MasaoC/GPS-TFT-Map_PONS/mysd.cpp

// ============================================================
// File    : mysd.cpp
// Project : PONS v7 (Pilot Oriented Navigation System for HPA)
// Role    : SDカード操作の実装（全処理はCore1で実行）。
//           SdFatライブラリによるファイル読み書き、
//           設定ファイル保存/読込、CSVフライトログ追記、
//           飛行CSVのリプレイ再生（列名索引パーサ・先読みリングバッファ）、
//           Core1タスクキューのエンキュー/デキュー管理。
//           地図画像(BMPタイル)のロードはベクタ地図への移行に伴い廃止した。
// Author  : MasaoC (@masao_mobile)
// Updated : 2026/10/06
// ============================================================
// SD card read and write programs.
// All process regarding SD card access are done in Core1.(#2 core)

#include <SPI.h>

#include "mysd.h"
#include "navdata.h"
#include "gnss.h"      // gnss_get_own_fix()（received/ に自機位置と距離を書くため）
#include "settings.h"
#include "imu.h"
//#define DISABLE_FS_H_WARNING
#include "SdFat.h"
#include "src/sound.h"
#include "attitude.h"
#include "link.h"

#define MAX_SETTING_LENGTH 32
#define MAX_LINE_LENGTH (MAX_SETTING_LENGTH * 2 + 2) // ID:value ペア + 区切り文字・改行のバッファサイズ


SdFs SD;                     // SdFat ライブラリのファイルシステムオブジェクト
volatile bool sdInitialized = false;  // SD カードの初期化が完了しているか（Core0/Core1 両方から参照）
volatile bool sdError = false;        // SD アクセス中にエラーが発生したか（Core0/Core1 両方から参照）
volatile bool sd_setup_complete = false;  // Core1 の setup_sd() が完了したことを示すフラグ（Core0 が待機に使用）
#define LOGFILE_NAME "log.txt"

// ---- 処理時間計測変数（BNO085配置コア決定用、デバッグビルドのみ） ----
#ifndef RELEASE
TimingStat ts_savecsv_flush = TSTAT_INIT("C1_savecsv_flush");
extern volatile bool c0_is_redrawing;  // Core0 描画中フラグ（重複検出用）
volatile uint32_t _c1_overlap_count = 0;  // Core0描画中にCore1重処理が重なった回数（Core1 が加算、Core0 が表示）
#endif

unsigned long lasttrytime_sd = 0; // SD エラー時の最後の再試行時刻（10秒ごとにリトライする）
bool headerWritten = false;       // CSV ファイルにヘッダ行を書いたか（1フライト1回だけ書く）

// CSV ファイル名の生成に使う起動時の日時（初回書き込み時に確定する）
int fileyear = 0;//意図的に0で初期化して、最初のGNSS時刻取得時に確定させる。変えるな。
int filemonth;
int fileday;
int filehour;
int fileminute;
int filesecond;


// ============================================================
// Core0↔Core1 間タスクキュー（ミューテックス保護）
//
// Core0（表示・GNSS・ボタン）から Core1（SD・音声）へ
// 非同期で処理を依頼するためのリングバッファ。
//   - enqueueTask(): Core0 がタスクを積む
//   - dequeueTask(): Core1 がタスクを取り出して実行
//   - taskQueueMutex でアトミック操作を保証
// ============================================================
TaskQueue taskQueue;               // タスクのリングバッファ本体
mutex_t taskQueueMutex;            // タスクキューへのアクセスを保護するミューテックス
Task currentTask;                  // Core1 が現在実行中のタスク（isTaskRunning() で参照）


void log_sd(const char* text);
void log_sdf(const char* format, ...);
void dateTime(uint16_t* date, uint16_t* time);



// ============================================================
// SD カード設定ファイル（settings.txt）の管理
//
// ファイル形式: テキスト、1 行に 1 項目、"id:value\n" の形式
//   例:
//     volume:50
//     destination:PLATHOME
//     navigation_mode:INTO
//     scaleindex:2
//
// SDSetting 構造体が id（識別子文字列）と setter/getter を持ち、
// loadSettings() / saveSettings() がこのテーブルを走査して一括処理する。
// 新しい設定項目を追加するときはこの配列に 1 行追加するだけでよい。
// ============================================================
// ---- PONS Link（機体⇄ボート無線）----
// 電波の ch / profile は「数値を保存するだけ」で、意味は無線層（e220.cpp）が決める。
// LoRa では ch = E220 のチャネル(CH0-12)、profile = SF のプリセット(0=SF7 … 4=SF11)。
void getLinkMode(char* b, size_t n)      { snprintf(b, n, "%u", link_mode_setting); }
void setLinkMode(const char* v) {
  int m = atoi(v);
  // 壊れた設定ファイルで機体が勝手に受信モードになる事故を防ぐため、
  // 範囲外は必ず OFF に倒す（docs/pons_link.md §1）。
  link_mode_setting = (m >= 0 && m <= LINK_MODE_RX) ? (uint8_t)m : LINK_MODE_OFF;
}
void getLinkRadioCh(char* b, size_t n)   { snprintf(b, n, "%u", link_radio_ch); }
void setLinkRadioCh(const char* v) {
  int c = atoi(v);
  if (c >= 0 && c <= LINK_RADIO_CH_MAX) link_radio_ch = (uint8_t)c;
}
void getLinkRadioProf(char* b, size_t n) { snprintf(b, n, "%u", link_radio_profile); }
void setLinkRadioProf(const char* v) {
  int p = atoi(v);
  if (p >= 0 && p < LINK_PROFILE_COUNT) link_radio_profile = (uint8_t)p;
}

// ★ グループ ID。**既定は 0 で、git に載る雛形も 0 のまま。**
//   実際の値は各機の SD カードにだけ置く（link_proto.h の設計方針）。
void getLinkGroup(char* b, size_t n)     { snprintf(b, n, "%u", link_group); }
void setLinkGroup(const char* v) {
  int g = atoi(v);
  link_group = (g >= 0 && g <= LINK_GROUP_MAX) ? (uint8_t)g : LINK_GROUP_DEFAULT;
}

SDSetting settings[] = {
  {"volume",          setVolume,         getVolume},
  {"vario_volume",    setVarioVolume,    getVarioVolume},
  {"vario_inhibit",   setVarioInhibit,   getVarioInhibit},
  {"destination",     setDestination,    getDestination},
  {"navigation_mode", setNavigationMode, getNavigationMode},
  {"scaleindex",      setScaleIndex,     getScaleIndex},
  {"upward_mode",     setUpwardMode,     getUpwardMode},
  {"kf_q_vel",        setKfQVel,         getKfQVel},
  {"kf_q_bias",       setKfQBias,        getKfQBias},
  {"kf_R",            setKfR,            getKfR},
  {"level_roll",      setLevelRoll,      getLevelRoll},
  {"level_pitch",     setLevelPitch,     getLevelPitch},
  {"pitch_target",    setPitchTarget,    getPitchTarget},
  {"rpy_functions",   setRpyFunctions,   getRpyFunctions},
  {"auto_roll_trim",  setAutoRollTrim,   getAutoRollTrim},
  {"wind_estimate",   setWindEstimate,   getWindEstimate},
  {"roll_target",     setRollTarget,     getRollTarget},
  {"needs_apply",     setNeedsApply,     getNeedsApply},
  {"calib_date",      setCalibDate,      getCalibDate},
  {"airspeed_v0",     setAirspeedV0,     getAirspeedV0},
  {"airspeed_k",      setAirspeedK,      getAirspeedK},
  {"airspeed_min",    setAirspeedMin,    getAirspeedMin},
  {"airspeed_max",    setAirspeedMax,    getAirspeedMax},
  {"roll_trim",       setRollTrim,       getRollTrim},
  {"auto10k_status",  setAuto10kStatus,  getAuto10kStatus},
  {"link_mode",       setLinkMode,       getLinkMode},
  {"link_radio_ch",   setLinkRadioCh,    getLinkRadioCh},
  {"link_radio_prof", setLinkRadioProf,  getLinkRadioProf},
  {"link_group",      setLinkGroup,      getLinkGroup}
};
const int numSettings = sizeof(settings) / sizeof(settings[0]);
extern volatile int sound_volume;
extern volatile int vario_volume;
extern volatile bool vario_inhibit;
extern int destination_mode;
extern volatile int scaleindex;  // 実体は GPS_TFT_map.ino（volatile）。宣言側も合わせる
extern double scalelist[6];
extern double scale;
extern int upward_mode;  // display_tft.cpp で定義。0=TRACKUP, 1=NORTHUP


// 全設定を settings.txt に保存する。
// 一度ファイルを削除してから新規書き込みすることで、
// 古い項目が残らないようにしている。
bool saveSettings() {
  SD.remove("settings.txt"); // 古いファイルを消してから書き直す
  FsFile file = SD.open("settings.txt", FILE_WRITE);
  if (!file) {
    DEBUGW_PLN(20250401,"Failed to open settings.txt for writing");
    return false;
  }

  char value[MAX_SETTING_LENGTH];
  for (int i = 0; i < numSettings; i++) {
    settings[i].getter(value, MAX_SETTING_LENGTH);
    file.print(settings[i].id);
    file.print(":");
    file.print(value);
    file.print("\n");//
  }

  file.close();
  DEBUG_PLN(20250401,"Settings saved to settings.txt");
  return true;
}


// settings.txt から設定を読み込み、各 setter を呼んで反映する。
// ファイルを 1 文字ずつ読んで行を組み立て、"id:value" 形式でパースする。
// ファイル末尾に改行がない場合も処理できるよう、ループ後に残余バッファをチェックする。
bool loadSettings() {
  FsFile file = SD.open("settings.txt", FILE_READ);
  if (!file) {
    DEBUGW_PLN(20250401,"Failed to open settings.txt for reading");
    return false;
  }

  char line[MAX_LINE_LENGTH];
  char settingId[MAX_SETTING_LENGTH];
  char value[MAX_SETTING_LENGTH];
  int linePos = 0;

  while (file.available()) {
    char c = file.read();
    // ★ CR も行の終わりとして扱う。**settings.txt は人が PC で編集する**
    //   （link_group など）ので、Windows のエディタが CRLF で保存すると値の末尾に
    //   \r が残る。atoi() を通す設定は無事だが、strcmp で比べるものが全部外れて
    //   ナビモード・目的地・vario_inhibit が黙って既定へ戻っていた。
    //   CRLF なら \r で行を切り、続く \n は空行（コロン無し）として捨てられる。
    if (c == '\n' || c == '\r' || linePos >= MAX_LINE_LENGTH - 1) {
      line[linePos] = '\0'; // Null-terminate the line
      linePos = 0;

      // Parse line into settingId and value
      char* colon = strchr(line, ':');
      if (colon) {
        *colon = '\0'; // Split at colon
        strncpy(settingId, line, MAX_SETTING_LENGTH);
        settingId[MAX_SETTING_LENGTH - 1] = '\0';
        strncpy(value, colon + 1, MAX_SETTING_LENGTH);
        value[MAX_SETTING_LENGTH - 1] = '\0';

        // Find and apply the setting
        for (int i = 0; i < numSettings; i++) {
          if (strcmp(settings[i].id, settingId) == 0) {
            settings[i].setter(value);
            break;
          }
        }
      }
    } else {
      line[linePos++] = c;
    }
  }



  // Handle last line if not newline-terminated
  if (linePos > 0) {
    line[linePos] = '\0';
    char* colon = strchr(line, ':');
    if (colon) {
      *colon = '\0';
      strncpy(settingId, line, MAX_SETTING_LENGTH);
      settingId[MAX_SETTING_LENGTH - 1] = '\0';
      strncpy(value, colon + 1, MAX_SETTING_LENGTH);
      value[MAX_SETTING_LENGTH - 1] = '\0';

      for (int i = 0; i < numSettings; i++) {
        if (strcmp(settings[i].id, settingId) == 0) {
          settings[i].setter(value);
          break;
        }
      }
    }
  }

  file.close();
  // 設定どうしの整合を取る（roll_trim と needs_apply の関係など）。
  // 行の順序に依存しないよう、全部読み終えてから呼ぶ。
  attitude_finish_settings_load();
  DEBUG_PLN(20250508,"Settings loaded from settings.txt");
  return true;
}



// ============================================================
// 設定項目ごとの setter / getter の実装
// setter: 文字列を受け取り、該当するグローバル変数に変換・格納する。
// getter: グローバル変数を文字列に変換して buffer に書き込む。
// ============================================================

// ============================================================
//  settings.txt の値を読む（検証つき）
// ============================================================
// ★ **atoi() / atof() を直接使ってはいけない。** どちらも数字でない文字列に 0 を返す。
//   音量では 0 が「消音」、角度では 0 がまっとうな値なので、行が壊れているだけなのに
//   黙って音が消える／ゼロ点が失われる。PONS は警報装置なので、これは一番避けたい。
//
// ★ **範囲外を丸めたときも必ずログに残す。** 丸めた結果がたまたま正常な値に見えると
//   （volume:-5 → 0 = 消音）、設定ミスに現場で気づけない。
//   「読めなかった」と「丸めた」を区別して log.txt へ書く。
//
// 戻り値: その値を採用してよいか（false = 既定値のまま残す）
static bool read_setting_int(const char* id, const char* value, int lo, int hi, int* out) {
  char* end = nullptr;
  const long v = strtol(value, &end, 10);
  if (end == value) {                               // 数字が 1 文字も無い
    enqueueTask(createLogSdfTask("ERR %s(%s) not a number", id, value));
    return false;
  }
  // 末尾の空白は許す。CR/LF は loadSettings() が行の区切りとして落としているが、
  // ここだけ見ても正しく動くようにしておく（保険）。
  while (*end == ' ' || *end == '\t' || *end == '\r' || *end == '\n') end++;
  if (*end != '\0') {                               // 数字のあとにゴミが付いている
    enqueueTask(createLogSdfTask("ERR %s(%s) not a number", id, value));
    return false;
  }
  if (v < lo || v > hi) {
    *out = (int)(v < lo ? lo : hi);
    enqueueTask(createLogSdfTask("ERR %s(%s) range %d..%d -> %d", id, value, lo, hi, *out));
    return true;                                    // 丸めた値は使う（捨てるより素直）
  }
  *out = (int)v;
  return true;
}

// 同じく float 版。角度の設定はこちらを通す。
// ★ strtod() は "nan" / "inf" を**正しくパースしてしまう**ので明示的に弾く。
//   NaN はどの比較も false になるため、しきい値の警告に一つも引っかからないまま
//   姿勢機能だけが死ぬ。範囲のクランプは attitude.cpp 側にもあるが（将来の
//   呼び出し元への保険）、ログを出せるのはここだけなので範囲もここで見る。
static bool read_setting_float(const char* id, const char* value, float lo, float hi, float* out) {
  char* end = nullptr;
  const double v = strtod(value, &end);
  bool bad = (end == value);
  if (!bad) {
    while (*end == ' ' || *end == '\t' || *end == '\r' || *end == '\n') end++;
    if (*end != '\0') bad = true;                   // 数字のあとにゴミ
    else if (v != v)   bad = true;                  // NaN
    else if (v > 1e30 || v < -1e30) bad = true;     // ±inf / 桁あふれ
  }
  if (bad) {
    enqueueTask(createLogSdfTask("ERR %s(%s) not a number", id, value));
    return false;
  }
  if (v < lo || v > hi) {
    *out = (float)(v < lo ? lo : hi);
    enqueueTask(createLogSdfTask("ERR %s(%s) range %.2f..%.2f -> %.2f",
                                 id, value, (double)lo, (double)hi, (double)*out));
    return true;
  }
  *out = (float)v;
  return true;
}

// 音量: 0〜SOUND_VOLUME_MAX。読めない値は既定値のまま残す（上のコメント参照）。
void setVolume(const char* value) {
  int v;
  if (!read_setting_int("volume", value, 0, SOUND_VOLUME_MAX, &v)) return;
  sound_volume = v;
  DEBUG_P(20250508,"Set volume to: ");
  DEBUG_PLN(20250508,sound_volume);
}

void getVolume(char* buffer, size_t bufferSize) {
  snprintf(buffer, bufferSize, "%d", sound_volume);
}

// バリオメーター音量: 0〜SOUND_VOLUME_MAX。こちらも読めない値は既定値のまま。
void setVarioVolume(const char* value) {
  int v;
  if (!read_setting_int("vario_volume", value, 0, SOUND_VOLUME_MAX, &v)) return;
  vario_volume = v;
}

void getVarioVolume(char* buffer, size_t bufferSize) {
  snprintf(buffer, bufferSize, "%d", vario_volume);
}

// バリオ抑止フラグ: "true" なら vario を完全無効化する（SDカード手動設定のみ）
void setVarioInhibit(const char* value) {
  vario_inhibit = (strcmp(value, "true") == 0);
}
void getVarioInhibit(char* buffer, size_t bufferSize) {
  snprintf(buffer, bufferSize, "%s", vario_inhibit ? "true" : "false");
}

// ナビゲーションモード: "INTO" / "AWAY" / "AUTO10K" を destination_mode 定数に変換
void setNavigationMode(const char *value){
  if(strcmp(value,"INTO") == 0){
    destination_mode = DMODE_FLYINTO;
  }
  else if(strcmp(value,"AWAY") == 0){
    destination_mode = DMODE_FLYAWAY;
  }
  else if(strcmp(value,"AUTO10K") == 0){
    destination_mode = DMODE_AUTO10K;
  }else{
    DEBUGW_PLN(20250509,"ERR MODE");
  }
}
void getNavigationMode(char* buffer, size_t bufferSize) {
  if(bufferSize <= 0)
    return;
  if(destination_mode == DMODE_FLYINTO)
    strncpy(buffer,"INTO", bufferSize);
  else if(destination_mode == DMODE_FLYAWAY)
    strncpy(buffer,"AWAY", bufferSize);
  else if(destination_mode == DMODE_AUTO10K)
    strncpy(buffer,"AUTO10K", bufferSize);
  buffer[bufferSize - 1] = '\0';
}

// 目的地: 名前で extradestinations を線形探索して currentdestination インデックスを設定する。
// 見つからない場合はエラーログを残す。
void setDestination(const char* value) {
  for(int i = 0; i < destinations_count; i++){
    if(strcmp(extradestinations[i].name,value) == 0){
      currentdestination = i;
      return;
    }
  }
  DEBUGW_P(20250508,"ERR DEST:");
  DEBUGW_PLN(20250508,value);
  enqueueTask(createLogSdfTask("ERR setDestination(%s)",value));
}


void getScaleIndex(char* buffer, size_t bufferSize) {
  if(bufferSize <= 0)
    return;
  snprintf(buffer, bufferSize, "%d", scaleindex);
}

void setScaleIndex(const char* value) {
  int indexofsetting = atoi(value);
  if(indexofsetting >= 0 && indexofsetting < (sizeof(scalelist) / sizeof(scalelist[0]))){
    scaleindex = indexofsetting;
    scale = scalelist[scaleindex];
  }else{
    DEBUGW_P(20250508,"ERR scale index:");
    DEBUGW_PLN(20250508,indexofsetting);
    enqueueTask(createLogSdfTask("ERR scale index(%s)",value));
  }
}

// 地図方向モード（NORTHUP=1 / TRACKUP=0）の getter / setter
void getUpwardMode(char* buffer, size_t bufferSize) {
  if (bufferSize <= 0) return;
  snprintf(buffer, bufferSize, "%d", upward_mode);
}

void setUpwardMode(const char* value) {
  int mode = atoi(value);
  if (mode >= 0 && mode < 2) {  // 0=TRACKUP, 1=NORTHUP
    upward_mode = mode;
  }
}

// Kalman フィルター係数: 速度プロセスノイズ（デフォルト KF_Q_VEL）
void setKfQVel(const char* value) {
  float v = atof(value);
  if (v > 0.0f) imu_set_kf_params(v, get_imu_kf_q_bias(), get_imu_kf_R());
}
void getKfQVel(char* buffer, size_t bufferSize) {
  snprintf(buffer, bufferSize, "%.6g", get_imu_kf_q_vel());
}

// Kalman フィルター係数: バイアスプロセスノイズ（デフォルト KF_Q_BIAS）
void setKfQBias(const char* value) {
  float v = atof(value);
  if (v > 0.0f) imu_set_kf_params(get_imu_kf_q_vel(), v, get_imu_kf_R());
}
void getKfQBias(char* buffer, size_t bufferSize) {
  snprintf(buffer, bufferSize, "%.6g", get_imu_kf_q_bias());
}

// Kalman フィルター係数: 気圧高度観測ノイズ [m²]（デフォルト KF_R）
void setKfR(const char* value) {
  float v = atof(value);
  if (v > 0.0f) imu_set_kf_params(get_imu_kf_q_vel(), get_imu_kf_q_bias(), v);
}
void getKfR(char* buffer, size_t bufferSize) {
  snprintf(buffer, bufferSize, "%.6g", get_imu_kf_R());
}

// ---- 機体ゼロ点（マウント基準）のオフセット [度] ----
// マウント形状は固定なので、据え付け後に一度較正すれば以後は使い回せる。
// 設定画面の "Set Level 0deg" で更新し、ここで SD に永続化する。
void setLevelRoll(const char* value) {
  float v;
  if (!read_setting_float("level_roll", value,
                          -LEVEL_OFFSET_LIMIT_DEG, LEVEL_OFFSET_LIMIT_DEG, &v)) return;
  float r, p;
  attitude_get_level_offset(r, p);
  attitude_set_level_offset(v, p);
}
void getLevelRoll(char* buffer, size_t bufferSize) {
  float r, p; attitude_get_level_offset(r, p);
  snprintf(buffer, bufferSize, "%.3f", r);
}
void setLevelPitch(const char* value) {
  float v;
  if (!read_setting_float("level_pitch", value,
                          -LEVEL_OFFSET_LIMIT_DEG, LEVEL_OFFSET_LIMIT_DEG, &v)) return;
  float r, p;
  attitude_get_level_offset(r, p);
  attitude_set_level_offset(r, v);
}

// 較正時に申告するピッチ角（IMU/ESKF 画面の SET PITCH 行の値）。
// 本番プラットホームは -3.5 度など決まった値を使うので、
// 毎回選び直さずに済むよう保存する。
void setPitchTarget(const char* value) {
  float v;
  if (!read_setting_float("pitch_target", value,
                          PITCH_TARGET_MIN_DEG, PITCH_TARGET_MAX_DEG, &v)) return;
  attitude_set_pitch_target(v);
}

// APPLY 時に申告するロール角（通常 0）
void setRollTarget(const char* value) {
  float v;
  if (!read_setting_float("roll_target", value,
                          ROLL_TARGET_MIN_DEG, ROLL_TARGET_MAX_DEG, &v)) return;
  attitude_set_roll_target(v);
}
void getRollTarget(char* buffer, size_t bufferSize) {
  snprintf(buffer, bufferSize, "%.1f", attitude_get_roll_target());
}

// マウントから外されたまま APPLY されていない状態。
// 充電のために電源を切っても保持したいので SD に残す。
void setNeedsApply(const char* value) { attitude_set_needs_apply(atoi(value) != 0); }
// 自動ロールトリムの累積補正量。取り付けのズレは電源を切っても変わらないので保存する。
// ただし needs_apply が立っている（マウントから外した）場合は
// attitude_finish_settings_load() が読み込み後に捨てる。
void setRollTrim(const char* value) {
  float v;
  if (!read_setting_float("roll_trim", value,
                          -ROLL_TRIM_LIMIT_DEG, ROLL_TRIM_LIMIT_DEG, &v)) return;
  attitude_set_roll_trim_deg(v);
}
// AUTO10K の折返しフェーズ。飛行中に再起動しても復路のナビ方位が 180 度逆に
// ならないよう保存する（距離だけでは往路と復路を区別できないため）。
// 保存されるのは実飛行の遷移だけで、リプレイ再生中の遷移は書き込まれない。
void setAuto10kStatus(const char* value) {
  restore_auto10k_status(strcmp(value, "INTO") == 0 ? AUTO10K_INTO : AUTO10K_AWAY);
}
void getAuto10kStatus(char* buffer, size_t bufferSize) {
  strncpy(buffer, get_auto10k_status_flight() == AUTO10K_INTO ? "INTO" : "AWAY", bufferSize);
  buffer[bufferSize - 1] = '\0';
}
void getRollTrim(char* buffer, size_t bufferSize) {
  snprintf(buffer, bufferSize, "%.3f", attitude_get_roll_trim_deg());
}
void getNeedsApply(char* buffer, size_t bufferSize) {
  snprintf(buffer, bufferSize, "%d", attitude_needs_apply() ? 1 : 0);
}

// 最後に APPLY した日（JST の YYYYMMDD、0 = 不明）。
// これを保存する目的は「電源を切っている間にマウントから外された」を拾うこと。
// OFF_MOUNT 判定は ESKF が回っている間しか働かないので、電源 OFF 中の取り外しは
// needs_apply には現れない。日付だけは残しておけば、次の起動で日をまたいだと分かる。
// 値の妥当性検査は attitude_set_calib_date() 側で行う（壊れた設定ファイル対策）。
void setCalibDate(const char* value) {
  attitude_set_calib_date((uint32_t)strtoul(value, nullptr, 10));
}
void getCalibDate(char* buffer, size_t bufferSize) {
  snprintf(buffer, bufferSize, "%lu", (unsigned long)attitude_get_calib_date());
}

// ---- 対気速度の推定モデル V(θ) = V0 * sqrt(K / (K + θ)) ----
// 機体・重量・重心で変わるので、機体ごとに SD で設定できるようにしてある。
// 既定は settings.h の AIRSPEED_*。範囲外は read_setting_float() が端でクランプし、
// 理由を log.txt に残す（黙って既定へ戻すと、書いたつもりで効いていない状態になる）。
// 読み込み後の実効値は setup_sd() が AIRSPEED MODEL 行としてログに残す。
//
// ★ 範囲は「人力飛行機として明らかにあり得ない値を弾く」ためのもので、
//   細かい調整を妨げない広さにしてある。
//   airspeed_k は 0 に近づけると分母が消えて発散するので下限を離してある。
void setAirspeedV0(const char* value) {
  float v;
  if (read_setting_float("airspeed_v0", value, 3.0f, 20.0f, &v))
    attitude_set_airspeed_v0(v);
}
void getAirspeedV0(char* buffer, size_t bufferSize) {
  snprintf(buffer, bufferSize, "%.2f", attitude_get_airspeed_v0());
}
void setAirspeedK(const char* value) {
  float v;
  if (read_setting_float("airspeed_k", value, 3.0f, 60.0f, &v))
    attitude_set_airspeed_k(v);
}
void getAirspeedK(char* buffer, size_t bufferSize) {
  snprintf(buffer, bufferSize, "%.2f", attitude_get_airspeed_k());
}
void setAirspeedMin(const char* value) {
  float v;
  if (read_setting_float("airspeed_min", value, 1.0f, 20.0f, &v))
    attitude_set_airspeed_min(v);
}
void getAirspeedMin(char* buffer, size_t bufferSize) {
  snprintf(buffer, bufferSize, "%.2f", attitude_get_airspeed_min());
}
void setAirspeedMax(const char* value) {
  float v;
  if (read_setting_float("airspeed_max", value, 1.0f, 25.0f, &v))
    attitude_set_airspeed_max(v);
}
void getAirspeedMax(char* buffer, size_t bufferSize) {
  snprintf(buffer, bufferSize, "%.2f", attitude_get_airspeed_max());
}

// Roll/Pitch/Yaw 機能のマスタースイッチ（IMU/ESKF 画面で切替）
void setRpyFunctions(const char* value) { attitude_set_rpy_enabled(atoi(value) != 0); }
void getRpyFunctions(char* buffer, size_t bufferSize) {
  snprintf(buffer, bufferSize, "%d", attitude_get_rpy_enabled() ? 1 : 0);
}

// 風推定の有効/無効
void setWindEstimate(const char* value) { attitude_set_wind_enabled(atoi(value) != 0); }
void getWindEstimate(char* buffer, size_t bufferSize) {
  snprintf(buffer, bufferSize, "%d", attitude_get_wind_enabled() ? 1 : 0);
}

// 直進中のロール自動トリムの有効/無効
void setAutoRollTrim(const char* value) { attitude_set_roll_trim_enabled(atoi(value) != 0); }
void getAutoRollTrim(char* buffer, size_t bufferSize) {
  snprintf(buffer, bufferSize, "%d", attitude_get_roll_trim_enabled() ? 1 : 0);
}
void getPitchTarget(char* buffer, size_t bufferSize) {
  snprintf(buffer, bufferSize, "%.1f", attitude_get_pitch_target());
}
void getLevelPitch(char* buffer, size_t bufferSize) {
  float r, p; attitude_get_level_offset(r, p);
  snprintf(buffer, bufferSize, "%.3f", p);
}

void getDestination(char* buffer, size_t bufferSize) {
  if(bufferSize <= 0)
    return;
  // 目的地が未選択（起動直後は -1）なら配列外アクセスになるため空文字列を返す
  if(currentdestination < 0 || currentdestination >= destinations_count){
    buffer[0] = '\0';
    return;
  }
  strncpy(buffer, extradestinations[currentdestination].name, bufferSize);
  buffer[bufferSize - 1] = '\0';
}


// 現在 Core1 が実行中のタスクが指定タイプかを確認する（Core0 から呼ばれる）。
// currentTask は dequeueTask() が mutex 内で丸ごと上書きするため、読む側も mutex で揃える。
bool isTaskRunning(int taskType) {
  mutex_enter_blocking(&taskQueueMutex);
  bool running = (currentTask.type == taskType);
  mutex_exit(&taskQueueMutex);
  return running;
}

// Core1 がタスクを処理し終えたことを記録する（mutex 内で書くことで isTaskRunning() と整合させる）
void clearCurrentTask() {
  mutex_enter_blocking(&taskQueueMutex);
  currentTask.type = TASK_NONE;
  mutex_exit(&taskQueueMutex);
}

// キュー内に指定タイプのタスクが存在するかを確認する（head〜tail を線形探索）。
// ループ内で return せず found に受けてから抜ける（mutex の解放漏れを防ぐため）。
bool isTaskInQueue(int taskType){
    bool found = false;
    mutex_enter_blocking(&taskQueueMutex);
    int current = taskQueue.head;
    while (current != taskQueue.tail) {
        if (taskQueue.tasks[current].type == taskType) {
            found = true;
            break;
        }
        current = (current + 1) % TASK_QUEUE_SIZE;
    }
    mutex_exit(&taskQueueMutex);
    return found;
}

// ============================================================
// タスク生成ファクトリ関数（create〜Task）
//
// 各タスクは Task 構造体として表現され、
// type フィールドで種別を識別し、union のフィールドで引数を渡す。
// Core0 がこれらを呼んで enqueueTask() に渡し、Core1 がデキューして実行する。
// ============================================================

// 設定ファイル保存タスクを生成する
Task createSaveSettingTask(){
  Task task;
  task.type = TASK_SAVE_SETTINGS;
  return task;
}


// テキストをログファイルに書き込むタスクを生成する
Task createLogSdTask(const char* logText) {
  Task task;
  task.type = TASK_LOG_SD;
  task.logText = logText;
  return task;
}

// printf 形式のフォーマット文字列でログタスクを生成する（可変引数対応）
Task createLogSdfTask(const char* format, ...) {
  Task task;
  task.type = TASK_LOG_SDF;
  va_list args;
  va_start(args, format);
  vsnprintf(task.logSdfArgs.buffer, sizeof(task.logSdfArgs.buffer), format, args);
  va_end(args);
  task.logSdfArgs.format = "%s";
  return task;
}


// 無線で受信した 1 フレームを received/ へ書き出すタスクを生成する。
// 自機のフライト CSV とは**別のファイル・別のハンドル**にしてある。
//
// ★ 「received/ には無線で得た情報だけ」という原則の**唯一の例外**として、
//   受信した瞬間のボート自身の位置（own_lat/own_lon）と機体までの距離（dist_m）を
//   同じ行に入れる。RSSI と距離が 1 行に揃っていないと「距離 vs RSSI」が引けず、
//   別ファイルに分けると seq で突き合わせる手間が増えるため。
//   リプレイは列名で解釈するので、列が増えても既存の再生は壊れない。
Task createSaveRxCsvTask(const LinkTelem* t, int rssi, uint16_t age_ms) {
  Task task;
  task.type = TASK_SAVE_RXCSV;
  task.saveCsvArgs.latitude      = t->lat_1e7 / 1e7;
  task.saveCsvArgs.longitude     = t->lon_1e7 / 1e7;
  task.saveCsvArgs.gs            = t->gs_cms / 100.0f;
  task.saveCsvArgs.ttrack        = (int)(t->track_cdeg / 100);
  task.saveCsvArgs.gnss_altitude = t->gnss_alt_dm / 10.0f;
  task.saveCsvArgs.kf_altitude   = t->kf_alt_dm / 10.0f;
  task.saveCsvArgs.kf_vspeed     = t->kf_vs_cms / 100.0f;
  task.saveCsvArgs.pressure      = t->press_dpa / 10.0f;
  task.saveCsvArgs.voltage       = link_unpack_volt(t->volt_cv);
  task.saveCsvArgs.numsat        = t->numsat;
  task.saveCsvArgs.year   = t->year;   task.saveCsvArgs.month  = t->month;
  task.saveCsvArgs.day    = t->day;    task.saveCsvArgs.hour   = t->hour;
  task.saveCsvArgs.minute = t->minute; task.saveCsvArgs.second = t->second;
  task.saveCsvArgs.centisecond = t->centi;
  // ボート自身の位置と機体までの距離。測位できていなければ空欄で書く。
  {
    double olat, olon, ogs, otrk;
    task.saveCsvArgs.own_valid = gnss_get_own_fix(olat, olon, ogs, otrk);
    if (task.saveCsvArgs.own_valid) {
      task.saveCsvArgs.own_lat = (float)olat;
      task.saveCsvArgs.own_lon = (float)olon;
      // 機体側の位置が無効（未測位）なら距離も意味が無いので出さない。
      if (t->fixflags & 0x01) {
        task.saveCsvArgs.dist_m = (float)(calculateDistanceKm(
            olat, olon, t->lat_1e7 / 1e7, t->lon_1e7 / 1e7) * 1000.0);
      } else {
        task.saveCsvArgs.dist_m = NAN;
      }
    } else {
      task.saveCsvArgs.own_lat = task.saveCsvArgs.own_lon = NAN;
      task.saveCsvArgs.dist_m  = NAN;
    }
  }
  task.saveCsvArgs.rssi   = rssi;
  task.saveCsvArgs.seq    = t->seq;
  task.saveCsvArgs.age_ms = age_ms;

  // ★ 姿勢・風も残す。**機体の SD が死んだとき、ここが唯一の記録になる**
  //   （status の LINK_ST_SD_ERROR はまさにその状態を知らせるためにある）。
  //   ESKF の開発でも使うので、単位と列名は imu_replaydata/ に合わせる。
  //   入っていない項目は書き出し側で空欄にするので、ここでは have をそのまま運ぶ。
  task.saveCsvArgs.have      = t->have;
  task.saveCsvArgs.roll      = t->roll_cdeg      * 0.01f;
  task.saveCsvArgs.pitch     = t->pitch_cdeg     * 0.01f;
  task.saveCsvArgs.yaw       = t->yaw_cdeg       * 0.01f;
  task.saveCsvArgs.pitch_avg = t->pitch_avg_cdeg * 0.01f;
  task.saveCsvArgs.roll_trim = t->roll_trim_cdeg * 0.01f;
  task.saveCsvArgs.yaw_acc95 = (float)t->yaw_acc95_deg;
  task.saveCsvArgs.wind_mps  = t->wind_dmps      * 0.1f;
  task.saveCsvArgs.wind_dir  = t->wind_dir_cdeg  * 0.01f;
  return task;
}

// 1 フレーム分の GNSS データを CSV ログに書き込むタスクを生成する
// ※ own_* / dist_m は received/ 専用。ここでは使わないが、未初期化のまま
//   残さないよう明示的に潰しておく（同じ共用体を使い回すため）。
Task createSaveCsvTask(float latitude, float longitude, float gs, int ttrack, float gnss_altitude, float kf_altitude, float kf_vspeed, float pressure, float voltage, int numsat, int year, int month, int day, int hour, int minute, int second, int centisecond) {
  Task task;
  task.type = TASK_SAVE_CSV;
  task.saveCsvArgs.latitude = latitude;
  task.saveCsvArgs.longitude = longitude;
  task.saveCsvArgs.gs = gs;
  task.saveCsvArgs.ttrack = ttrack;
  task.saveCsvArgs.gnss_altitude = gnss_altitude;
  task.saveCsvArgs.kf_altitude = kf_altitude;
  task.saveCsvArgs.kf_vspeed  = kf_vspeed;
  task.saveCsvArgs.pressure = pressure;
  task.saveCsvArgs.voltage = voltage;
  task.saveCsvArgs.numsat = numsat;
  task.saveCsvArgs.year = year;
  task.saveCsvArgs.month = month;
  task.saveCsvArgs.day = day;
  task.saveCsvArgs.hour = hour;
  task.saveCsvArgs.minute = minute;
  task.saveCsvArgs.second = second;
  task.saveCsvArgs.centisecond = centisecond;
  return task;
}


Task createPlayMultiToneTask(int freq, int duration, int count,int priority,int min_volume,bool solo_play){
  Task task;
  task.type = TASK_PLAY_MULTITONE;
  task.playMultiToneArgs.freq = freq;
  task.playMultiToneArgs.duration = duration;
  task.playMultiToneArgs.counter = count;
  task.playMultiToneArgs.priority = priority;
  task.playMultiToneArgs.min_volume = min_volume;
  task.playMultiToneArgs.solo_play = solo_play;
  return task;
}

Task createPlayWavTask(const char* filename, int priority, int min_volume, int excl_group){
  Task task;
  task.type = TASK_PLAY_WAV;
  task.playWavArgs.wavfilename = filename;
  task.playWavArgs.priority = priority;
  task.playWavArgs.min_volume = min_volume;
  task.playWavArgs.excl_group = excl_group;
  return task;
}


Task createBrowseSDTask(int page){
  Task task;
  task.type = TASK_BROWSE_SD;
  task.pagenum = page;
  return task;
}


// リプレイ選択画面のファイル一覧取得タスク。
// browse_sd() と違い「ページ番号」ではなく「対象CSVの通し番号の開始位置」を渡す
// （リストの先頭に固定項目が並ぶため、ページ境界と一覧のインデックスがずれる）。
Task createBrowseReplayTask(int start_index){
  Task task;
  task.type = TASK_BROWSE_REPLAY;
  task.pagenum = start_index;
  return task;
}


Task createLoadReplayTask(){
  Task task;
  task.type = TASK_LOAD_REPLAY;
  return task;
}

Task createInitReplayTask(){
  Task task;
  task.type = TASK_INIT_REPLAY;
  return task;
}


// キュー内の指定タイプのタスクを全て除去する（重複防止用）。
// in-place 削除: read ポインタで走査し、対象でない要素だけ write 位置に詰める。
// ★ max_priority は **これ以下の優先度のものだけ消す** という上限。
//   種別だけで消すと、音量確認音（優先度 1）がコース逸脱警報や Auto10km の
//   折返しチャイム（優先度 2/3）まで巻き添えで消してしまう。
//   0.965 で警報が画面によらず鳴るようになったので、設定画面で音量をいじっている
//   最中に警報が来る組み合わせが現実に起こる。
//   既定の INT_MAX は従来どおり「種別が同じなら全部消す」。
void removeDuplicateTask(TaskType type, int max_priority) {
    mutex_enter_blocking(&taskQueueMutex);

    if (taskQueue.head == taskQueue.tail) {
        mutex_exit(&taskQueueMutex);
        return;  // キューが空
    }

    int read = taskQueue.head;
    int write = taskQueue.head;

    while (read != taskQueue.tail) {
        // 消す条件を組み立てる。★ 優先度は共用体の中にあるので、**種別が一致した
        //   ときだけ読むこと。**先に読むと別種別のタスクの別のメンバを読むことになる。
        bool remove = (taskQueue.tasks[read].type == type);
        if (remove && type == TASK_PLAY_MULTITONE) {
            remove = (taskQueue.tasks[read].playMultiToneArgs.priority <= max_priority);
        }
        if (!remove) {
            if (write != read) {
                taskQueue.tasks[write] = taskQueue.tasks[read];
            }
            write = (write + 1) % TASK_QUEUE_SIZE;
        }
        read = (read + 1) % TASK_QUEUE_SIZE;
    }

    taskQueue.tail = write;  // 新しい末尾位置（削除後）
    mutex_exit(&taskQueueMutex);
}

// キュー内の同種タスクを削除してから追加する。
// 以前は地図画像ロードの中断処理も担っていたが、
// ベクタ地図への移行で地図画像ロードが無くなったため、重複排除だけが残っている。
bool enqueueTaskWithAbortCheck(Task newTask) {
  // 自分と同じか、自分より低い優先度のものだけ消す（上のコメント参照）。
  const int prio = (newTask.type == TASK_PLAY_MULTITONE)
                 ? newTask.playMultiToneArgs.priority : INT_MAX;
  removeDuplicateTask(newTask.type, prio);
  return enqueueTask(newTask);
}

extern volatile bool userled_forced_on;  // GPS_TFT_map.ino で定義

// タスクをリングバッファに追加する（ミューテックス保護）。
// バッファが満杯の場合は追加せずにスキップする（タスクロスト）。
// タスクロスト時は USERLED_PIN を永続点灯してエラーを通知する。
//
// 戻り値: キューに入れられたら true、満杯で捨てたら false。
// ※ 捨てられたタスクは二度と実行されない。後始末が必要な呼び出し側
//   （生 IMU ログのバッファ解放など）は必ず戻り値を確認すること。
bool enqueueTask(Task task) {
  bool queued = false;
  mutex_enter_blocking(&taskQueueMutex);
  int nextTail = (taskQueue.tail + 1) % TASK_QUEUE_SIZE;
  if (nextTail != taskQueue.head) {  // キューに空きがある場合だけ追加
    taskQueue.tasks[taskQueue.tail] = task;
    taskQueue.tail = nextTail;
    queued = true;
  } else {
    userled_forced_on = true;         // 永続点灯フラグを立てる（loop_userled がフラッシュで消さないよう保護）
    digitalWrite(USERLED_PIN, HIGH);  // キュー満杯によるタスクロスト → LED 永続点灯
    // ※ mutex 保持中のため enqueueTask() の再帰呼び出し不可。Serial 出力のみ。
    Serial.println("ERR: task queue full, task dropped");
  }
  mutex_exit(&taskQueueMutex);
  return queued;
}

// タスクをリングバッファから取り出す（ミューテックス保護）。
// 取り出せた場合は *task に格納して true を返す、空なら false を返す。
bool dequeueTask(Task* task) {
  bool success = false;
  mutex_enter_blocking(&taskQueueMutex);
  if (taskQueue.head != taskQueue.tail) {  // キューが空でない
    *task = taskQueue.tasks[taskQueue.head];
    taskQueue.head = (taskQueue.head + 1) % TASK_QUEUE_SIZE;
    success = true;
  }
  mutex_exit(&taskQueueMutex);
  return success;
}

// mapdata.csv の 1 行を解析して extramaps[] に追加する。
// CSV 形式: "ポリゴン名,頂点数,lon1,lat1,lon2,lat2,..."
void process_mapcsv_line(String line) {
  int index = 0;
  int commaIndex = line.indexOf(',');
  String name = line.substring(index, commaIndex);
  index = commaIndex + 1;

  commaIndex = line.indexOf(',', index);
  int size = line.substring(index, commaIndex).toInt();
  index = commaIndex + 1;

  // 頂点数は CSV の値をそのまま使うため、確保前に必ず妥当性を確認する。
  // 座標 1 組は最短でも "0,0," の 4 文字を要するので、行の長さから上限を求められる。
  // これを怠ると壊れた mapdata.csv（巨大な値・負の値）で new が失敗し、
  // -fno-exceptions ビルドでは throw ではなく abort() して起動不能になる。
  if (size <= 0 || size > (int)(line.length() / 4)) {
    DEBUGW_P(20260806, "ERR mapcsv invalid size:");
    DEBUGW_PLN(20260806, size);
    return;
  }

  // Allocate memory for the coordinates
  double (*cords)[2] = new double[size][2];
  if (cords == nullptr) {  // nothrow 版 new の場合に備える
    return;
  }

  for (int i = 0; i < size; i++) {
    commaIndex = line.indexOf(',', index);
    if (commaIndex == -1 && i < size - 1) {
      delete[] cords;
      return;
    }
    cords[i][0] = line.substring(index, commaIndex).toDouble();
    index = commaIndex + 1;
    commaIndex = line.indexOf(',', index);
    if (commaIndex == -1 && i < size - 1) {
      delete[] cords;
      return;
    }
    cords[i][1] = line.substring(index, commaIndex).toDouble();
    index = commaIndex + 1;
  }

  extramaps[mapdata_count].id = current_id++;
  extramaps[mapdata_count].name = pons_strdup(name.c_str()); // Duplicate string to allocate memory
  extramaps[mapdata_count].size = size;
  extramaps[mapdata_count].cords = cords;
  mapdata_count++;
}


// destinations.csv の 1 行を解析して extradestinations[] に追加する。
// CSV 形式: "目的地名,緯度,経度"（1 行 1 地点）。ヘッダ行は無い。
//
// ★ **壊れた行は必ずここで捨てる。**
//   以前は頂点数を size=1 に固定したまま、ガード条件だけ複数頂点用の
//   (i < size - 1) が残っていた。size=1 では i < 0 なので**ガードが一度も成立せず**、
//   コンマの無い行が「名前＝行全体・座標 (0,0)」の目的地として登録されていた。
//   （Arduino の String::substring() は引数が unsigned なので、-1 を渡すと
//     エラーではなく行全体が返る。だから誰も気づかないまま通っていた。）
//   これを選ぶと誘導がギニア湾を指し、目的地が遠すぎる警告が鳴り続ける。
//   判定基準は override_pilon_coordinate.csv と揃えてある。
//
// 戻り値: 登録したら true、行を捨てたら false（呼び出し側が件数を数えてログに残す）
bool process_destinationcsv_line(String line) {
  // --- 3 列そろっているか ---
  const int c1 = line.indexOf(',');
  if (c1 <= 0) return false;                    // コンマが無い / 名前が空
  const int c2 = line.indexOf(',', c1 + 1);
  if (c2 < 0) return false;                     // 経度が無い

  String name = line.substring(0, c1);
  String slat = line.substring(c1 + 1, c2);
  String slon = line.substring(c2 + 1);
  name.trim(); slat.trim(); slon.trim();
  if (name.length() == 0 || slat.length() == 0 || slon.length() == 0) return false;

  // --- 明らかな打ち間違いを弾く ---
  const double lat = slat.toDouble();
  const double lon = slon.toDouble();
  if (lat < -90.0 || lat > 90.0 || lon < -180.0 || lon > 180.0) return false;
  if (lat == 0.0 && lon == 0.0) return false;   // toDouble() は数値でない文字列でも 0 を返す

  // 目的地は 1 点だけ持つ。cords[0][0]=緯度 / cords[0][1]=経度
  //（地図ポリゴンの create_static_mapdata() とは順序が逆なので注意）
  double (*cords)[2] = new double[1][2];
  if (cords == nullptr) return false;           // nothrow 版 new の場合に備える
  cords[0][0] = lat;
  cords[0][1] = lon;

  extradestinations[destinations_count].id = current_id++;
  extradestinations[destinations_count].name = pons_strdup(name.c_str());
  extradestinations[destinations_count].size = 1;
  extradestinations[destinations_count].cords = cords;
  destinations_count++;
  return true;
}

// SD カードの mapdata.csv から地図ポリゴンを読み込み extramaps[] に格納する。
// メモリリーク防止のため 1 回だけ実行する（mapdatainitialized フラグで管理）。
bool mapdatainitialized = false;
void init_mapdata() {
  if(mapdatainitialized){
    DEBUG_PLN(20241006,"Map already initialized.");
    return; // 2 回目以降はスキップ（重複ロードによるメモリリークを防ぐ）
  }
  FsFile myFile = SD.open("mapdata.csv");
  if (!myFile) {
    return;
  }
  while (myFile.available() && mapdata_count < MAX_MAPDATAS) {
    String line = myFile.readStringUntil('\n');
    line.trim();
    if (line.length() > 0) {
      process_mapcsv_line(line);
    }
  }
  myFile.close();
  mapdatainitialized = true;
}


// SD カードの destinations.csv から目的地を読み込み extradestinations[] に追加する。
// init_destinations() で固定目的地を登録した後に呼ぶことで、SD 側の追加目的地を上書きせず後ろに追加できる。
// ===== パイロン座標の上書き（override_pilon_coordinate.csv）=====
// パイロンの座標は毎年変わり得るが、大会直前にファームウェアを再ビルドするのは難しい。
// SD のトップに override_pilon_coordinate.csv があれば、起動時にその値で上書きする。
//
//   # で始まる行と空行は無視
//   NAME,緯度,経度   の 1 行 1 地点。書かれた地点だけが上書きされる。
//   NAME: PLATHOME / N_PILON / S_PILON / PILON_1KM / TAKESHIMA
//
// 上書きは navdata.cpp の実行時変数に対して行う。目的地リスト・地図上のアイコン・
// 基準線がすべてこの変数を見るので、1 か所直せば全部が一致して変わる。
// ※ Auto 10km の折り返し判定は「選択中の目的地からの距離」で行うので、
//   パイロン座標ではなく PLATHOME の座標が効く。
static bool apply_pilon_override(const char* name, double lat, double lon) {
  // 明らかな打ち間違いを弾く。ここを通ると誘導が丸ごと狂うため。
  if (lat < -90.0 || lat > 90.0 || lon < -180.0 || lon > 180.0) return false;
  if (lat == 0.0 && lon == 0.0) return false;
  if      (!strcmp(name, "PLATHOME"))  { pla_lat = lat;         pla_lon = lon; }
  else if (!strcmp(name, "N_PILON"))   { pilon_north_lat = lat; pilon_north_lon = lon; }
  else if (!strcmp(name, "S_PILON"))   { pilon_south_lat = lat; pilon_south_lon = lon; }
  else if (!strcmp(name, "PILON_1KM")) { pilon_1km_lat = lat;   pilon_1km_lon = lon; }
  else if (!strcmp(name, "TAKESHIMA")) { takeshima_lat_v = lat; takeshima_lon_v = lon; }
  else return false;
  log_sdf("PILON OVERRIDE %s %.6f %.6f", name, lat, lon);
  return true;
}

void load_pilon_override(){
  FsFile f = SD.open("override_pilon_coordinate.csv");
  if (!f) return;
  int applied = 0, rejected = 0;
  char line[80];
  while (f.fgets(line, sizeof(line)) > 0) {
    char* p = line;
    while (*p == ' ' || *p == '\t') p++;
    if (*p == '#' || *p == '\r' || *p == '\n' || *p == '\0') continue;
    char name[16];
    double lat = 0.0, lon = 0.0;
    if (sscanf(p, "%15[^,],%lf,%lf", name, &lat, &lon) != 3) { rejected++; continue; }
    // 名前の末尾の空白を落とす
    for (int i = (int)strlen(name) - 1; i >= 0 && (name[i]==' '||name[i]=='\t'); i--) name[i] = '\0';
    if (apply_pilon_override(name, lat, lon)) applied++;
    else rejected++;
  }
  f.close();
  if (applied > 0) pilon_override_loaded = true;
  log_sdf("PILON OVERRIDE: %d applied, %d ignored", applied, rejected);
}

void load_destinations(){
  FsFile myFile = SD.open("destinations.csv");
  if (!myFile) {
    return;
  }
  int added = 0, rejected = 0;
  while (myFile.available() && destinations_count < MAX_DESTINATIONS) {
    String line = myFile.readStringUntil('\n');
    line.trim();
    if (line.length() == 0) continue;
    if (line[0] == '#') continue;               // コメント行（上書きファイルと流儀を揃える）
    if (process_destinationcsv_line(line)) added++;
    else                                        rejected++;
  }
  myFile.close();
  // 捨てた行は必ず残す。黙って無視すると「書いたはずの目的地が出ない」原因に辿り着けない。
  log_sdf("DESTINATIONS: %d added, %d ignored", added, rejected);
}

// SD カードを初期化し、地図・目的地・設定を読み込む。
// trycount: 1回の呼び出しで SDIO を試みる最大回数。失敗時は 100ms 待って再試行する。
// 成功時: FAT タイムスタンプコールバック登録 → ログ記録 → init_mapdata / load_destinations / loadSettings を実行。
// 失敗時: sdInitialized=false のまま処理を戻す（Core1 タスクはエラーをユーザーに報告する）。
// SDIO / SPI フォールバック状態
// setup_sd() 自体が SDIO 失敗を 5 回繰り返した場合に SPI に切り替える（呼び出し回数カウント方式）。
// SDIO が復活した場合は自動的に SDIO に戻る。
static bool sd_use_spi = false;
static int sdio_fail_count = 0;  // setup_sd() が SDIO 失敗した累計呼び出し回数
static int sd_setup_count = 0;   // setup_sd() の累計呼び出し回数
// 目的地・パイロン座標を SD から構築済みか。SD 復旧時の二重追加と
// currentdestination のリセットを防ぐ（init_mapdata() の mapdatainitialized と同じ役割）。
static bool destinations_loaded = false;
// settings.txt を一度でも読める状態で試したか。下の setup_sd() を参照。
// ★ Core1 が立て、Core0（link_setup）が読む。**volatile 必須。**
//   Core0 は startup_demo_tft() で sd_setup_complete を待つので、通常はここが
//   true になってから link_setup() が走る。ただしあの待ちには 5 秒の上限があり、
//   超えると Core0 は先へ進む。そのときだけ「設定が入る前に無線を設定した」状態に
//   なるので、link_setup() がこの値をログに残して後から分かるようにしてある。
volatile bool settings_loaded = false;

bool get_sd_use_spi()    { return sd_use_spi; }
int  get_sd_setup_count(){ return sd_setup_count; }

void setup_sd(int trycount, bool load_settings){
  ASSERT_SD_CORE1("setup_sd");
  sd_setup_count++;
  sdInitialized = false;

  // --- SDIO 試行（SPI モード中はスキップ）---
  if (!sd_use_spi) {
    for (int i = 0; i < trycount; i++) {  // trycount 回だけ試行
      sdInitialized = SD.begin(SdioConfig(RP_CLK_GPIO, RP_CMD_GPIO, RP_DAT0_GPIO));
      if (sdInitialized) break;
      delay(100);
    }
  }

  if (sdInitialized) {
    sdio_fail_count = 0;  // SDIO 成功 → カウンターリセット
    sd_use_spi = false;
  } else {
    sdio_fail_count++;    // SDIO 失敗 → 呼び出し回数をカウント
    DEBUG_PLN(20260309, "SDIO failed.");

    // --- setup_sd が 5 回連続 SDIO 失敗したら SPI にフォールバック ---
    if (sdio_fail_count >= 5) {
      DEBUG_PLN(20260309, "5 SDIO failures. Trying SPI fallback...");
      SPI.setRX(RP_DAT0_GPIO);   // GPIO4 = DAT0 → MISO
      SPI.setTX(RP_CMD_GPIO);    // GPIO3 = CMD  → MOSI
      SPI.setSCK(RP_CLK_GPIO);   // GPIO2 = CLK  → SCK
      SPI.begin();
      sdInitialized = SD.begin(SdSpiConfig(SD_CS_SPI_PIN, DEDICATED_SPI, SD_SCK_MHZ(16)));
      if (sdInitialized) {
        sd_use_spi = true;
        sdio_fail_count = 0;  // SPI 成功 → カウンターリセット
        DEBUG_PLN(20260309, "SD SPI fallback OK.");
      }
    }
  }

  if (!sdInitialized) {
    DEBUG_PLN(20260208, "SD init failed.");
    sd_setup_complete = true;  // 失敗でも完了を通知（Core0 が無限待機しないように）
    return;
  }

  sdError = false;
  SdFile::dateTimeCallback(dateTime);
  log_sd(sd_use_spi ? "SD INIT SPI" : "SD INIT");
  init_mapdata();

  // ★ 目的地とパイロン座標の構築は「最初に SD を掴めた 1 回だけ」。
  //   setup_sd() は try_sd_recovery() から**飛行中にも**呼ばれる。init_mapdata() には
  //   二重ロード防止があるのに、こちらに無かったため次の 3 つが起きていた。
  //     1. 上書きファイルが無い場合 … load_destinations() が SD の目的地を末尾へ
  //        **もう一度追加**する。復旧のたびに増え続け、最後は MAX_DESTINATIONS で溢れる。
  //     2. 上書きファイルがある場合 … init_destinations() が currentdestination を 0 に
  //        戻す。復旧時は load_settings=false なので setDestination() で復元されず、
  //        **パイロットが選んだ目的地が黙って PLATHOME に変わる**。
  //     3. init_destinations() を飛行中に走らせると、Core0 が描画ループから読んでいる
  //        extradestinations[] を Core1 が作り直すことになる。
  //        （この 3 番目は navdata.cpp 側でも対策済み。解放をやめて差し替えだけにしたので、
  //          最悪でも 1 フレーム古い座標を読むだけで、解放済み領域は踏まない。）
  //   起動時に SD を掴めなかった場合は destinations_loaded が false のままなので、
  //   後から復旧したときに 1 回だけ正しく読み込まれる。
  if (!destinations_loaded) {
    // パイロン座標の上書きを先に適用してから目的地を作り直す。
    // init_destinations() は setup1() で既定値のまま一度呼ばれているので、
    // 上書きがあったときだけ新しい座標で登録し直す（内部で前回分を解放する）。
    load_pilon_override();
    if (pilon_override_loaded) init_destinations();
    load_destinations();
    destinations_loaded = true;
  }
  // ★ **まだ一度も読めていないなら、load_settings=false でも必ず読む。**
  //   setup_sd() は起動時（load_settings=true）と try_sd_recovery()（false）から呼ばれる。
  //   false にしてあるのは「ユーザーが操作中の設定値を復旧で上書きしない」ためだが、
  //   その理屈が成り立つのは **すでに読み終わっている場合だけ**。
  //   起動時に SD を 1 回で掴めなかった（SDIO のリトライは 1 回）ときは、以前は
  //   ここを素通りしていたので **settings.txt が一度も読まれないまま飛んでいた**。
  //   volume / destination / navigation_mode に加えて link_mode と link_group まで
  //   既定値（OFF / 0）に戻るため、機体が送信しないまま離陸することになる
  //   （起動音声が鳴らない＝無線 OFF なので気づけはするが、気づけるだけ）。
  //
  //   ファイルが無い場合も「読める状態で試した」ので完了扱いにする。既定値で正しく、
  //   復旧のたびに開き直す意味が無いため。
  if (load_settings || !settings_loaded) {
    const bool ok = loadSettings();
    if (!ok) {
      DEBUGW_PLN(20250508, "Error loading settings.");
    }
    settings_loaded = true;
    // ★ 読み込めた値を log.txt に残す。
    //   settings.txt は機体ごとに違う唯一の設定で、無線の 3 台一致
    //   （link / ch / sf / grp）はここが正しくないと成立しない。
    //   「設定したつもりで入っていなかった」を後から突き止められるようにする。
    //   読めなかったときは既定値で走っているので、その旨も一緒に残す。
    log_sdf("SETTINGS LOADED%s link=%u ch=%u sf=%u grp=%u",
            ok ? "" : " (FAILED, defaults)",
            link_mode_setting, link_radio_ch, link_radio_profile, link_group);
    // 対気速度モデルの実効値。風の推定はこの 4 つで決まり、機体ごとに違う。
    // 「SD に書いたつもりで効いていなかった」を後から突き止められるようにする。
    log_sdf("AIRSPEED MODEL v0=%.2f k=%.2f range %.2f..%.2f",
            attitude_get_airspeed_v0(),  attitude_get_airspeed_k(),
            attitude_get_airspeed_min(), attitude_get_airspeed_max());
  }
  sd_setup_complete = true;  // 全 SD 初期化処理完了を Core0 に通知
}

// ============================================================
// リプレイ再生（PONS の飛行 CSV を直接再生する）
//
// 旧実装は Python で NMEA に変換した replay.csv 専用だったが、v6 では
// SD に保存されている飛行 CSV（YYYY-MM-DD_HHMM.csv, 2Hz）をそのまま再生する。
// CSV のヘッダを「列名」で解釈するため、v5（6列）～v6（10列）まで無加工で扱える。
//
// 役割分担:
//   Core1 (このファイル) … ファイルを開きっぱなしにして行を読み、パースしてリングに積むだけ
//   Core0 (gnss.cpp)      … リングから「再生時刻に達した行」を取り出して stored_* に反映する
// 単一 producer / 単一 consumer のリングなので mutex は不要。
// （スロットへ書き込んでから head を進める順序を必ず守ること）
// ============================================================

// ===== リプレイ再生用変数 =====
volatile ReplayRow replay_rows[REPLAY_BUF_SIZE];  // 先読みした CSV 行のリングバッファ
volatile uint8_t replay_head = 0;                 // Core1 が書き込む位置
volatile uint8_t replay_tail = 0;                 // Core0 が読み出す位置
volatile bool replay_eof = false;                 // ファイル末尾に到達した
// ★ 選ばれたファイルが**そもそも再生できない**（開けない・ヘッダが無い）。
//   これを持たないと、Core0 が「末尾に達した」と同じ扱いでループ再生しようとして
//   init を延々と繰り返す。地図は固まったまま SD を叩き続ける。
//   Core1 が立て、Core0 が見てリプレイを解除する（set_replaymode は Core0 の処理を伴う）。
volatile uint8_t replay_file_bad = REPLAY_BAD_NONE;
// 再生時計のリセット通知。init_replay()（Core1）が加算し、Core0 が値の変化を見て
// 自分の持つ仮想時刻を 0 に戻す。32bit の単純な増加なので排他は不要。
volatile uint32_t replay_init_seq = 0;
char replay_filename[REPLAY_FILENAME_LEN] = "";   // 再生対象ファイル（"" = 未選択）
static bool replay_flight_only = true;            // PLAY FLIGHT ONLY（静止区間をスキップ）。既定 YES
static int  replay_speed = 1;                     // 再生速度の倍率（1 / 2 / REPLAY_SPEED_FAST）

// 飛行 CSV のファイルハンドル。SD.open()/close() を毎回呼ぶのではなく静的 FsFile を
// 使い回すことで open/close 時の SDIO ハングリスクを最小化する（実処理は saveCSV()）。
// init_replay() からも flush するため、ここで定義している。
static FsFile csvFileStatic;  // セッション中開きっぱなし。SDエラー時のみ close。

static FsFile replayFileStatic;      // セッション中は開きっぱなし（SDIOハングリスク低減のため）
static int8_t replay_col[REPLAY_COL_COUNT];  // 列名 → CSV上の列インデックス（-1 = その列は無い）
static uint32_t replay_csv_t0_ms = 0;        // CSV 先頭データ行の時刻（0時からのms）
static uint32_t replay_prev_ms = 0;          // 直前行の時刻（日跨ぎ検出用）
static uint32_t replay_day_offset_ms = 0;    // 日跨ぎ補正の累積 [ms]
static bool replay_t0_valid = false;         // 先頭行の時刻を確定済みか

// --- PLAY FLIGHT ONLY 用のタイムライン圧縮 ---
// 静止行を捨てるだけでは、残った行が元の時刻を保持しているため再生が静止区間で
// 待ち続けてしまう。スキップした区間の長さを累積し、以降の行の再生時刻から
// 差し引くことで、静止区間を詰めて再生する。
static uint32_t replay_skipped_ms = 0;         // スキップした区間の累計 [ms]
static uint32_t replay_leadin_until_abs = 0;   // この絶対時刻までは静止していても再生する（助走区間）

// 助走区間の開始位置を探すためのリングバッファ（静止行のファイル位置と時刻）
static uint32_t replay_leadin_pos[REPLAY_LEADIN_SLOTS];
static uint32_t replay_leadin_abs[REPLAY_LEADIN_SLOTS];

// CSV ヘッダで探す列名。並びは ReplayCol の enum と一致させること。
// ★ 姿勢・風の列名は **imu_replaydata/ と received/ の両方**で使う。
//   片方だけ変えると、受信ログをリプレイしたときに姿勢だけ読めなくなる。
//   文字列の実体をここに 1 つだけ置き、下の 2 つの表から参照する。
#define CN_TIME     "time"
#define CN_ROLL     "roll"
#define CN_PITCH    "pitch"
#define CN_YAW      "yaw"
#define CN_PAVG     "pitch_avg"
#define CN_RTRIM    "roll_trim"
#define CN_YAWACC   "yaw_acc95"
#define CN_WSPD     "wind_mps"
#define CN_WDIR     "wind_dir"

static const char* const replay_col_names[REPLAY_COL_COUNT] = {
  "latitude", "longitude", "gs", "truetrack", "gnss_altitude",
  "kf_altitude", "kf_vspeed", "pressure", "date", CN_TIME,
  "numsat", "voltage",
  // 受信ログ received/ にだけある列。飛行 CSV には無いので -1 のままになる。
  CN_ROLL, CN_PITCH, CN_YAW,
  CN_PAVG, CN_RTRIM, CN_YAWACC, CN_WSPD, CN_WDIR
};

// 旧バージョンの CSV 用の別名。同じ並びで、無い列は nullptr。
// v0.923 以前は GNSS 高度の列名が "Altitude" だったため、それも受け付ける。
static const char* const replay_col_alias[REPLAY_COL_COUNT] = {
  nullptr, nullptr, nullptr, nullptr, "altitude",
  nullptr, nullptr, nullptr, nullptr, nullptr,
  nullptr, nullptr,
  nullptr, nullptr, nullptr, nullptr, nullptr, nullptr, nullptr, nullptr
};

// ===== 再生元フォルダ =====
// false = SD ルートの飛行 CSV（自機のログ）
// true  = received/ の受信ログ（無線で受け取った機体のログ）
// ★ 一覧には常にどちらか一方だけを出す。混ぜないので、ページ計算もファイル
//   インデックスも「1 フォルダぶん」のままでよい（既存の計算に手を入れない）。
static bool replay_from_received = false;

void toggle_replay_from_received(){ replay_from_received = !replay_from_received; }
const char* replay_source_dir()   { return replay_from_received ? REPLAY_RECEIVED_DIR : REPLAY_FLIGHT_DIR; }
const char* replay_source_prefix(){ return replay_from_received ? REPLAY_RECEIVED_DIR "/" : REPLAY_FLIGHT_DIR "/"; }

// 再生中ファイルのフォルダを除いた部分。設定画面の "REPLAY: xxx >" 用。
const char* replay_filename_base() {
  const char* slash = strrchr(replay_filename, '/');
  return slash ? slash + 1 : replay_filename;
}

// 一覧の name（ファイル名のみ）が、いま再生中のファイルか。
// ★ **フルパスで比べること。** ルートと received/ には同じ日時のファイルが
//   同じ名前で並ぶ（どちらも YYYY-MM-DD_HHMM.csv）ので、ファイル名だけで
//   比べると別フォルダの同名ファイルを「再生中」と誤って緑にしてしまう。
bool replay_filename_is(const char* name) {
  char path[REPLAY_FILENAME_LEN];
  snprintf(path, sizeof(path), "%s%s", replay_source_prefix(), name);
  return strcmp(replay_filename, path) == 0;
}

// 大文字小文字を無視した文字列比較（strcasecmp 相当）。前後の空白も無視する。
static bool replay_name_match(const char* token, const char* name) {
  while (*token == ' ' || *token == '\t') token++;
  while (*token && *name) {
    char a = *token, b = *name;
    if (a >= 'A' && a <= 'Z') a += 32;
    if (b >= 'A' && b <= 'Z') b += 32;
    if (a != b) return false;
    token++; name++;
  }
  // token 側の末尾に空白・CR・LF が残っていても一致とみなす
  // （ヘッダ行の最終列は fgets が付けた改行を含むため、これを無視しないと
  //   "time" が最終列にある CSV で列を見つけられなくなる）
  while (*token == ' ' || *token == '\t' || *token == '\r' || *token == '\n') token++;
  return (*token == '\0' && *name == '\0');
}

// CSV 1行から n 番目（0始まり）のフィールドを取り出して out にコピーする。
// 戻り値: 取り出せたら true。フィールドが存在しない場合は false。
static bool replay_get_field(const char* line, int index, char* out, size_t outsize) {
  if (index < 0) return false;
  int field = 0;
  const char* p = line;
  while (field < index) {
    p = strchr(p, ',');
    if (p == nullptr) return false;
    p++;
    field++;
  }
  const char* end = strchr(p, ',');
  size_t len = (end == nullptr) ? strlen(p) : (size_t)(end - p);
  if (len >= outsize) len = outsize - 1;
  memcpy(out, p, len);
  out[len] = '\0';
  // 末尾の CR / 空白を除去
  while (len > 0 && (out[len-1] == '\r' || out[len-1] == '\n' || out[len-1] == ' ')) {
    out[--len] = '\0';
  }
  return (len > 0);
}

// 指定した列の値を float として取り出す。列が無い / 空なら false を返し val は変更しない。
static bool replay_get_float(const char* line, ReplayCol col, float* val) {
  char buf[24];
  if (!replay_get_field(line, replay_col[col], buf, sizeof(buf))) return false;
  *val = atof(buf);
  return true;
}

// "HH:MM:SS" または "HH:MM:SS.cc" を 0時からのミリ秒に変換する。
// 戻り値: 変換できたら true。cs には centisecond（0-99）を返す。
static bool replay_parse_time(const char* s, uint32_t* ms, int* h, int* m, int* sec, int* cs) {
  int hh = 0, mm = 0, ss = 0, cc = 0;
  int n = sscanf(s, "%d:%d:%d.%d", &hh, &mm, &ss, &cc);
  if (n < 3) return false;                   // v5 は ".cc" が無いので n==3 で正常
  if (n < 4) cc = 0;
  if (hh < 0 || hh > 23 || mm < 0 || mm > 59 || ss < 0 || ss > 60) return false;
  *ms  = ((uint32_t)hh * 3600UL + (uint32_t)mm * 60UL + (uint32_t)ss) * 1000UL + (uint32_t)cc * 10UL;
  *h = hh; *m = mm; *sec = ss; *cs = cc;
  return true;
}

// "YYYY-MM-DD" を分解する。
static bool replay_parse_date(const char* s, int* y, int* mo, int* d) {
  return (sscanf(s, "%d-%d-%d", y, mo, d) == 3);
}

// リングバッファの空きスロット数を返す（Core1 側から使用）。
static uint8_t replay_free_slots() {
  uint8_t used = (uint8_t)((replay_head - replay_tail) & (REPLAY_BUF_SIZE - 1));
  return (REPLAY_BUF_SIZE - 1) - used;  // 1 スロットは満杯/空の区別用に常に空けておく
}

// Core0 から呼ぶ: 未消費の行があるか。
bool replay_available() {
  return replay_head != replay_tail;
}

// Core0 から呼ぶ: 次に再生すべき行の再生時刻 [ms]。行が無い場合の戻り値は不定。
uint32_t replay_peek_t_ms() {
  return replay_rows[replay_tail].t_ms;
}

// Core0 から呼ぶ: 先頭の行を取り出す。取り出せたら true。
bool replay_pop(ReplayRow* out) {
  if (replay_head == replay_tail) return false;
  // volatile 配列からのコピー（構造体代入は volatile 不可なのでメンバ単位でコピーする）
  volatile ReplayRow* src = &replay_rows[replay_tail];
  out->lat = src->lat;               out->lon = src->lon;
  out->gs = src->gs;                 out->ttrack = src->ttrack;
  out->gnss_altitude = src->gnss_altitude;     out->kf_altitude = src->kf_altitude;
  out->kf_vspeed = src->kf_vspeed;   out->pressure = src->pressure;
  out->voltage = src->voltage;       out->numsat = src->numsat;
  out->have = src->have;             out->t_ms = src->t_ms;
  out->year = src->year;             out->month = src->month;   out->day = src->day;
  out->hour = src->hour;             out->minute = src->minute; out->second = src->second;
  out->centisecond = src->centisecond;
  // 姿勢ログ由来の値。ここに書き忘れると have だけ立って値がスタックのゴミになる
  // （2026 大会リプレイでロールが +168 になった不具合の原因）。
  // ReplayRow にメンバを足したら必ずこの関数にも足すこと。
  out->roll = src->roll;             out->pitch = src->pitch;
  out->yaw = src->yaw;               out->pitch_avg = src->pitch_avg;
  out->roll_trim = src->roll_trim;   out->yaw_acc95 = src->yaw_acc95;
  out->wind_mps = src->wind_mps;     out->wind_dir = src->wind_dir;
  replay_tail = (replay_tail + 1) & (REPLAY_BUF_SIZE - 1);
  return true;
}

// Core0 から呼ぶ: バッファに空きがあるか（補充依頼を出すかの判断用）。
bool replay_buffer_has_space() {
  uint8_t used = (uint8_t)((replay_head - replay_tail) & (REPLAY_BUF_SIZE - 1));
  return used < (REPLAY_BUF_SIZE - 1);
}

// 選択中のファイル名を返す（設定画面のラベル表示用）。
const char* get_replay_filename() {
  return replay_filename;
}

// 再生対象ファイルを設定する。実際の読み込み開始は init_replay() で行う。
void set_replay_filename(const char* name) {
  strlcpy(replay_filename, name, sizeof(replay_filename));
}

// PLAY FLIGHT ONLY（静止区間をスキップして再生するか）の取得／設定。
bool get_replay_flight_only() { return replay_flight_only; }
void set_replay_flight_only(bool on) { replay_flight_only = on; }

// 再生速度の倍率。x1 → x2 → x(REPLAY_SPEED_FAST) の順に切り替える。
int  get_replay_speed() { return replay_speed; }
void cycle_replay_speed() {
  if      (replay_speed == 1) replay_speed = 2;
  else if (replay_speed == 2) replay_speed = REPLAY_SPEED_FAST;
  else                        replay_speed = 1;
}

// CSV のヘッダ行を列名で解釈し、col[] に「その列が何列目か」を入れる（無い列は -1）。
// 列名は大文字小文字を無視して照合し、未知の列や空の列名（2026大会データに存在）は無視する。
// alias は旧バージョンの別名表。不要なら nullptr を渡す。
// ★ 飛行 CSV（replay_col）と姿勢ログ（att_col）で同じ処理なので 1 つにまとめてある。
static void parse_header_cols(const char* header,
                              const char* const* names, const char* const* alias,
                              int8_t* col, int count) {
  for (int i = 0; i < count; i++) col[i] = -1;

  int index = 0;
  const char* p = header;
  while (p != nullptr && *p != '\0') {
    const char* end = strchr(p, ',');
    char token[24];
    size_t len = (end == nullptr) ? strlen(p) : (size_t)(end - p);
    if (len >= sizeof(token)) len = sizeof(token) - 1;
    memcpy(token, p, len);
    token[len] = '\0';

    for (int c = 0; c < count; c++) {
      if (col[c] == -1 &&
          (replay_name_match(token, names[c]) ||
           (alias != nullptr && alias[c] != nullptr && replay_name_match(token, alias[c])))) {
        col[c] = (int8_t)index;
        break;
      }
    }
    index++;
    p = (end == nullptr) ? nullptr : end + 1;
  }
}

static void replay_parse_header(const char* header) {
  parse_header_cols(header, replay_col_names, replay_col_alias,
                    replay_col, REPLAY_COL_COUNT);
}

// リプレイ再生をファイル先頭から開始（またはループ再生のため再開）する。
// ファイルを開き直し、ヘッダから列マップを構築し、リングバッファを空にする。
// ===== リプレイ時の姿勢（imu_replaydata / euler フォルダ）=====
// 飛行 CSV には姿勢が入っていないので、同じ日の姿勢ログから拾って ReplayRow に載せる。
// 探す順番:
//   1. imu_replaydata/YYYYMMDD.txt … ESKF の結果（画面に出ていた値そのもの）
//   2. euler/YYYYMMDD.txt          … 旧形式。BNO085 由来で 4 列しかない
//   3. どちらも無ければ非表示
// 旧形式では 平均・自動トリム・ヨー精度が存在しないので、それらは表示しない
// （当時 ESKF が動いていなかったので、画面にも出ていなかった）。
//
// 列はヘッダ行の列名で解釈する。ヘッダが無い/読めない古いファイルのために、
// 見つからなければ time,roll,pitch,yaw の固定順とみなすフォールバックを持つ。
enum { ATTCOL_TIME = 0, ATTCOL_ROLL, ATTCOL_PITCH, ATTCOL_YAW,
       ATTCOL_AVG, ATTCOL_TRIM, ATTCOL_YAWACC, ATTCOL_WSPD, ATTCOL_WDIR,
       ATTCOL_COUNT };
static const char* const att_col_names[ATTCOL_COUNT] = {
  CN_TIME, CN_ROLL, CN_PITCH, CN_YAW, CN_PAVG, CN_RTRIM, CN_YAWACC,
  CN_WSPD, CN_WDIR
};

static FsFile   replayAttFile;
// ヘッダ未解析のまま replay_att_is_new_format() が真になると、旧形式なのに
// 平均などを表示してしまう。0 初期化ではなく必ず -1 で始める。
static int8_t   att_col[ATTCOL_COUNT] = { -1, -1, -1, -1, -1, -1, -1, -1, -1 };
static bool     replay_att_tried = false;   // 開こうと試みたか（毎行 open を叩かないため）
static bool     replay_att_ok    = false;   // ファイルを開けたか
static bool     replay_att_eof   = false;
static uint32_t replay_att_ms    = 0;       // 保持中サンプルの時刻（0時からの ms）
static float    replay_att_roll  = 0.0f;
static float    replay_att_pitch = 0.0f;
static float    replay_att_yaw   = 0.0f;
static float    replay_att_avg   = 0.0f;
static float    replay_att_trim  = 0.0f;
static float    replay_att_yawacc = 0.0f;
static bool     replay_att_has_avg = false;  // その行に 平均が入っていたか
static float    replay_att_wspd  = 0.0f;
static float    replay_att_wdir  = 0.0f;
static bool     replay_att_has_wind = false; // その行に風の推定値が入っていたか

// ヘッダ行から att_col[] を作る。1 列も一致しなければ旧形式の固定順とみなす。
static void replay_att_parse_header(const char* header) {
  parse_header_cols(header, att_col_names, nullptr, att_col, ATTCOL_COUNT);

  // ヘッダが無いファイル（1 行目からデータ）への保険
  if (att_col[ATTCOL_TIME] < 0 || att_col[ATTCOL_ROLL] < 0 || att_col[ATTCOL_PITCH] < 0) {
    att_col[ATTCOL_TIME]  = 0;
    att_col[ATTCOL_ROLL]  = 1;
    att_col[ATTCOL_PITCH] = 2;
    att_col[ATTCOL_YAW]   = 3;
    att_col[ATTCOL_AVG]   = -1;
    att_col[ATTCOL_TRIM]  = -1;
    att_col[ATTCOL_YAWACC] = -1;
    att_col[ATTCOL_WSPD]   = -1;
    att_col[ATTCOL_WDIR]   = -1;
  }
}

// ESKF の結果を持つ新形式か（ヨーを機首方位として表示してよいか）の判定に使う。
// 旧 euler は BNO085 のヨーで、実測で真方位から -30〜-65 度ずれていたため表示しない。
static bool replay_att_is_new_format() { return att_col[ATTCOL_YAWACC] >= 0; }

// 目的時刻の手前までファイル位置を一気に飛ばす（位置での二分探索）。
// 姿勢ログは 1 日分を追記し続けるので 5Hz なら 1 日 10MB を超える。飛行 CSV が
// 午後から始まる場合、先頭から順に読むと Core1 が数秒ブロックして SD 書き込みと
// WAV 再生を巻き添えにする。行長がほぼ一定なので位置で二分探索して近くまで跳ぶ。
static void replay_att_fastseek(uint32_t tod_ms) {
  uint32_t lo = 0, hi = (uint32_t)replayAttFile.fileSize();
  char line[96];
  char buf[24];
  // 残り 4KB（約80行）まで詰めたら打ち切り、あとは通常の逐次読みに任せる
  for (int it = 0; it < 24 && (hi - lo) > 4096; it++) {
    uint32_t mid = lo + (hi - lo) / 2;
    if (!replayAttFile.seekSet(mid)) break;
    replayAttFile.fgets(line, sizeof(line));            // 行の途中に着地するので 1 行捨てる
    if (replayAttFile.fgets(line, sizeof(line)) <= 0) { hi = mid; continue; }
    if (!replay_get_field(line, att_col[ATTCOL_TIME], buf, sizeof(buf))) { hi = mid; continue; }
    uint32_t ms; int h, m, sec, cs;
    // 時刻が読めない行は前後関係の判断材料にならない。lo を進めると目的時刻を
    // 通り越して行き過ぎるので、必ず狭める側（hi）に倒す。
    if (!replay_parse_time(buf, &ms, &h, &m, &sec, &cs)) { hi = mid; continue; }
    if (ms < tod_ms) lo = mid; else hi = mid;
  }
  replayAttFile.seekSet(lo);
  if (lo > 0) replayAttFile.fgets(line, sizeof(line));  // 行頭とは限らないので 1 行捨てる
}

// その日の姿勢ログを開く。新形式 → 旧形式の順に探し、無ければ静かに諦める。
// tod_ms は再生を始める時刻。ここまで一気に飛ばしてから逐次読みに入る。
static void replay_att_open(int y, int mo, int d, uint32_t tod_ms) {
  if (replay_att_tried) return;
  replay_att_tried = true;
  if (y < 2000 || mo < 1 || mo > 12 || d < 1 || d > 31) return;

  char fname[32];
  const char* dirs[2] = { IMU_REPLAYDATA_DIR, IMU_REPLAYDATA_LEGACY_DIR };
  for (int k = 0; k < 2; k++) {
    snprintf(fname, sizeof(fname), "%s/%04d%02d%02d.txt", dirs[k], y, mo, d);
    if (!SD.exists(fname)) continue;
    replayAttFile = SD.open(fname, FILE_READ);
    if (!replayAttFile) continue;

    // 1 行目 = ヘッダ。列名から列マップを作る（無ければ固定順にフォールバック）。
    // 現状 67 文字だが、切り詰めると列が静かに欠ける（上の init_replay() 参照）ので余裕を取る。
    char header[128];
    if (replayAttFile.fgets(header, sizeof(header)) <= 0) {
      replayAttFile.close();
      continue;
    }
    replay_att_parse_header(header);
    replay_att_ok = true;
    replay_att_fastseek(tod_ms);
    log_sdf("REPLAY att: %s%s", fname, replay_att_is_new_format() ? " (ESKF)" : " (legacy)");
    return;
  }
}

// CSV 行の時刻 tod_ms に追いつくまで姿勢ログを読み進める。
// 姿勢ログは 5Hz・CSV は 2Hz なので通常は 2〜3 行進めるだけ。
// PLAY FLIGHT ONLY の助走 seek で CSV 側が数秒巻き戻ることがあるが、
// 1 日分を読み直すのは重すぎるので、その場合は最後のサンプルを保持し続ける
// （CSV の時刻が追いつけば自動的に整合が戻る）。
static bool replay_att_seek(uint32_t tod_ms) {
  if (!replay_att_ok) return false;
  char line[96];
  char buf[24];
  while (!replay_att_eof && replay_att_ms < tod_ms) {
    if (replayAttFile.fgets(line, sizeof(line)) <= 0) { replay_att_eof = true; break; }
    if (!replay_get_field(line, att_col[ATTCOL_TIME], buf, sizeof(buf))) continue;
    uint32_t ms; int h, m, s2, cs;
    if (!replay_parse_time(buf, &ms, &h, &m, &s2, &cs)) continue;   // ヘッダ行はここで弾かれる
    replay_att_ms = ms;
    if (replay_get_field(line, att_col[ATTCOL_ROLL],  buf, sizeof(buf))) replay_att_roll  = atof(buf);
    if (replay_get_field(line, att_col[ATTCOL_PITCH], buf, sizeof(buf))) replay_att_pitch = atof(buf);
    if (replay_get_field(line, att_col[ATTCOL_YAW],   buf, sizeof(buf))) replay_att_yaw   = atof(buf);
    if (replay_get_field(line, att_col[ATTCOL_TRIM],  buf, sizeof(buf))) replay_att_trim  = atof(buf);
    if (replay_get_field(line, att_col[ATTCOL_YAWACC],buf, sizeof(buf))) replay_att_yawacc = atof(buf);
    // 平均は未収束の間は空欄で書かれている（replay_get_field は空欄で false）
    replay_att_has_avg = replay_get_field(line, att_col[ATTCOL_AVG], buf, sizeof(buf));
    if (replay_att_has_avg) replay_att_avg = atof(buf);
    // 風も推定できていない区間は空欄なので、両方読めたときだけ有効
    replay_att_has_wind = replay_get_field(line, att_col[ATTCOL_WSPD], buf, sizeof(buf));
    if (replay_att_has_wind) {
      replay_att_wspd = atof(buf);
      replay_att_has_wind = replay_get_field(line, att_col[ATTCOL_WDIR], buf, sizeof(buf));
      if (replay_att_has_wind) replay_att_wdir = atof(buf);
    }
  }
  // 保持しているサンプルが再生時刻から離れすぎていたら「無い」と答える。
  // これが無いと、姿勢ログが飛行 CSV より先に終わっている場合に最後のサンプルを
  // 貼り付けたまま固まって見える（地図だけ動いて姿勢だけ止まる）。
  // 飛行 CSV より後から始まっている場合も同様。
  if (replay_att_ms == 0) return false;
  const uint32_t age = (tod_ms > replay_att_ms) ? (tod_ms - replay_att_ms)
                                                : (replay_att_ms - tod_ms);
  return age <= REPLAY_ATT_MAX_AGE_MS;
}

void init_replay(){
  ASSERT_SD_CORE1("init_replay");
  if (replayFileStatic.isOpen()) replayFileStatic.close();

  // 姿勢ログも先頭から読み直す（ループ再生・別ファイル選択の両方に対応）
  if (replayAttFile.isOpen()) replayAttFile.close();
  replay_att_tried = false;
  replay_att_ok    = false;
  replay_att_eof   = false;
  replay_att_ms    = 0;
  replay_att_has_avg = false;
  replay_att_has_wind = false;
  // 前のファイルの列マップを残さない（旧形式を新形式と誤判定するのを防ぐ）
  for (int i = 0; i < ATTCOL_COUNT; i++) att_col[i] = -1;

  replay_head = 0;
  replay_tail = 0;
  replay_eof = false;
  replay_file_bad = REPLAY_BAD_NONE;
  replay_t0_valid = false;
  replay_csv_t0_ms = 0;
  replay_prev_ms = 0;
  replay_day_offset_ms = 0;
  replay_skipped_ms = 0;
  replay_leadin_until_abs = 0;
  replay_init_seq++;   // Core0 側の再生時計を 0 に戻させる

  // 飛行 CSV は 2 秒に 1 回しか flush していないため、リプレイに入って saveCSV() が
  // 呼ばれなくなると、直前の実飛行データ最大 2 秒分が SdFat のバッファに残ったままになる。
  // リプレイ中に電源が切られると失われるので、ここで確実に書き出しておく。
  // （ファイルは閉じない。リプレイ終了後は同じファイルに追記を続ける）
  if (csvFileStatic.isOpen()) csvFileStatic.flush();

  if (replay_filename[0] == '\0') {
    DEBUGW_PLN(20260731, "REPLAY: no file selected");
    replay_eof = true; replay_file_bad = REPLAY_BAD_FILE;
    return;
  }
  if (!good_sd()) {
    // ★ ここで必ず「もう続けられない」と伝えること。
    //   以前は replay_eof だけを立てて戻っていた。Core0 は EOF を
    //   「末尾に着いた＝先頭からループ再生する」と解釈して INIT_REPLAY を投げ直すので、
    //   SD が復帰しない限り  init_replay() → !good_sd() → eof → init_replay() …
    //   と回り続け、地図が固まったままタスクキューを埋め続けていた。
    //   （replay_file_bad はまさにこの空回りを止めるために入れたフラグ）
    DEBUGW_PLN(20260731, "REPLAY: SD not available");
    replay_eof = true; replay_file_bad = REPLAY_BAD_NOSD;
    return;
  }

  replayFileStatic = SD.open(replay_filename, FILE_READ);
  if (!replayFileStatic) {
    DEBUGW_P(20260731, "REPLAY: cannot open ");
    DEBUGW_PLN(20260731, replay_filename);
    log_sdf("ERR REPLAY open failed: %s", replay_filename);
    replay_eof = true; replay_file_bad = REPLAY_BAD_FILE;
    return;
  }

  // 1行目 = ヘッダ。列名から列マップを作る。
  // ★ **received/ のヘッダは 180 文字ある。** ここを切り詰めると、切れた列は
  //   「名前が壊れたトークン」または「存在しない列」になり、静かに -1 のまま残る。
  //   実際 160 では末尾が "...,roll_trim,yaw_ac" で切れ、yaw_acc95 / wind_mps /
  //   wind_dir が拾えず、**受信ログを再生してもヨーと風だけ出ない**という
  //   気づきにくい壊れ方をしていた（列名解釈なのでエラーにもならない）。
  //   列を足すときはここも必ず見直すこと。
  //     data/     : 101 文字
  //     received/ : 180 文字（飛行 CSV + rssi,seq,age_ms + 姿勢 6 列 + 風 2 列）
  char header[256];
  int n = replayFileStatic.fgets(header, sizeof(header));
  if (n <= 0) {
    log_sdf("ERR REPLAY empty file: %s", replay_filename);
    replayFileStatic.close();          // 他の失敗経路と揃える（開きっぱなしにしない）
    replay_eof = true; replay_file_bad = REPLAY_BAD_FILE;
    return;
  }
  replay_parse_header(header);

  // 最低限 latitude / longitude / time が無ければ再生できない
  if (replay_col[RCOL_LAT] < 0 || replay_col[RCOL_LON] < 0 || replay_col[RCOL_TIME] < 0) {
    DEBUGW_PLN(20260731, "REPLAY: header missing lat/lon/time");
    log_sdf("ERR REPLAY bad header: %s", replay_filename);
    replayFileStatic.close();
    replay_eof = true; replay_file_bad = REPLAY_BAD_FILE;
    return;
  }
  log_sdf("REPLAY start: %s", replay_filename);
}


// 静止区間の先頭行に来たときに呼ぶ（PLAY FLIGHT ONLY 有効時のみ）。
// 区間がどこで終わる（＝機体が動き出す）かを先読みし、
//   ・静止が REPLAY_LEADIN_MS 未満  → 一切スキップせずそのまま再生する
//   ・静止が REPLAY_LEADIN_MS 以上  → 動き出しの REPLAY_LEADIN_MS 手前まで飛ばす
// いずれの場合もファイル位置を再生を再開すべき行まで seek で巻き戻して戻る。
// 動き出しの手前を「助走」として残すのは、いきなり動き出すと表示や警告音が
// 実際の飛行開始と食い違って見えるため。
//
// run_start_pos / run_start_abs: 静止区間の先頭行のファイル位置と絶対時刻
// 戻り値: false なら静止のままファイル末尾に到達した
static bool replay_handle_stationary_run(uint32_t run_start_pos, uint32_t run_start_abs) {
  // 走査中に進んでしまう日跨ぎ判定用の状態を保存しておき、seek で戻すときに復元する
  uint32_t saved_prev_ms   = replay_prev_ms;
  uint32_t saved_day_offset = replay_day_offset_ms;

  // 区間の先頭を最初の候補として登録する
  replay_leadin_pos[0] = run_start_pos;
  replay_leadin_abs[0] = run_start_abs;
  uint8_t head = 1, count = 1;

  char line[200], buf[24];
  uint32_t move_abs = 0;
  uint32_t last_abs = run_start_abs;
  bool found_move = false;
  int scanned = 0;

  while (scanned < REPLAY_SCAN_MAX) {
    uint32_t pos = (uint32_t)replayFileStatic.position();
    int n = replayFileStatic.fgets(line, sizeof(line));
    if (n <= 0) {
      // 静止したままファイル末尾。残りは再生する意味がないので終了扱いにする。
      return false;
    }
    scanned++;

    uint32_t tod; int hh, mm, ss, cc;
    if (!replay_get_field(line, replay_col[RCOL_TIME], buf, sizeof(buf))) continue;
    if (!replay_parse_time(buf, &tod, &hh, &mm, &ss, &cc)) continue;
    // 日跨ぎ補正（本体のループと同じ処理）
    if (tod + 60000UL < replay_prev_ms) replay_day_offset_ms += 86400000UL;
    replay_prev_ms = tod;
    uint32_t abs_ms = tod + replay_day_offset_ms;
    last_abs = abs_ms;

    float gs_val;
    if (replay_get_float(line, RCOL_GS, &gs_val) && gs_val > REPLAY_MIN_GS) {
      move_abs = abs_ms;      // ここで動き出した
      found_move = true;
      break;
    }

    // まだ静止 → 直近 REPLAY_LEADIN_SLOTS 行のファイル位置を保持する
    replay_leadin_pos[head] = pos;
    replay_leadin_abs[head] = abs_ms;
    head = (head + 1) % REPLAY_LEADIN_SLOTS;
    if (count < REPLAY_LEADIN_SLOTS) count++;
  }

  if (!found_move) {
    // 走査上限に達した（非常に長い静止区間）。ここまでを飛ばしたことにして
    // 現在位置からそのまま続行する（seek で戻さないので日跨ぎ判定の状態も進めたままにする）。
    // 次の行もまた静止なら改めて先読みが走るので、Core1 を長時間占有せずに少しずつ処理が進む。
    replay_skipped_ms += last_abs - run_start_abs;
    return true;
  }

  // ここから先は seek でファイル位置を巻き戻すので、走査中に進めた
  // 日跨ぎ判定用の状態も区間先頭の時点まで戻す（戻した行を読み直すため）
  replay_prev_ms       = saved_prev_ms;
  replay_day_offset_ms = saved_day_offset;

  // 再生を再開する位置を決める
  uint32_t resume_pos, resume_abs;
  if (move_abs - run_start_abs < REPLAY_LEADIN_MS) {
    // 短い静止 → スキップしない（区間の先頭から再生する）
    resume_pos = run_start_pos;
    resume_abs = run_start_abs;
  } else {
    // 動き出しの REPLAY_LEADIN_MS 手前以降で、最も古い行を探す
    uint32_t target = move_abs - REPLAY_LEADIN_MS;
    uint8_t oldest = (uint8_t)((head + REPLAY_LEADIN_SLOTS - count) % REPLAY_LEADIN_SLOTS);
    resume_pos = replay_leadin_pos[oldest];   // 保持している中で最も古い行（既定値）
    resume_abs = replay_leadin_abs[oldest];
    for (uint8_t i = 0; i < count; i++) {
      uint8_t k = (uint8_t)((oldest + i) % REPLAY_LEADIN_SLOTS);
      if (replay_leadin_abs[k] >= target) {
        resume_pos = replay_leadin_pos[k];
        resume_abs = replay_leadin_abs[k];
        break;
      }
    }
  }

  // 飛ばした分だけ再生タイムラインを詰める
  replay_skipped_ms += resume_abs - run_start_abs;
  // 動き出しまでは静止していても再生する（助走区間）
  replay_leadin_until_abs = move_abs;
  replayFileStatic.seek(resume_pos);
  return true;
}


// リングバッファの空きスロットを埋められるだけ埋める（Core1 で実行）。
// パースに失敗した行は読み飛ばして次へ進む（旧実装のような無限ループにはならない）。
void load_replay() {
  ASSERT_SD_CORE1("load_replay");
  if (replay_eof) return;
  if (!replayFileStatic.isOpen()) return;

  char line[200];

  while (replay_free_slots() > 0) {
    uint32_t line_pos = (uint32_t)replayFileStatic.position();  // 静止区間の巻き戻しに使う
    int n = replayFileStatic.fgets(line, sizeof(line));
    if (n <= 0) {
      // ファイル末尾。Core0 側が残りを再生し終えたら init_replay() でループ再生する。
      replay_eof = true;
      return;
    }

    // --- 時刻（必須） ---
    char buf[24];
    if (!replay_get_field(line, replay_col[RCOL_TIME], buf, sizeof(buf))) continue;
    uint32_t tod_ms;
    int hh, mm, ss, cc;
    if (!replay_parse_time(buf, &tod_ms, &hh, &mm, &ss, &cc)) continue;

    // 日跨ぎ補正: 時刻が前の行より大きく戻ったら 1 日進んだとみなす
    if (replay_t0_valid && tod_ms + 60000UL < replay_prev_ms) {
      replay_day_offset_ms += 86400000UL;
    }
    replay_prev_ms = tod_ms;
    if (!replay_t0_valid) {
      replay_csv_t0_ms = tod_ms;
      replay_t0_valid = true;
    }
    uint32_t abs_ms = tod_ms + replay_day_offset_ms;
    if (abs_ms < replay_csv_t0_ms) continue;  // 念のための保険

    // --- 対地速度（PLAY FLIGHT ONLY の判定に使う） ---
    float gs_val;
    bool has_gs = replay_get_float(line, RCOL_GS, &gs_val);

    // PLAY FLIGHT ONLY: 静止（GS が閾値以下）の区間の先頭に来たら、
    // 区間の長さを先読みして「飛ばすか / そのまま再生するか」を決める。
    // 助走区間（動き出し直前の REPLAY_LEADIN_MS）の中にいる間は判定しない。
    // gs 列を持たない CSV は判定できないので全行再生する。
    if (replay_flight_only && has_gs && gs_val <= REPLAY_MIN_GS &&
        abs_ms >= replay_leadin_until_abs) {
      if (!replay_handle_stationary_run(line_pos, abs_ms)) {
        replay_eof = true;   // 静止のままファイル末尾に到達
        return;
      }
      continue;  // ファイル位置は seek で調整済み。次の行から読み直す。
    }

    // --- 緯度経度（必須） ---
    // 緯度経度は float では精度が足りないので atof() の double をそのまま使う
    double dlat, dlon;
    if (!replay_get_field(line, replay_col[RCOL_LAT], buf, sizeof(buf))) continue;
    dlat = atof(buf);
    if (!replay_get_field(line, replay_col[RCOL_LON], buf, sizeof(buf))) continue;
    dlon = atof(buf);
    if (dlat < -90.0 || dlat > 90.0 || dlon < -180.0 || dlon > 180.0) continue;

    // --- スロットに書き込む ---
    volatile ReplayRow* row = &replay_rows[replay_head];
    row->have = 0;
    row->lat = dlat;
    row->lon = dlon;
    // スキップした静止区間の長さを差し引いた再生時刻
    row->t_ms = (abs_ms - replay_csv_t0_ms) - replay_skipped_ms;
    row->hour = hh; row->minute = mm; row->second = ss; row->centisecond = cc;

    float v;
    if (has_gs)                                   { row->gs = gs_val; row->have |= RHAVE_GS; }
    else                                          { row->gs = 0; }
    if (replay_get_float(line, RCOL_TTRACK, &v)) { row->ttrack = v; row->have |= RHAVE_TTRACK; }
    else                                          { row->ttrack = 0; }
    if (replay_get_float(line, RCOL_GNSSALT, &v))    { row->gnss_altitude = v;    row->have |= RHAVE_GNSSALT; }
    else                                          { row->gnss_altitude = 0; }
    if (replay_get_float(line, RCOL_KFALT, &v))  { row->kf_altitude = v; row->have |= RHAVE_KFALT; }
    else                                          { row->kf_altitude = 0; }
    if (replay_get_float(line, RCOL_KFVS, &v))   { row->kf_vspeed = v;   row->have |= RHAVE_KFVS; }
    else                                          { row->kf_vspeed = 0; }
    if (replay_get_float(line, RCOL_PRESS, &v))  { row->pressure = v;    row->have |= RHAVE_PRESS; }
    else                                          { row->pressure = 0; }
    if (replay_get_float(line, RCOL_VOLT, &v))   { row->voltage = v;     row->have |= RHAVE_VOLT; }
    else                                          { row->voltage = 0; }
    if (replay_get_float(line, RCOL_NUMSAT, &v)) { row->numsat = (int)v; row->have |= RHAVE_NUMSAT; }
    else                                          { row->numsat = 0; }

    // --- 日付（あれば） ---
    int yy = 0, mo = 0, dd = 0;
    if (replay_get_field(line, replay_col[RCOL_DATE], buf, sizeof(buf)) &&
        replay_parse_date(buf, &yy, &mo, &dd)) {
      row->year = yy; row->month = mo; row->day = dd;
      row->have |= RHAVE_DATE;
    } else {
      row->year = 0; row->month = 0; row->day = 0;
    }

    // --- 姿勢 ---
    row->roll = 0.0f; row->pitch = 0.0f; row->yaw = 0.0f;
    row->pitch_avg = 0.0f; row->roll_trim = 0.0f; row->yaw_acc95 = 0.0f;
    row->wind_mps = 0.0f; row->wind_dir = 0.0f;

    // ★ CSV 自身が姿勢を持っているならそれを使い、**外部の姿勢ログは見ない**。
    //   received/ の再生でここを外部参照にすると、日付から引かれるのは
    //   **ボート自身の imu_replaydata/** なので、機体の航跡にボートの
    //   ロール・ピッチが黙って合成される。一番たちの悪い壊れ方になる。
    if (replay_col[RCOL_ROLL] >= 0) {
      float roll_v, pitch_v, yaw_v, acc_v, wspd_v, wdir_v;
      // roll と pitch が両方読めた行だけを「姿勢あり」とする。
      // 送信側の ESKF が未収束だった区間は空欄で入っているので、そこは姿勢なし。
      if (replay_get_float(line, RCOL_ROLL,  &roll_v) &&
          replay_get_float(line, RCOL_PITCH, &pitch_v)) {
        row->roll  = roll_v;
        row->pitch = pitch_v;
        row->have |= RHAVE_ATT;
      }
      if (replay_get_float(line, RCOL_YAW,    &yaw_v) &&
          replay_get_float(line, RCOL_YAWACC, &acc_v)) {
        row->yaw       = yaw_v;
        row->yaw_acc95 = acc_v;
        row->have |= RHAVE_ATT_YAW;
      }
      if (replay_get_float(line, RCOL_PAVG,  &v)) { row->pitch_avg = v; row->have |= RHAVE_ATT_AVG; }
      if (replay_get_float(line, RCOL_RTRIM, &v)) { row->roll_trim = v; row->have |= RHAVE_ATT_TRIM; }
      if (replay_get_float(line, RCOL_WSPD, &wspd_v) &&
          replay_get_float(line, RCOL_WDIR, &wdir_v)) {
        row->wind_mps = wspd_v;
        row->wind_dir = wdir_v;
        row->have |= RHAVE_ATT_WIND;
      }
      // 内容を書き終えてから head を進める（下の外部参照パスと同じ理由）
      replay_head = (replay_head + 1) & (REPLAY_BUF_SIZE - 1);
      continue;
    }

    // --- 姿勢（同じ日の姿勢ログがあれば）---
    if (!replay_att_tried) {
      int fy = yy, fmo = mo, fdd = dd;
      if (!(row->have & RHAVE_DATE)) {
        // 日付列を持たない v5 データ: ファイル名 "YYYY-MM-DD_HHMM.csv" から拾う
        const char* base = strrchr(replay_filename, '/');
        base = (base != nullptr) ? base + 1 : replay_filename;
        if (sscanf(base, "%d-%d-%d", &fy, &fmo, &fdd) != 3) fy = 0;
      }
      replay_att_open(fy, fmo, fdd, tod_ms);
    }
    if (replay_att_seek(tod_ms)) {
      row->roll  = replay_att_roll;
      row->pitch = replay_att_pitch;
      row->have |= RHAVE_ATT;
      // 以下は新形式（ESKF の結果）にしか無い。旧 euler では表示しない。
      if (replay_att_is_new_format()) {
        row->yaw       = replay_att_yaw;
        row->yaw_acc95 = replay_att_yawacc;
        row->roll_trim = replay_att_trim;
        row->have |= RHAVE_ATT_YAW | RHAVE_ATT_TRIM;
        if (replay_att_has_avg) {
          row->pitch_avg = replay_att_avg;
          row->have |= RHAVE_ATT_AVG;
        }
        if (replay_att_has_wind) {
          row->wind_mps = replay_att_wspd;
          row->wind_dir = replay_att_wdir;
          row->have |= RHAVE_ATT_WIND;
        }
      }
    }

    // 内容を書き終えてから head を進める（Core0 が中途半端な行を読まないようにする）
    replay_head = (replay_head + 1) & (REPLAY_BUF_SIZE - 1);
  }
}

// ===== リプレイ選択画面のファイル一覧 =====
char replayfiles[REPLAY_LIST_ROWS][32];  // 現在表示中のCSVファイル名
int  replayfiles_size[REPLAY_LIST_ROWS]; // 対応するファイルサイズ [byte]
// どちらも Core1 の browse_replay_files() が書き、Core0 がメニュー表示・項目判定で読むため volatile
volatile int  replayfiles_count = 0;     // replayfiles[] に入っている件数
volatile int  replayfiles_total = 0;     // SD ルート上の対象CSVの総数

extern volatile bool loading_replaylist;

// ファイル名が拡張子 .csv（大小無視）で終わるか。
static bool has_csv_ext(const char* name) {
  size_t len = strlen(name);
  if (len < 5) return false;  // "x.csv" が最短
  const char* ext = name + len - 4;
  return (ext[0] == '.' &&
          (ext[1] == 'c' || ext[1] == 'C') &&
          (ext[2] == 's' || ext[2] == 'S') &&
          (ext[3] == 'v' || ext[3] == 'V'));
}

// リプレイ対象の CSV か判定する。
// ★ 走査するのは data/ と received/ だけで、設定ファイルはルートにしか無い。
//   そのため**除外リストが要らない**（以前はルートを走査していたので、
//   ルートに CSV を足すたびに除外リストへ追記する必要があった）。
static bool is_replay_candidate(const char* name) {
  if (name[0] == '.') return false;                 // macOS の ._ ファイル等
  return has_csv_ext(name);
}

// 再生元フォルダのリプレイ対象CSVを列挙し replayfiles[] に格納する（Core1 で実行）。
// start_index: 対象CSVの通し番号（0始まり）のうち、どこから格納するか。
// 戻り値: 1 件以上格納できたら true。フォルダは対象外。
//
// ★ 並び順は **ディレクトリの登録順**（openNextFile が返す順）で、ファイル名順ではない。
//   FAT はディレクトリエントリを先頭の空きスロットから埋めるので、実質は
//   「SD へ書かれた順（削除跡があればそこを再利用）」になる。
//   大会データを一覧の上に出したいなら、**カードへ最初にコピーする**こと。
//   名前を変えても順番は変わらない。
bool browse_replay_files(int start_index) {
  if (start_index < 0) start_index = 0;

  for (int i = 0; i < REPLAY_LIST_ROWS; i++) {
    replayfiles[i][0] = '\0';
    replayfiles_size[i] = 0;
  }
  replayfiles_count = 0;
  replayfiles_total = 0;

  // 再生元フォルダ。received/ がまだ無い機体（一度も受信していない）は
  // ここで開けないので、素直に「0 件」の空一覧になる。
  FsFile root = SD.open(replay_source_dir());
  if (!root || !root.isDirectory()) {
    DEBUGW_PLN(20260731, "REPLAY: failed to open source dir");
    if (root) root.close();
    loading_replaylist = false;
    return false;
  }

  while (true) {
    FsFile entry = root.openNextFile();
    if (!entry) break;

    char name[32];
    entry.getName(name, sizeof(name));
    bool isdir = entry.isDirectory();
    uint32_t fsize = isdir ? 0 : entry.size();
    entry.close();

    if (isdir || !is_replay_candidate(name)) continue;

    // 該当ページの範囲内なら格納する
    if (replayfiles_total >= start_index && replayfiles_count < REPLAY_LIST_ROWS) {
      strlcpy(replayfiles[replayfiles_count], name, 32);
      replayfiles_size[replayfiles_count] = (int)fsize;
      replayfiles_count++;
    }
    replayfiles_total++;
  }

  root.close();
  DEBUG_P(20260731, "REPLAY files total: ");
  DEBUG_PLN(20260731, replayfiles_total);
  loading_replaylist = false;
  return replayfiles_count > 0;
}


// ===== リプレイ選択画面の項目モデル =====
// 一覧の通し番号（index）は次の並びになっている:
//   0 : Replay OFF
//   1 : PLAY FLIGHT ONLY: YES/NO（トグル）
//   2 : PLAY SPEED: x1/x2/x??（トグル）
//   3 : SOURCE: FLIGHT/RECEIVED（トグル）
//   REPLAY_FIXED_COUNT .. +replayfiles_total-1 : 再生元フォルダ内の CSV
//   REPLAY_FIXED_COUNT + replayfiles_total     : Return
// ★ 固定項目は**常にこの 4 つだけ**。大会データもただの CSV として一覧に並ぶ。
//   描画側もボタン処理側もこのモデルを共有する。

// 一覧の総項目数（固定項目 + ファイル数 + Return）。
int replay_menu_total_items() {
  return REPLAY_FIXED_COUNT + replayfiles_total + 1;
}

// 通し番号が属するページ番号（0始まり）。
int replay_menu_page_of(int index) {
  if (index < 0) return 0;
  return index / REPLAY_LIST_ROWS;
}

// 総ページ数。
int replay_menu_page_count() {
  int total = replay_menu_total_items();
  return (total <= 0) ? 1 : ((total - 1) / REPLAY_LIST_ROWS) + 1;
}

// そのページを描画するために browse_replay_files() に渡すべき「ファイルの開始通し番号」。
// ページ 0 は先頭に固定項目が入る分だけファイルの開始位置が手前にずれる。
int replay_menu_file_start_for_page(int page) {
  int start = page * REPLAY_LIST_ROWS - REPLAY_FIXED_COUNT;
  return (start < 0) ? 0 : start;
}

// 通し番号 index の項目種別を返し、表示用ラベル（ファイルなら実ファイル名）を label に格納する。
// filesize には該当ファイルのサイズ [byte] を返す（ファイル以外は 0）。
// page: 現在 replayfiles[] に読み込まれているページ番号。
ReplayItemType replay_menu_item(int index, int page, char* label, size_t labelsize, int* filesize) {
  if (filesize) *filesize = 0;
  if (label && labelsize > 0) label[0] = '\0';

  if (index < 0 || index >= replay_menu_total_items()) return RITEM_NONE;

  if (index == 0) { strlcpy(label, "Replay OFF (Normal GNSS)", labelsize); return RITEM_OFF; }
  if (index == 1) {
    snprintf(label, labelsize, "PLAY FLIGHT ONLY: %s", replay_flight_only ? "YES" : "NO");
    return RITEM_FLIGHTONLY;
  }
  if (index == 2) {
    snprintf(label, labelsize, "PLAY SPEED: x%d", replay_speed);
    return RITEM_SPEED;
  }
  if (index == 3) {
    snprintf(label, labelsize, "SOURCE: %s",
             replay_from_received ? "RECEIVED (radio)" : "FLIGHT (own)");
    return RITEM_SOURCE;
  }

  const int fixed = REPLAY_FIXED_COUNT;
  if (index == fixed + replayfiles_total) {
    strlcpy(label, "Return", labelsize);
    return RITEM_RETURN;
  }

  // ファイル項目: 現在読み込まれているページ内の何番目かを求める
  int local = (index - fixed) - replay_menu_file_start_for_page(page);
  if (local < 0 || local >= replayfiles_count) return RITEM_NONE;  // 別ページ = 未読み込み
  strlcpy(label, replayfiles[local], labelsize);
  if (filesize) *filesize = replayfiles_size[local];
  return RITEM_FILE;
}


// ===== SD ブラウザ用変数 =====
char sdfiles[20][32];  // 現在のページに表示するファイル/フォルダ名（最大20エントリ）。フォルダは先頭に'/'を付与
int sdfiles_size[20];  // 対応するファイルのサイズ（バイト）。フォルダは 0
volatile int max_page = -1;  // SD ルートの総ファイル数から計算した最大ページ番号（0-based）
                             // Core1 の browse_sd() が書き、Core0 が表示・ページ送りで読むため volatile

extern volatile bool loading_sddetail;  // 実体は display_tft.cpp（volatile）。Core1 が false にして Core0 が読む

// SD カードのルートディレクトリをページ単位で列挙し sdfiles[] に格納する。
// page: 0-based のページ番号。1 ページあたり最大 20 エントリ。
// 戻り値: エントリが 1 件以上あれば true、ゼロまたはエラーなら false。
// - 隠しファイル（'.'または"/."で始まるもの）はスキップする（macOS の ._ ファイル除外）。
// - フォルダは名前の先頭に '/' を付けて区別する。
// - 処理完了後に loading_sddetail=false をセットし、表示側に完了を通知する。
bool browse_sd(int page) {
    // Input validation
    if (page < 0) {
        DEBUGW_PLN(20250508,"Invalid page number");
        return false;
    }

    // Clear the array
    for (int i = 0; i < 20; i++) {
        sdfiles[i][0] = '\0';
        sdfiles_size[i] = 0;
    }


    FsFile root = SD.open("/");
    if (!root || !root.isDirectory()) {
        DEBUGW_PLN(20250508,"Failed to open root directory");

        if (root) root.close();
        return false;
    }

    int count = 0;          // Total files/folders processed
    int matched = 0;        // Entries stored in sdfiles
    int total_valid = 0;    // Total non-hidden files/folders

    // Process all entries
    while (true) {
        FsFile entry = root.openNextFile();
        if (!entry) break;

        // Skip hidden files and macOS-specific files starting with "." or "/."
        char name[32];
        entry.getName(name, 32);
        if (name[0] == '.' || (name[0] == '/' && name[1] == '.')) {
            entry.close();
            continue;
        }

        // Count valid entries for max_page calculation
        total_valid++;

        // Store entries for the requested page
        if (count >= page * 20 && matched < 20) {
            char* target = sdfiles[matched];
            
            if (entry.isDirectory()) {
                target[0] = '/';
                strlcpy(target + 1, name, 31); // Leave space for prefix
            } else {
                strlcpy(target, name, 32);
                sdfiles_size[matched] = entry.size();
            }

            // Ensure truncation at 60 chars (including prefix for folders)
            if (strlen(target) > 30) {
                target[30] = '\0';
            }

            matched++;
        }
        
        count++;
        entry.close();
    }

    root.close();

    // Calculate and store maximum page number (0-based)
    max_page = total_valid > 0 ? (total_valid - 1) / 20 : 0;

    // Print results for debugging
    for (int i = 0; i < matched; i++) {
        DEBUG_PLN(20250508,sdfiles[i]);
    }
    DEBUG_P(20250508,"Max page: ");
    DEBUG_PLN(20250508,max_page);
    loading_sddetail = false;
    return matched > 0; // Return true if any entries were found
}




// SdFat ライブラリのファイルタイムスタンプコールバック関数。
// setup_sd() 内で SdFile::dateTimeCallback(dateTime) として登録しておくと、
// ファイル作成・更新時にこの関数が呼ばれて FAT タイムスタンプが書き込まれる。
// fileyear 等は saveCSV() 内で GNSS 時刻が最初に取得された瞬間に初期化される。
void dateTime(uint16_t* date, uint16_t* time) {
 // return date using FAT_DATE macro to format fields
 *date = FAT_DATE(fileyear, filemonth, fileday);
 // return time using FAT_TIME macro to format fields
 *time = FAT_TIME(filehour, fileminute, filesecond);
}










// SD の状態に応じて 10秒クールダウン付きで setup_sd(1) による回復を試みる。
// 複数の SD 操作関数から共通で呼ぶヘルパー。
// ケース1: 未初期化かつエラーなし（起動直後に setup_sd が失敗した状態）→ 即時リトライ
// ケース2: sdError 中 → 10秒ごとにリトライ
// どちらも lasttrytime_sd でクールダウンを管理する。
// load_settings=false にすることで、復旧時に設定値（scaleindex 等）を上書きしない。
static void try_sd_recovery() {

  // SD カードが物理的に挿入されていない場合はリトライしない
  if (digitalRead(SD_DETECT)){
    DEBUG_PLN(20250508,"SD card not detected. Skipping SD recovery.");
    return;
  }

  if (!sdInitialized && !sdError) {
    if (millis() - lasttrytime_sd > 10000) {
      lasttrytime_sd = millis();
      setup_sd(1, false);  // 復旧時は設定を再読み込みしない（ユーザー操作中の設定値を保護）
    }
  } else if (sdError) {
    if (millis() - lasttrytime_sd > 10000) {
      lasttrytime_sd = millis();
      setup_sd(1, false);  // 復旧時は設定を再読み込みしない（ユーザー操作中の設定値を保護）
    }
  }

}

// SD カードが正常に使用できる状態かどうかを返す。
// sdInitialized（初期化成功）かつ sdError（書き込みエラーなし）の両方が満たされているとき true。
// sdError 中は try_sd_recovery() で回復を試み、10秒ごとにリトライする。
bool good_sd(){

  // SD リカバリ（setup_sd 再呼出し）は Core1 でのみ実行する。
  // Core0 から try_sd_recovery() を呼ぶと SDIO バスを両コアが同時にアクセスし、
  // バスハングでフリーズする原因になる。
  if (get_core_num() == 1) {
    try_sd_recovery();
  }
  return sdInitialized && !sdError;
}


// log.txt に「起動からの経過秒:テキスト」の形式で 1 行追記する。
// good_sd() で回復チェックも兼ねて使用可否を確認する。
// 書き込み失敗時は sdError=true にして以降の書き込みを無効化する。
//
// SD.open()/close() を毎回呼ぶのではなく、静的 FsFile を使い回すことで
// open/close 時のSDIOハングリスクを最小化する。書き込み後は flush() で反映する。
static FsFile logFileStatic;  // セッション中開きっぱなし。SDエラー時のみ close。

void log_sd(const char* text){
  ASSERT_SD_CORE1("log_sd");
  if (!good_sd()) {
    if (logFileStatic.isOpen()) logFileStatic.close();  // SDエラー時はファイルをリセット
    return;
  }

  // ファイルが未オープンの場合のみ open する（毎回 open/close しない）
  if (!logFileStatic.isOpen()) {
    logFileStatic = SD.open(LOGFILE_NAME, FILE_WRITE);
  }
  if(!logFileStatic){
    DEBUGW_PLN(20250508,"ERR LOG. SD FAIL");
    sdError = true;
    return;
  }

  // 128 バイト。先頭に "<起動秒>:" を付けるため、稼働時間が延びるほど
  // 本文に使える長さが減る点に注意（起動から 10 万秒で 7 文字消費）。
  // 100 だったころは 60 秒ごとのセンサーレート行の末尾が実際に切れていた。
  char logtext[128];   // array to hold the result.
  snprintf(logtext, sizeof(logtext), "%d:%s",(int)(millis()/1000),text);
  logFileStatic.println(logtext);
  logFileStatic.flush();  // close() の代わりに flush() でデータを確定する
}


// printf 書式でフォーマットした文字列を log.txt に追記する。
// 内部で vsnprintf によりバッファに文字列化してから log_sd() を呼ぶ。最大 256 バイト。
void log_sdf(const char* format, ...){
  char buffer[256]; // Temporary buffer for formatted text
  va_list args;
  va_start(args, format);
  vsnprintf(buffer, sizeof(buffer), format, args);
  va_end(args);
  return log_sd(buffer);
}

// GNSS の飛行データを CSV ファイルに 1 行追記するフライトログ関数。
// 列: latitude, longitude, gs(m/s), TrueTrack(°), GNSS_Altitude(m), KF_Altitude(m), KF_Vspeed(m/s), pressure, date, time
// GNSS_Altitude は GNSS(NAV-PVT hMSL)が返す MSL 高度。KF_Altitude（気圧+GNSS融合のKF推定値）とは別物。
//
// ファイル名は最初に GNSS 時刻が取得された瞬間に確定し、
// 以降は同じファイルに追記し続ける（例: 2025-05-08_1230.csv）。
// ヘッダ行は headerWritten フラグで 1 回だけ書く。
// SD エラー時は 10 秒ごとに setup_sd(1) でリトライを試みる。
//
// SD.open()/close() を毎回呼ぶのではなく、静的 FsFile を使い回すことで
// open/close 時のSDIOハングリスクを最小化する。書き込み後は flush() で反映する。
// （実体は init_replay() から flush するためファイル前方で定義してある）

// ============================================================
//  受信ログ（received/）
//    自機のフライト CSV とは別ファイル・別ハンドル。
//    received/ は「無線で得た情報」だけを置く場所なので自機 GNSS は混ぜない。
//    列は自機 CSV と同じ並びにし、末尾に rssi/seq/age_ms と姿勢・風を足す。
//    姿勢・風の列名は imu_replaydata/ と同じにしてあるので、
//    **機体の SD が死んでもボート側のログで ESKF の解析ができる**。
//    揃えてあるので既存のリプレイ機能と解析ツールがそのまま使える（docs/pons_link.md §5）。
// ============================================================
static FsFile rxcsvFile;
static bool   rxHeaderWritten = false;
static int    rxfileyear = 0, rxfilemonth, rxfileday, rxfilehour, rxfileminute;

void saveRxCSV(const Task& tk) {
  ASSERT_SD_CORE1("saveRxCSV");
  const auto& a = tk.saveCsvArgs;
  if (!good_sd()) return;

  // ファイル名は最初に受信した時刻で固定する（自機 CSV と同じ流儀）。
  if (rxfileyear == 0 && a.year != 0) {
    rxfileyear = a.year; rxfilemonth = a.month; rxfileday = a.day;
    rxfilehour = a.hour; rxfileminute = a.minute;
  }
  if (rxfileyear == 0) return;          // まだ時刻が取れていない

  if (!rxcsvFile.isOpen()) {
    if (!SD.exists(REPLAY_RECEIVED_DIR)) SD.mkdir(REPLAY_RECEIVED_DIR);
    char fn[48];
    snprintf(fn, sizeof(fn), REPLAY_RECEIVED_DIR "/%04d-%02d-%02d_%02d%02d.csv",
             rxfileyear, rxfilemonth, rxfileday, rxfilehour, rxfileminute);
    rxcsvFile = SD.open(fn, FILE_WRITE);
  }
  if (!rxcsvFile) return;

  if (!rxHeaderWritten) {
    rxcsvFile.println("latitude,longitude,gs,TrueTrack,GNSS_Altitude,KF_Altitude,"
                      "KF_Vspeed,pressure,voltage,numsat,date,time,rssi,seq,age_ms,"
                      "roll,pitch,yaw,pitch_avg,roll_trim,yaw_acc95,wind_mps,wind_dir,"
                      "own_lat,own_lon,dist_m");
    rxHeaderWritten = true;
  }
  rxcsvFile.print(a.latitude, 6);  rxcsvFile.print(",");
  rxcsvFile.print(a.longitude, 6); rxcsvFile.print(",");
  rxcsvFile.print(a.gs, 1);        rxcsvFile.print(",");
  rxcsvFile.print(a.ttrack);       rxcsvFile.print(",");
  rxcsvFile.print(a.gnss_altitude, 2); rxcsvFile.print(",");
  rxcsvFile.print(a.kf_altitude, 2);   rxcsvFile.print(",");
  rxcsvFile.print(a.kf_vspeed, 2);     rxcsvFile.print(",");
  rxcsvFile.print(a.pressure, 2);      rxcsvFile.print(",");
  rxcsvFile.print(a.voltage, 2);       rxcsvFile.print(",");
  rxcsvFile.print(a.numsat);           rxcsvFile.print(",");
  char d[11]; snprintf(d, sizeof(d), "%04d-%02d-%02d", a.year, a.month, a.day);
  rxcsvFile.print(d); rxcsvFile.print(",");
  char t[12]; snprintf(t, sizeof(t), "%02d:%02d:%02d.%02d",
                       a.hour, a.minute, a.second, a.centisecond);
  rxcsvFile.print(t); rxcsvFile.print(",");
  rxcsvFile.print(a.rssi);   rxcsvFile.print(",");
  rxcsvFile.print(a.seq);    rxcsvFile.print(",");
  rxcsvFile.print(a.age_ms); rxcsvFile.print(",");

  // ★ 入っていない項目は **0 ではなく空欄**にする（imu_replaydata/ と同じ流儀）。
  //   0.00 と書くと「水平だった」「無風だった」と読めてしまい、
  //   あとから解析する人が区別できない。
  char line[96];
  char att[36], avg[10], trim[10], wind[20];
  if (a.have & RHAVE_ATT)      snprintf(att,  sizeof(att),  "%.2f,%.2f,%.2f", a.roll, a.pitch, a.yaw);
  else                         snprintf(att,  sizeof(att),  ",,");
  if (a.have & RHAVE_ATT_AVG)  snprintf(avg,  sizeof(avg),  "%.2f", a.pitch_avg);
  else                         avg[0] = '\0';
  if (a.have & RHAVE_ATT_TRIM) snprintf(trim, sizeof(trim), "%.2f", a.roll_trim);
  else                         trim[0] = '\0';
  // ヨー精度はヨーと同じ have ビットに載っている
  const bool has_yaw = (a.have & RHAVE_ATT_YAW) != 0;
  if (a.have & RHAVE_ATT_WIND) snprintf(wind, sizeof(wind), "%.2f,%.1f", a.wind_mps, a.wind_dir);
  else                         snprintf(wind, sizeof(wind), ",");
  if (has_yaw) snprintf(line, sizeof(line), "%s,%s,%s,%.0f,%s", att, avg, trim, a.yaw_acc95, wind);
  else         snprintf(line, sizeof(line), "%s,%s,%s,,%s",     att, avg, trim, wind);
  rxcsvFile.print(line); rxcsvFile.print(",");

  // ボート自身の位置と機体までの距離。無いものは 0 ではなく空欄で書く
  //（0.00 と書くと「原点にいた」「同じ場所だった」と読めてしまう）。
  char own[40];
  if (a.own_valid && !isnan(a.dist_m))
    snprintf(own, sizeof(own), "%.6f,%.6f,%.1f", a.own_lat, a.own_lon, a.dist_m);
  else if (a.own_valid)
    snprintf(own, sizeof(own), "%.6f,%.6f,",     a.own_lat, a.own_lon);
  else
    snprintf(own, sizeof(own), ",,");
  rxcsvFile.println(own);

  // 1Hz でしか来ないので毎回 flush してよい。電源断で末尾を失わないほうが大事。
  rxcsvFile.flush();
}

void saveCSV(float latitude, float longitude, float gs, int ttrack, float gnss_altitude, float kf_altitude, float kf_vspeed, float pressure, float voltage, int numsat, int year, int month, int day, int hour, int minute, int second, int centisecond) {
  ASSERT_SD_CORE1("saveCSV");
  // 未初期化・エラー時は good_sd() 内の try_sd_recovery() が10秒クールダウン付きで回復を試みる
  if (!good_sd()) {
    if (csvFileStatic.isOpen()) csvFileStatic.close();  // SDエラー時はファイルをリセット
    return;
  }

  //Run only once.
  if(fileyear == 0 && year != 0){
    fileyear = year;
    filemonth = month;
    fileday = day;
    filehour = hour;
    fileminute = minute;
    filesecond = second;
  }

  // ルート直下は設定ファイル専用にしてあるので、飛行 CSV は data/ へ書く。
  char csv_filename[40];
  snprintf(csv_filename, sizeof(csv_filename), REPLAY_FLIGHT_DIR "/%04d-%02d-%02d_%02d%02d.csv",
           fileyear, filemonth, fileday, filehour, fileminute);

  // ファイルが未オープンの場合のみ open する（毎回 open/close しない）
  if (!csvFileStatic.isOpen()) {
    if (!SD.exists(REPLAY_FLIGHT_DIR)) SD.mkdir(REPLAY_FLIGHT_DIR);
    csvFileStatic = SD.open(csv_filename, FILE_WRITE);
  }

  if (csvFileStatic) {
    if(!headerWritten){
      csvFileStatic.println("latitude,longitude,gs,TrueTrack,GNSS_Altitude,KF_Altitude,KF_Vspeed,pressure,voltage,numsat,date,time");
      headerWritten = true;
    }

    csvFileStatic.print(latitude, 6);
    csvFileStatic.print(",");
    csvFileStatic.print(longitude, 6);
    csvFileStatic.print(",");
    csvFileStatic.print(gs, 1);
    csvFileStatic.print(",");
    csvFileStatic.print(ttrack);
    csvFileStatic.print(",");
    csvFileStatic.print(gnss_altitude,2);
    csvFileStatic.print(",");
    csvFileStatic.print(kf_altitude,2);  // KF推定高度 [m]（気圧基準）
    csvFileStatic.print(",");
    csvFileStatic.print(kf_vspeed,2);   // KF推定上昇率 [m/s]
    csvFileStatic.print(",");
    csvFileStatic.print(pressure,2);
    csvFileStatic.print(",");
    csvFileStatic.print(voltage,2);   // バッテリー電圧 [V]（リプレイ時の電池表示に使う）
    csvFileStatic.print(",");
    csvFileStatic.print(numsat);      // 測位衛星数（リプレイ時の衛星数表示に使う）
    csvFileStatic.print(",");

    // Format date as YYYY-MM-DD
    char date[11];
    snprintf(date, sizeof(date), "%04d-%02d-%02d", year, month, day);
    csvFileStatic.print(date);
    csvFileStatic.print(",");

    // Format time as HH:MM:SS.ss（スプレッドシートで時刻値として読み込める形式）
    char time[12];
    snprintf(time, sizeof(time), "%02d:%02d:%02d.%02d", hour, minute, second, centisecond);
    csvFileStatic.println(time);

    // flush() は SD への物理書き込みを伴うため消費電力が大きい。
    // 2秒に1回だけ flush し、それ以外は SdFat の内部バッファに留めることで消費電力を抑制する。
    // 2Hz×2秒 = 4行×約89バイト ≈ 356バイト → 512バイトブロックバッファに収まるため安全。
    // （voltage・numsat 列の追加で 1 行あたり約 9 バイト増えたが、まだ余裕がある）
    { static unsigned long last_flush_ms = 0;
      if (millis() - last_flush_ms >= 2000) {
        TIMING_START(csv_fl);
        csvFileStatic.flush();
        TIMING_END(ts_savecsv_flush, csv_fl);
        last_flush_ms = millis();
      }
    }
    sdError = false; // Reset SD error flag after successful write
  } else {
    if (!sdError) {
      sdError = true;
    }
    sdInitialized = false; // Mark SD card as not initialized for the next attempt
  }
}

// ===== リプレイ用 ESKF 結果ログ（imu_replaydata/YYYYMMDD.txt, 5Hz） =====
// 目的は「そのとき画面に何が出ていたか」を後から再現すること。
// 生データ（imuraw/*.bin）から ESKF を回し直す案もあったが、機上のフィルタは
// シングルトンでリプレイ中に実機の姿勢推定を壊してしまうため、結果だけを残す方式にした。
//
// 列はヘッダ行の列名で解釈する（飛行 CSV と同じ方式）。後から列を足しても
// 古いファイルが読めなくなることはない。
//   time      HH:MM:SS.cc（JST）
//   roll      ESKF ロール [度]（マウント補正・ゼロ点・自動トリム適用後＝画面の値）
//   pitch     ESKF ピッチ [度]（同上）
//   yaw       ESKF ヨー [度]（真方位）
//   pitch_avg 平均ピッチ [度]。未収束のときは空欄
//   roll_trim 自動ロールトリムの累積補正量 [度]
//   yaw_acc95 ヨー精度の 95% 値 [度]。しきい値は再生時に判定するので生値で残す
//   wind_mps  推定風速 [m/s]。推定できていない区間は空欄
//   wind_dir  風が吹いていく方向の真方位 [度]。同上
//
// ESKF が未収束の間は行を書かない（行が無い＝当時も表示していない）。
// 旧 euler/ フォルダ（BNO085 由来・4列）も再生時のフォールバックとして読める。
// 50レコードごとに sync() してファイルサイズ・更新タイムスタンプをFATに反映する。
static FsFile replayDataFileStatic;
static char replayDataOpenedFilename[24] = "";  // 現在開いているファイル名
static int replayDataWriteCount = 0;            // sync() タイミング管理カウンタ

void save_imu_replaydata(int h, int m, int s, int cs,
                         float roll, float pitch, float yaw,
                         float pitch_avg, bool pitch_avg_valid,
                         float roll_trim, float yaw_acc95,
                         float wind_mps, float wind_dir, bool wind_valid,
                         const char* filename, int year, int month, int day) {
  if (!good_sd()) return;

  // ファイル名が変わった場合（日付変更等）は sync してから閉じて開き直す
  if (replayDataFileStatic.isOpen() && strcmp(replayDataOpenedFilename, filename) != 0) {
    replayDataFileStatic.sync();
    replayDataFileStatic.close();
    replayDataOpenedFilename[0] = '\0';
    replayDataWriteCount = 0;
  }

  if (!replayDataFileStatic.isOpen()) {
    // 保存先フォルダがなければ作成
    if (!SD.exists(IMU_REPLAYDATA_DIR)) {
      SD.mkdir(IMU_REPLAYDATA_DIR);
    }
    // 既存ファイルかどうか確認（ヘッダー書き込み判定用）
    bool fileExisted = SD.exists(filename);

    // 追記モードで開く
    if (!replayDataFileStatic.open(filename, O_RDWR | O_CREAT | O_APPEND)) return;
    strncpy(replayDataOpenedFilename, filename, sizeof(replayDataOpenedFilename) - 1);
    replayDataOpenedFilename[sizeof(replayDataOpenedFilename) - 1] = '\0';

    // GNSS 日時でファイルタイムスタンプを設定（作成・アクセス・更新の全3種）
    replayDataFileStatic.timestamp(T_CREATE | T_ACCESS | T_WRITE, year, month, day, h, m, s);

    // 新規ファイルのみヘッダー書き込み
    if (!fileExisted) {
      replayDataFileStatic.println(
        "time,roll,pitch,yaw,pitch_avg,roll_trim,yaw_acc95,wind_mps,wind_dir");
    }
  }

  // 平均が未収束の間は空欄にする（0.00 と書くと水平だったように見えてしまう）
  char avgbuf[10];
  if (pitch_avg_valid) snprintf(avgbuf, sizeof(avgbuf), "%.2f", pitch_avg);
  else                 avgbuf[0] = '\0';

  // 風も推定できていない区間は空欄にする（0.0 と書くと「無風」と読めてしまう）
  char wbuf[20];
  if (wind_valid) snprintf(wbuf, sizeof(wbuf), "%.2f,%.1f", wind_mps, wind_dir);
  else            snprintf(wbuf, sizeof(wbuf), ",");

  char line[96];
  snprintf(line, sizeof(line), "%02d:%02d:%02d.%02d,%.2f,%.2f,%.2f,%s,%.2f,%.1f,%s",
           h, m, s, cs, roll, pitch, yaw, avgbuf, roll_trim, yaw_acc95, wbuf);
  replayDataFileStatic.println(line);

  // 50レコードごと（約10秒@5Hz）に sync() → FATのファイルサイズ・タイムスタンプを更新
  if (++replayDataWriteCount >= 50) {
    replayDataFileStatic.timestamp(T_WRITE, year, month, day, h, m, s);  // 更新タイムスタンプを現在時刻に
    replayDataFileStatic.sync();
    replayDataWriteCount = 0;
  }
}

// 生 IMU ログのバッファ書き出しタスクを生成する。
// bufidx は imulog_take_pending() が返した索引をそのまま渡すこと
//（この索引は Core1 へ引き渡し済みとしてマークされているため、必ず enqueue する必要がある）。
Task createFlushImuLogTask(int bufidx, const char* filename,
                           int year, int month, int day, int hour, int minute, int second) {
  Task t;
  t.type = TASK_FLUSH_IMULOG;
  t.imuLogArgs.bufidx = bufidx;
  t.imuLogArgs.year   = year;
  t.imuLogArgs.month  = month;
  t.imuLogArgs.day    = day;
  t.imuLogArgs.hour   = hour;
  t.imuLogArgs.minute = minute;
  t.imuLogArgs.second = second;
  strncpy(t.imuLogArgs.filename, filename, sizeof(t.imuLogArgs.filename) - 1);
  t.imuLogArgs.filename[sizeof(t.imuLogArgs.filename) - 1] = '\0';
  return t;
}

Task createLogImuReplayTask(int h, int m, int s, int cs,
                            float roll, float pitch, float yaw,
                            float pitch_avg, bool pitch_avg_valid,
                            float roll_trim, float yaw_acc95,
                            float wind_mps, float wind_dir, bool wind_valid,
                            const char* filename, int year, int month, int day) {
  Task t;
  t.type = TASK_LOG_IMUREPLAY;
  t.imuReplayArgs.hour        = h;
  t.imuReplayArgs.minute      = m;
  t.imuReplayArgs.second      = s;
  t.imuReplayArgs.centisecond = cs;
  t.imuReplayArgs.year        = year;
  t.imuReplayArgs.month       = month;
  t.imuReplayArgs.day         = day;
  t.imuReplayArgs.roll        = roll;
  t.imuReplayArgs.pitch       = pitch;
  t.imuReplayArgs.yaw         = yaw;
  t.imuReplayArgs.pitch_avg   = pitch_avg;
  t.imuReplayArgs.pitch_avg_valid = pitch_avg_valid;
  t.imuReplayArgs.roll_trim   = roll_trim;
  t.imuReplayArgs.yaw_acc95   = yaw_acc95;
  t.imuReplayArgs.wind_mps    = wind_mps;
  t.imuReplayArgs.wind_dir    = wind_dir;
  t.imuReplayArgs.wind_valid  = wind_valid;
  strncpy(t.imuReplayArgs.filename, filename, sizeof(t.imuReplayArgs.filename) - 1);
  t.imuReplayArgs.filename[sizeof(t.imuReplayArgs.filename) - 1] = '\0';
  return t;
}

// 起動時ロゴ BMP 読み込みタスクを生成する（引数なし、ファイル名はハードコード）

// ※ 起動ロゴは src/flashdata/logo_data.cpp（FLASH）へ移した。
//   SD の logo.bmp を読む仕組みと BMP ヘッダー構造体はもう使わないので削除した。
//   SD が読めない機体でもロゴが出るようになり、起動時の 1.9 秒待ちと
//   logo_sprite の RAM 24KB も不要になっている。
