MasaoC/GPS-TFT-Map_PONS/display_tft.cpp

// ============================================================
// File    : display_tft.cpp
// Project : PONS v7 (Pilot Oriented Navigation System for HPA)
// Role    : TFTディスプレイ描画の実装。
//           ポリゴン地図（内蔵/SD）、コンパス、飛行コース矢印、
//           ヘッダー/フッター、設定画面、
//           GNSSDetail/SDDetail/マップリスト/リプレイ選択画面など全UI描画。
//           地図背景そのものは vectormap.cpp が描く。
//           描画の共通部品として、多角形の塗りつぶし（スキャンラインeven-odd）と
//           線分の画面クリップ・非アンチエイリアス太線もここに置く。
// Author  : MasaoC (@masao_mobile)
// Updated : 2026/10/08
// ============================================================
// Updates TFT display using TFT-eSPI library.

#include <cstring>  // for strlen and strcpy
#include <string>
#include <cstdlib>  // for malloc and free

#include "settings.h"
#include "display_tft.h"
#include "attitude.h"
#include "link.h"
#include "e220.h"     // 無線設定画面で SF と周波数を出すため
#include "src/flashdata/link_icons.h"
#include "src/flashdata/logo_data.h"
#include "gnss.h"
#include "mysd.h"
#include "navdata.h"
#include "src/flashdata/font_data.h"
#include "src/sound.h"
#include "src/button.h"
#include "airdata.h"
#include "imu.h"
#include "imu_sensor.h"   // imu_caps()（融合出力が有るかの判定）
#include "src/vectormap.h"
#include "TFT_eSPI/CopySetupFile_TFT_eSPI.h"

// フォント定義: TFT_eSPI のカスタムフォント（PROGMEM 格納）
#define AA_FONT_SMALL NotoSansBold15   // アンチエイリアス付き小サイズフォント（地図テキスト等）
#define NM_FONT_MEDIUM Arial_Black22   // 中サイズフォント（ESKF のロール・ピッチ表示）
#define NM_FONT_LARGE Arial_Black56    // 大サイズフォント（ヘッダーの速度・真方位表示）

// ---- 処理時間計測変数（BNO085配置コア決定用、デバッグビルドのみ） ----
#ifndef RELEASE
TimingStat ts_draw_header     = TSTAT_INIT("C0_draw_header");
TimingStat ts_push_backscreen = TSTAT_INIT("C0_push_backscreen");
#endif

// ===== TFT スプライト =====
// tft        : TFT_eSPI 本体（240×320px）。直接描画は非推奨で、スプライト経由が基本。
// backscreen : メインの 240×240 マップ描画用スプライト。描画後 pushSprite(0,50) で転送。
// header_footer: ヘッダー（50px）・フッター（30px）共有スプライト。pushSprite で位置を変えて転送。
TFT_eSPI tft = TFT_eSPI();                 // Invoke custom library
TFT_eSprite backscreen = TFT_eSprite(&tft);
TFT_eSprite header_footer = TFT_eSprite(&tft);
TFT_eSprite vsi_sprite = TFT_eSprite(&tft);  // VSIインジケーター (5×240px, 16bit, 2,400 Byte)

// ===== 地図方向モード =====
// NORTHUP: 地図は常に北が上。TRACKUP: 進行方向が上に来るように回転する。
#define MODE_TRACKUP 0
#define MODE_NORTHUP 1
#define MODE_SIZE 2
// ★ 初期値は **SD を読めなかったときの既定値**（SD があれば loadSettings() が上書きする）。
int upward_mode = MODE_TRACKUP;




extern volatile int sound_volume;
extern volatile int vario_volume;
extern volatile bool vario_inhibit;
extern int screen_mode;
extern int destination_mode;


// 地図座標から作った線を backscreen に描く際は、必ずこの 2 つを使うこと。
// 緯度経度由来の座標は高倍率で画面外へ大きく飛び出し、そのまま TFT_eSPI に
// 渡すと画面外を延々と走査して 1 フレームに数百 ms かかる
// （理由は clip_line_to_screen のコメント）。
static inline void draw_clipped_line(int x0, int y0, int x1, int y1, uint16_t col) {
  if (!clip_line_to_screen(&x0, &y0, &x1, &y1)) return;
  backscreen.drawLine(x0, y0, x1, y1, col);
}
static inline void draw_clipped_wideline(int x0, int y0, int x1, int y1, int w, uint16_t col) {
  if (!clip_line_to_screen(&x0, &y0, &x1, &y1)) return;
  backscreen.drawWideLine(x0, y0, x1, y1, w, col);
}

// 地図座標から作った線を、本数が多い箇所で描くための関数。
//
// TFT_eSPI の drawWideLine は bg_color の既定値が 0x00FFFFFF で、この経路では
// アンチエイリアス画素ごとに readPixel() を呼んで setWindow をやり直し、さらに
// wedgeLineDistance() の浮動小数点距離計算を画素ごとに行う（drawWedgeLine 参照）。
// 見た目は綺麗だが単価が高く、地図の道路や 500 点のトラックのように線が数百〜数千本
// になる描画では支配的なコストになる。
// 240px の画面ではアンチエイリアスの効果も小さいので、平行な drawLine を重ねて太らせる。
//
// 誘導線やパイロン基準線のように本数が少なく目立つ線は、従来どおり
// draw_clipped_wideline（アンチエイリアス付き）のままにしてある。
void draw_map_line(int x0, int y0, int x1, int y1, int w, uint16_t col) {
  if (!clip_line_to_screen(&x0, &y0, &x1, &y1)) return;
  backscreen.drawLine(x0, y0, x1, y1, col);
  if (w <= 1) return;
  // 線の主方向に対して垂直側へずらして重ねる（斜めでも太さがほぼ揃う）
  const bool steep = abs(y1 - y0) > abs(x1 - x0);
  for (int o = 1; o <= (w - 1) / 2; o++) {
    if (steep) {
      backscreen.drawLine(x0 - o, y0, x1 - o, y1, col);
      backscreen.drawLine(x0 + o, y0, x1 + o, y1, col);
    } else {
      backscreen.drawLine(x0, y0 - o, x1, y1 - o, col);
      backscreen.drawLine(x0, y0 + o, x1, y1 + o, col);
    }
  }
  if (w % 2 == 0) {  // 偶数幅は片側にもう 1 本足す
    if (steep) backscreen.drawLine(x0 + w / 2, y0, x1 + w / 2, y1, col);
    else backscreen.drawLine(x0, y0 + w / 2, x1, y1 + w / 2, col);
  }
}

// 地図方向モードを NORTHUP ↔ TRACKUP で切り替える。
void toggle_mode() {
  upward_mode = (upward_mode + 1) % MODE_SIZE;
}

bool is_northupmode() { return upward_mode == MODE_NORTHUP; }
bool is_trackupmode() { return upward_mode == MODE_TRACKUP; }

// TRACKUP モードでは自機を画面下寄り（BACKSCREEN_SIZE*3/4）に表示し、前方視界を広げる。
// NORTHUP モードでは従来通り中央（BACKSCREEN_SIZE/2）を返す。
inline int get_self_cy() {
  return is_trackupmode() ? (BACKSCREEN_SIZE * 3 / 4) : (BACKSCREEN_SIZE / 2);
}



// 緯度経度をスプライト（backscreen）上のピクセル座標に変換する。
// Mercator 投影で X（経度差）・Y（緯度差）を km 距離に変換し、
// mapScale（px/km）を掛けてピクセル量にする。
// mapUpDirection（度）だけ回転させることで TRACKUP モードに対応する。
// スプライト中心が現在位置（mapCenterLat/Lon）に対応する。
// 戻り値の Y 座標は TFT 座標系（下が正）のため yDist を反転させる。
cord_tft latLonToXY(float lat, float lon, float mapCenterLat, float mapCenterLon, float mapScale, float mapUpDirection) {
  // Calculate x distance (longitude) = Approx distance per degree longitude in km with Mercator projection.
  float xDist = (lon - mapCenterLon) * 111.321;  // 1 degree longitude = ~111.321 km
  // Calculate y-coordinates in Mercator projection
  // ★ 地図中心の Mercator Y は 1 フレームの間ずっと同じ値なのに、以前は呼ばれるたびに
  //   log(tan()) を計算し直していた。航跡 500 点を描くだけで無駄が 500 回分になる。
  //   入力が変わったときだけ計算する（pla_centerline_bearing_rad() と同じやり方）。
  //   latLonToXY() は Core0 の描画からしか呼ばれないので static で問題ない。
  static float  cached_center_lat = NAN;
  static double cached_yA         = 0;
  if (mapCenterLat != cached_center_lat) {
    // 値を先に書き、**キーは最後に公開する**（init_destinations() と同じ流儀）。
    // 逆順だと「キーは新しいのに値がまだ古い」状態が一瞬できる。
    // いまは同時に読む主体がいないので実害は無いが、順序を揃えておく。
    cached_yA         = latitudeToMercatorY(mapCenterLat);
    cached_center_lat = mapCenterLat;
  }
  double yA = cached_yA;
  double yB = latitudeToMercatorY(lat);
  // Calculate the distance on the y-axis
  double yDist = (yB - yA)* 6378.22347118;// 1 radian latitude（Mercator Y軸）= 111.321 *180/3.1415 = 6378.22347118 km（地球半径に相当）
  // Apply scale factor
  xDist *= mapScale;
  yDist *= mapScale;
  // Apply rotation for map up direction
  float angleRad = mapUpDirection * DEG_TO_RAD;
  float rotatedX = xDist * cos(angleRad) - yDist * sin(angleRad);
  float rotatedY = xDist * sin(angleRad) + yDist * cos(angleRad);
  // Translate to screen coordinates
  // TRACKUP: 自機は get_self_cy()=180 を基準、NORTHUP: 120（中央）
  return cord_tft{
    (BACKSCREEN_SIZE / 2) + (int)rotatedX,
    get_self_cy() - (int)rotatedY  // Y is inverted on the screen
  };
}





// TFT ディスプレイと描画スプライトを初期化する。
// 1. TFT_WR / TFT_DC を LOW にしてから TFT を起動する。
// 2. VERTICAL_FLIP マクロでパネル向きを切り替える（setRotation）。
// 3. backscreen（240×BACKSCREEN_SIZE）と header_footer（240×HEADERFOOTER_HEIGHT）スプライトを作成する。
// スプライトは一度だけ作成すれば再利用できるため、created() で二重作成を防ぐ。
void setup_tft() {

  //TFT_WR 
  gpio_init(TFT_WR);
  gpio_set_dir(TFT_WR, GPIO_OUT);
  gpio_put(TFT_WR, 0);


  //TFT_DC
  gpio_init(TFT_DC);
  gpio_set_dir(TFT_DC, GPIO_OUT);
  gpio_put(TFT_DC, 0);


  tft.begin();

#ifdef VERTICAL_FLIP
  tft.setRotation(0);           //set 0 for newhaven
#else
  tft.setRotation(2);           //set 2 for normal（VERTICAL_FLIP 未定義時）
#endif

  tft.loadFont(AA_FONT_SMALL);  // Must load the font first
  tft.fillScreen(COLOR_WHITE);



  if(!backscreen.created()){
    backscreen.setColorDepth(16);
    backscreen.createSprite(SCREEN_WIDTH, BACKSCREEN_SIZE);
    backscreen.loadFont(AA_FONT_SMALL);
  }
  if(!header_footer.created()){
    header_footer.setColorDepth(16);
    header_footer.createSprite(SCREEN_WIDTH, HEADERFOOTER_HEIGHT);
    header_footer.loadFont(NM_FONT_LARGE);
  }
  // VSIスプライト: 5px幅 × 240px高さ、16bit色深度（RAM消費 2,400 Byte）
  if(!vsi_sprite.created()){
    vsi_sprite.setColorDepth(16);
    vsi_sprite.createSprite(VSI_W, BACKSCREEN_SIZE);
  }
}



// ※ かつてここに Point / Text / TextManager（ID 付きテキストの差分更新描画）があったが、
//    最終的な利用箇所が設定画面のタイトル 1 箇所だけになったため v0.947 で削除した。
//    画面外判定は cord_tft::isOutsideTft()（display_tft.h）を使うこと。





// 指定した km 値のスケールバーを backscreen の右下端に描画する。
// 画面に収まるサイズ（140px 以内）のときのみ描画し、true を返す。
// 緯度補正（cos(lat)）を加えることで Mercator 歪みに対応したスケールを表示する。
bool try_draw_km_distance(float scale, float km) {
  double latnow = get_gnss_lat();
  if(latnow <-80 || latnow > 80){
    latnow = 35;
  }
  int distance_px =  scale*km/cos(radians(latnow));//scale * km;  //scale is px/km
  if(distance_px > 140)
    return false;

  int ypos = 240-2;
  int xpos = 240-2-5;  // VSI（右端5px）と重ならないよう5px左にオフセット

  backscreen.drawFastVLine(xpos, ypos-distance_px, distance_px, COLOR_BLACK);
  backscreen.drawFastHLine(xpos-5, ypos, 5, COLOR_BLACK);
  backscreen.drawFastHLine(xpos-5, ypos-distance_px, 5, COLOR_BLACK);
  backscreen.setTextSize(1);
  backscreen.setTextColor(COLOR_BLACK);
  if(km >= 100){
    backscreen.setCursor(xpos-18,ypos-distance_px-8);
    backscreen.printf("%d",(int)km);
  }
  else if(km < 1.0 ){
    backscreen.setCursor(xpos-18,ypos-distance_px-8);
    backscreen.printf("%.1f",km);
  }else{
    backscreen.setCursor(xpos-11,ypos-distance_px-8);
    backscreen.printf("%d",(int)km);
  }
  backscreen.setCursor(xpos-12,ypos-distance_px);
  backscreen.print("km");
  return true;
}


// コンパスの N/E/S/W ラベルを backscreen 上に描画する。
// truetrack: 現在の真方位（度）。N/E/S/W の位置は truetrack 方向を基準に算出する。
// NORTHUP モードでは dist=100px（広め）、TRACKUP モードでは dist=73px（狭め）にして
// 進行方向矢印（draw_triangle）と重ならないようにする。
// N/E/S/W は真方位。磁気コンパスを載せない方針になったので偏角補正はしない。
void draw_compass(float truetrack, uint16_t col) {
  backscreen.setTextWrap(false);
  // 半径は元の 2/3。地図左下のピッチ・ロール表示と N/E/S/W が重なって
  // 読みにくかったため縮めてある（針の長さ get_needle_len() は変えていない）。
  int dist = 73 * 2 / 3 - 4;
  if (is_northupmode()) {
    dist = 100 * 2 / 3 - 4;
  }
  int centerx = BACKSCREEN_SIZE / 2;
  int centery = get_self_cy();  // TRACKUP=180, NORTHUP=120
  // 偏角は加えない（真方位表示）
  float radian = deg2rad(truetrack);
  backscreen.setTextColor(col, COLOR_WHITE);
  backscreen.setTextSize(2);
  backscreen.loadFont(AA_FONT_SMALL);
  

  cord_tft n = { int(centerx + sin(-radian) * dist), int(centery - cos(radian) * dist) };
  cord_tft e = { int(centerx + cos(radian) * dist), int(centery - sin(radian) * dist) };
  cord_tft s = { int(centerx + sin(radian) * dist), int(centery + cos(radian) * dist) };
  cord_tft w = { int(centerx - cos(-radian) * dist), int(centery - sin(-radian) * dist) };
  if (!n.isOutsideTft()) {
    backscreen.setTextColor(COLOR_RED, COLOR_WHITE);  // N は赤
    backscreen.setCursor(n.x - 5, n.y - 5);
    backscreen.print("N");
    backscreen.setTextColor(col, COLOR_WHITE);         // 残りは元の色に戻す
  }
  if (!e.isOutsideTft()) {
    backscreen.setCursor(e.x - 5, e.y - 5);
    backscreen.print("E");
  }
  if (!s.isOutsideTft()) {
    backscreen.setCursor(s.x - 5, s.y - 5);
    backscreen.print("S");
  }
  if (!w.isOutsideTft()) {
    backscreen.setCursor(w.x - 5, w.y - 5);
    backscreen.print("W");
  }

  // 斜め方位（NW/NE/SE/SW）は画面が混むので描かない。
  backscreen.setTextWrap(true);
}




// 現在のスケールに適した距離スケールバーを最大 2 本描画する。
// 候補リストを大きい順に試し、140px 以内に収まる最初の 2 候補を表示する。
// 2 本描画したら終了（それ以上は画面が煩雑になるため）。
void draw_km_distances(float scale) {
  const float distances[] = {400, 200, 100, 50, 20, 10, 5, 2, 1, 0.4, 0.2};
  int draw_counter = 0;

  backscreen.unloadFont();

  for (float d : distances) {
    if (try_draw_km_distance(scale, d)) {
      draw_counter++;
      if (draw_counter >= 2)
        break;
    }
  }

  // スケールバーが 2 本に届かなくても必ずフォントを戻す。
  // 戻し忘れると以降に描く [GS]/[m/s]/[MT] やコース警告が内蔵フォントになり、
  // 表示が崩れる（スケールによって発生したりしなかったりする不具合の原因）。
  backscreen.loadFont(AA_FONT_SMALL);
}

// ===== マップ描画管理変数 =====
bool fresh = false;         // 地図の強制再描画フラグ（スケール変更時などに true にする）
float last_scale = 1.0;     // 前回描画時のスケール（変化を検知するための記憶値）
float last_up = 0;          // 前回描画時の mapUpDirection







#define TRIANGLE_HWIDTH 6
#define TRIANGLE_SIZE 18





extern float last_tone_tt;
extern unsigned long trackwarning_until;



// コース逸脱警告ボックスを backscreen に描画する。
// 1 秒おきに点滅（(millis()/1000)%2 == 0 のときだけ描画）し、
// steer_angle の符号で "Turn RIGHT" / "Turn LEFT" を切り替える。
// 呼び出しはメインの draw ループから angle_diff > 15° のときに行われる。
void draw_course_warning(float steer_angle){
  if((millis()/1000)%2 == 0){
    // TRACKUP: 自機アイコン尾翼（cy+9=189）の下にボックスを配置する
    int box_y = is_trackupmode() ? (get_self_cy() + 12) : 175;  // TRACKUP=192, NORTHUP=175
    backscreen.fillRect(5, box_y, SCREEN_WIDTH-5*2, 25, COLOR_WHITE);
    backscreen.drawRect(5, box_y, SCREEN_WIDTH-5*2, 25, COLOR_RED);
    backscreen.drawRect(6, box_y+1, SCREEN_WIDTH-5*2-2, 25-2, COLOR_RED);
    backscreen.setTextColor(COLOR_RED);
    if(steer_angle > 0){
      backscreen.setCursor(23, box_y+5);
      backscreen.print("Turn RIGHT! Turn RIGHT!");
    }
    else{
      backscreen.setCursor(30, box_y+5);
      backscreen.print("Turn LEFT! Turn LEFT!");
    }
  }
}

extern float course_warning_index;
const int NEEDLE_LEN_NORTHUP = 120;  // 針の長さ（px）。スプライト半径の最大値に合わせてある。
const int NEEDLE_LEN_TRACKUP = 180;  // TRACKUP モード用: 自機が下寄りのため前方スペースが広く、長めにする。
const int NEEDLE_LEN = NEEDLE_LEN_NORTHUP;  // 後方互換用。実際の使用箇所では get_needle_len() を推奨。
inline int get_needle_len() { return is_trackupmode() ? NEEDLE_LEN_TRACKUP : NEEDLE_LEN_NORTHUP; }

// 機体位置マーカー（飛行機アイコン）とコース逸脱表示を backscreen に描画する。
//
// NORTHUP モード（自機マーカー + コース針）:
//   - 機体アイコン: 主翼の横棒、尾翼の横棒、胴体線の 3 本で表現（進行方向 = ttrack）。
//   - True Track 維持針(三角形): 長さ NEEDLE_LEN の太線（last_tone_tt 方向へ伸びる）。
//   - コース逸脱 arc: steer_angle に比例した赤い弧で偏差を視覚化。
//   - 誘導三角形: steer_angle > 15°, 55°, 100° の 3 段階で赤い三角形を追加表示。
//     ※ trackwarning_until で警告持続時間を管理し、時間切れ後は黒枠のみに戻る。
//
// TRACKUP モード（固定マーカー）:
//   - 進行方向は常に上なので、中心の垂直線 + 翼横棒の固定アイコンのみ描画する。

// GNSS fix なし時に飛行機マークの代わりにグレーの × を中央に描画する。
// × のサイズは飛行機アイコンと同程度（腕の長さ 12px）。
void draw_nofix_cross() {
  const int cx   = BACKSCREEN_SIZE / 2;  // = 120（X は常に中央）
  const int cy   = get_self_cy();        // TRACKUP=180, NORTHUP=120
  const int arm  = 12;                   // × の腕の長さ [px]
  // TRACKUP: GNSS 精度に関わらず、進行方向を示す縦線は常に表示する
  if (is_trackupmode()) {
    const int shortening = 15;
    backscreen.drawFastVLine(cx,     shortening, cy - shortening - 5, COLOR_BLACK);
    backscreen.drawFastVLine(cx + 1, shortening, cy - shortening - 5, COLOR_BLACK);
  }
  backscreen.drawWideLine(cx - arm, cy - arm, cx + arm, cy + arm, 3, COLOR_GRAY);
  backscreen.drawWideLine(cx + arm, cy - arm, cx - arm, cy + arm, 3, COLOR_GRAY);
}

// hAcc 不良時に飛行機マークの代わりに自機位置の不確かさ円を描画する。
// gnssFixOK=false の場合は常にこの関数が呼ばれる。
// 動作:
//   1. 中心に青い塗りつぶし小円（HDOP_CENTER_DOT_RADIUS px）で位置を示す。
//   2. 誤差半径 = hacc_mm [mm] → [m] → [km] → ピクセル換算して青い輪郭円を描画。
//   3. 輪郭円半径 < HDOP_MIN_CIRCLE_RADIUS の場合は輪郭円を省略し、精度数値をテキストで表示する。
void draw_hacc_circle(double scale, uint32_t hacc_mm) {
  const int cx = BACKSCREEN_SIZE / 2;  // = 120（X は常に中央）
  const int cy = get_self_cy();        // TRACKUP=180, NORTHUP=120

  // TRACKUP: GNSS 精度に関わらず、進行方向を示す縦線は常に表示する
  if (is_trackupmode()) {
    const int shortening = 15;
    backscreen.drawFastVLine(cx,     shortening, cy - shortening - 5, COLOR_BLACK);
    backscreen.drawFastVLine(cx + 1, shortening, cy - shortening - 5, COLOR_BLACK);
  }

  // 誤差半径: [mm] → [m] → [km] → ピクセル（四捨五入で正確な円サイズに）
  float accuracy_m = hacc_mm / 1000.0f;
  int r = (int)roundf((accuracy_m / 1000.0f) * (float)scale);

  // 中心位置を示す小さい塗りつぶし青円
  backscreen.fillCircle(cx, cy, HDOP_CENTER_DOT_RADIUS, COLOR_BLUE);

  // 円半径がバックスクリーン半分を超えると画面外にはみ出して青い点だけに見えるため、
  // 大きすぎる場合もテキスト表示にフォールバックする。
  const int MAX_CIRCLE_R = BACKSCREEN_SIZE / 2;  // 120px

  if (r >= HDOP_MIN_CIRCLE_RADIUS && r <= MAX_CIRCLE_R) {
    // 不確かさ範囲を示す輪郭青円
    backscreen.drawCircle(cx, cy, r, COLOR_BLUE);
  } else {
    // 円が小さすぎ／大きすぎる場合: 精度数値をテキストで表示（例: "Acc:8m" / "Acc:1.2km"）
    char buf[16];
    if (accuracy_m < 1000.0f)
      snprintf(buf, sizeof(buf), "Acc:%.0fm", accuracy_m);
    else
      snprintf(buf, sizeof(buf), "Acc:%.1fkm", accuracy_m / 1000.0f);
    backscreen.setTextSize(1);
    backscreen.setTextColor(COLOR_BLUE, COLOR_BLACK);
    backscreen.setCursor(cx + HDOP_CENTER_DOT_RADIUS + 2, cy - 4);
    backscreen.print(buf);
  }
}

// ESKF の姿勢を画面に出してよいかを判定する。
// リプレイ中は CSV に IMU 生データ（.bin）が入っていないため ESKF には
// 「いま机の上にある本体」の姿勢しか流れてこない。再生中の飛行と全く無関係な
// ロール・ピッチ・ヨーが出てしまい誤解を招くので、リプレイ中はまとめて非表示にする。
// （将来 .bin まで再生できるようにしたら、この判定を外せばよい）
// デモモード用の疑似風。表示の確認だけが目的で、実機の推定（attitude.cpp）には触れない。
// 風速 0〜6 m/s を 24 秒周期で往復させ、風向は 30 秒で 1 回転させる。
// これで 3 色すべてと全方位を机の上で一通り確認できる。
// ※ ESKF が収束していないと draw_eskf_attitude() 自体が描かれないので、
//   GNSS の入る場所（屋外・窓際）でデモを動かすこと。
static bool demo_wind(float &speed_mps, float &dir_to_deg) {
  const uint32_t ms = millis();
  speed_mps  = 3.0f * (1.0f - cosf((float)(ms % 24000u) * (2.0f * (float)M_PI / 24000.0f)));
  dir_to_deg = (float)(ms % 30000u) * (360.0f / 30000.0f);
  return true;
}

// デモ用の機首方位（真方位）。デモの疑似風と対地速度から偏流角を作るので、
// 風の矢印の向きと機首の振れが連動して見え、デモとして自然になる。
//   対気速度ベクトル = 対地速度ベクトル - 風ベクトル、その向きが機首方位。
// 実際の偏流角は横風が強いと 60 度近くになるが、デモの見た目としては大きすぎるので
// DEMO_CRAB_MAX_DEG に制限する。
static bool demo_heading(float &yaw_deg) {
  float ws, wd;
  if (!demo_wind(ws, wd)) return false;
  const float trk = (float)get_gnss_truetrack();
  float vg = (float)get_gnss_mps();
  if (vg < 1.0f) vg = 1.0f;
  const float te = vg * sinf(deg2rad(trk)) - ws * sinf(deg2rad(wd));
  const float tn = vg * cosf(deg2rad(trk)) - ws * cosf(deg2rad(wd));
  float crab = atan2f(te, tn) * 180.0f / (float)M_PI - trk;
  while (crab >  180.0f) crab -= 360.0f;
  while (crab < -180.0f) crab += 360.0f;
  if (crab >  DEMO_CRAB_MAX_DEG) crab =  DEMO_CRAB_MAX_DEG;
  if (crab < -DEMO_CRAB_MAX_DEG) crab = -DEMO_CRAB_MAX_DEG;
  yaw_deg = trk + crab;
  return true;
}

// 表示に使うヨー（真方位）と、その 95% 精度。
// デモは疑似値、リプレイは記録値、通常は ESKF の推定値。ここに集約して、
// 自機アイコンの向き・ヨー数値・偏流点線・信頼度判定が食い違わないようにする。
static bool eskf_display_yaw(float &yaw_deg) {
  if (is_demo_active()) return demo_heading(yaw_deg);
  // ★ 無線のミラー中は受信した機体の姿勢を出す。姿勢エンジン本体は触らないので、
  //   受信機自身の較正やロールトリムは無傷のまま（link.cpp のコメント参照）。
  if (link_mirror_active()) { float a; return link_get_yaw(yaw_deg, a); }
  if (getReplayMode())  { float a; return get_replay_yaw(yaw_deg, a); }
  if (!attitude_ready()) return false;
  float r, p;
  attitude_get_euler(r, p, yaw_deg);
  return true;
}
static bool eskf_display_yaw_acc(float &acc95) {
  if (is_demo_active()) { acc95 = DEMO_YAW_ACC95_DEG; return true; }
  if (link_mirror_active()) { float y; return link_get_yaw(y, acc95); }
  if (getReplayMode())  { float y; return get_replay_yaw(y, acc95); }
  if (!attitude_ready()) return false;
  acc95 = attitude_get_yaw_acc95_deg();
  return true;
}

bool eskf_display_enabled() {
  // マスタースイッチ。OFF なら地図上の姿勢表示は一切出さない（リプレイ含む）。
  // 表示系はすべてこの関数を通るので、ここ 1 か所で塞げる。
  if (!attitude_get_rpy_enabled()) return false;
  // ミラー中は「受信データに姿勢が載っているか」で判断する。
  if (link_mirror_active()) { float r, p; return link_get_attitude(r, p); }
  // リプレイ中は IMU 生データ（.bin）を再生しないので実機 ESKF の値は使えないが、
  // 同じ日の姿勢ログ（imu_replaydata/ か旧 euler/）があれば当時の値を再現できる。
  if (getReplayMode()) {
    float r, p;
    return get_replay_attitude(r, p);
  }
  return attitude_ready();
}

// 「いま画面に出している姿勢」が較正のやり直しを必要としているか。
// ★ **表示の供給元 3 系統すべてを面倒見ること。** 判断の対象は
//   *この装置の ESKF* ではなく *画面に出ている数字の出どころ* である。
//   以前は `attitude_needs_apply()`（自機）を直接見ていたため、
//   **ミラー中のボート側が、機体は健全なのに「較正しろ」と出していた**
//   （逆に機体が未較正でもボートが健全なら警告が消え、**出したい警告が出ない**）。
//   送信機の needs_apply は LINK_ST_NEEDS_APPLY で運んである
//   （link_proto.h の status 設計「受信側から知りようがない送信機自身の健康状態」）。
//   リプレイ中は false。記録済みの姿勢に、いまの較正状態は関係ない
//   （手元で傾けて OFF MOUNT になっても、その飛行時には起きていない警告になる）。
//   音のほうは `loop()` の地上判定が `!link_mirror_active()` で既に塞いである。
static bool eskf_display_needs_apply() {
  if (link_mirror_active()) return (link_sender_status() & LINK_ST_NEEDS_APPLY) != 0;
  if (getReplayMode())      return false;
  return attitude_needs_apply();
}

// 測位品質（sAcc / vAcc）を「不明」として出すべきか。
// ★ **PONS Link が運ぶ測位品質は hAcc / numsat / fixOK だけ**（link_proto.h の
//   LinkTelem。65 バイト固定なので安易に足せない）。sAcc と vAcc は載っていない。
//   それなのに get_gnss_sacc_mmps() / get_gnss_vacc_mm() はミラーで差し替わらない
//   ので、**ミラー中は受信機自身の値がそのまま出る**。隣に並ぶ GS・高度・hAcc は
//   機体の値なので、**機体の測位品質だと読まれる**（ボートは止まっているから
//   いつも緑で、機体の測位が荒れていても気づけない）。出さずに「--」にする。
//   accessor 側で 0 を返させてはいけない。受信機の GNSS 詳細画面で自機の
//   測位品質を見たい場面があり、そこまで潰れてしまう。
static bool gnss_acc_unknown() { return link_mirror_active(); }

// ESKF のヨー（真方位）を表示・アイコン回転に使ってよいかを判定する。
// ヨーは水平加速度がある間しか可観測にならず、等速直進が続くと際限なく漂うため、
// 推定精度がしきい値以下のときだけ「機首方向」として信用する。
// 判定は 95%(2σ) で行う。1σ のまま「これ以下なら安心」と扱うと 3 回に 1 回は外れる。
bool eskf_calib_allowed() {
  if (!attitude_ready()) return false;
  // 通常は対地速度で「地上にいる」ことを確認する。
  if (!getReplayMode() && !is_demo_active() && !link_mirror_active())
    return get_gnss_mps() <= LEVEL_CALIB_MAX_MPS;
  // デモ・リプレイ・ミラー中は get_gnss_mps() が**この装置以外の速度**を返すため、
  // 実機が机の上で止まっていても「飛行中」と判定されて APPLY できなくなる。
  // ★ ミラーはさらに逆も起きる。機体がプラットホームで止まっていれば、
  //   **走っているボートの上で APPLY が通ってしまう**（較正が船の姿勢で上書きされる）。
  //   ここは自機の較正操作を許すかどうかの判断なので、機体の速度を見てはいけない。
  // GNSS が偽物なので、代わりに IMU 由来の静止判定を使う。これは再生データでは
  // 偽装できない実機の物理状態なので、飛行中に誤って較正する危険も無い。
  return attitude_is_static();
}

// 95%値としきい値の比較にヒステリシスを掛ける共通処理。
// held: 直前の判定結果（呼び出し側が保持する）。
// 入るときは limit、出るときは limit + ESKF_YAW_TRUST_HYST_DEG で判定する。
static bool yaw_acc_ok_hyst(float acc95, float limit, bool &held) {
  held = held ? (acc95 < limit + ESKF_YAW_TRUST_HYST_DEG)
              : (acc95 < limit);
  return held;
}

bool eskf_yaw_reliable() {
  // リプレイは記録された 95% 値で当時と同じ判定を再現する。しきい値は現在の設定を
  // 使うので、後からしきい値を変えて過去フライトを見直すこともできる。
  static bool held = false;
  float acc95;
  if (!eskf_display_enabled() || !eskf_display_yaw_acc(acc95)) { held = false; return false; }
  return yaw_acc_ok_hyst(acc95, ESKF_YAW_TRUST_95_DEG, held);
}

// ヨーが「著しく信頼できる」か（95%値 < ESKF_YAW_DRIFT_95_DEG）。
// 偏流角を示す点線を出してよいかの判定に使う。eskf_yaw_reliable() より厳しい。
static bool eskf_yaw_high_confidence() {
  static bool held = false;
  float acc95;
  if (!eskf_display_enabled() || !eskf_display_yaw_acc(acc95)) { held = false; return false; }
  return yaw_acc_ok_hyst(acc95, ESKF_YAW_DRIFT_95_DEG, held);
}

// 自機アイコンの色。ESKF のヨーで機首を向けているときは黒、
// 単に対地進路（トラック）を向けているだけのときはグレー。
// 「いま見えている向きが機首なのかトラックなのか」を色で区別できるようにする。
// ※ ヨーの情報源が無い場合（BNO085 非搭載機、姿勢ログの無いリプレイ）は
//   区別する意味が無いので従来どおり黒。ここを入れないと IMU の無い個体で
//   アイコンが永久にグレーになってしまう。
static uint16_t plane_icon_color() {
  bool have_yaw_source;
  if (link_mirror_active()) { float y, a; have_yaw_source = link_get_yaw(y, a); }
  else if (getReplayMode()) { float y, a; have_yaw_source = get_replay_yaw(y, a); }
  else                      { have_yaw_source = get_imu_ok(); }
  if (!have_yaw_source) return COLOR_BLACK;
  return eskf_yaw_reliable() ? COLOR_BLACK : COLOR_GRAY;
}

// 自機アイコン（主翼・尾翼・胴体の 3 本＝「士」の形）を任意の向きで描く。
// screen_deg: 画面の上を 0 とした時計回りの角度 [度]。
//   NORTHUP は画面上＝北なので、そのまま方位を渡せばよい。
//   TRACKUP は画面上＝対地進路なので (方位 - トラック) を渡す（＝偏流角）。
// ここを機首方位で呼べばアイコンが実際の機首を向き、トラックで呼べば従来どおり。
static void draw_plane_icon(int cx, int cy, float screen_deg, uint16_t col) {
  const float a = deg2rad(screen_deg);
  const float ca = cos(a), sa = sin(a);

  int left_wing_x  = cx - TRIANGLE_HWIDTH * 2 * ca;
  int left_wing_y  = cy - TRIANGLE_HWIDTH * 2 * sa;
  int right_wing_x = cx + TRIANGLE_HWIDTH * 2 * ca;
  int right_wing_y = cy + TRIANGLE_HWIDTH * 2 * sa;
  int left_tail_x  = cx + (-TRIANGLE_HWIDTH / 2) * ca - (0.5 * TRIANGLE_SIZE) * sa;
  int left_tail_y  = cy + (-TRIANGLE_HWIDTH / 2) * sa + (0.5 * TRIANGLE_SIZE) * ca;
  int right_tail_x = cx + (TRIANGLE_HWIDTH / 2) * ca - (0.5 * TRIANGLE_SIZE) * sa;
  int right_tail_y = cy + (TRIANGLE_HWIDTH / 2) * sa + (0.5 * TRIANGLE_SIZE) * ca;
  int body_tail_x  = cx - TRIANGLE_SIZE / 2 * sa;
  int body_tail_y  = cy + TRIANGLE_SIZE / 2 * ca;

  backscreen.drawWideLine(left_wing_x, left_wing_y, right_wing_x, right_wing_y, 3, col);
  backscreen.drawWideLine(left_tail_x, left_tail_y, right_tail_x, right_tail_y, 2, col);
  backscreen.drawWideLine(cx, cy, body_tail_x, body_tail_y, 2, col);

  // ヨーが著しく信頼できるときだけ、機首の先へ点線を伸ばす。
  // TRACKUP では画面上＝トラックなので、この点線の傾きがそのまま偏流角になる。
  // NORTHUP では針（トラック）との開きが偏流角。
  // 前方は screen_deg=0 で画面上向き＝(+sa, -ca)。
  if (eskf_yaw_high_confidence()) {
    const int step = ESKF_DRIFT_LINE_DASH_PX + ESKF_DRIFT_LINE_SKIP_PX;  // 実線 + 空白
    for (int d = ESKF_DRIFT_LINE_GAP_PX;
         d < ESKF_DRIFT_LINE_GAP_PX + ESKF_DRIFT_LINE_LEN_PX; d += step) {
      int x0 = cx + (int)lroundf(sa * d);
      int y0 = cy - (int)lroundf(ca * d);
      int x1 = cx + (int)lroundf(sa * (d + ESKF_DRIFT_LINE_DASH_PX));
      int y1 = cy - (int)lroundf(ca * (d + ESKF_DRIFT_LINE_DASH_PX));
      backscreen.drawWideLine(x0, y0, x1, y1, 2, col);
    }
  }
}

// 自機アイコンを向けるべき画面上の角度 [度]（画面の上＝0、時計回り）。
// ESKF のヨーが信頼できるときだけ機首方位に合わせる。横風があるとトラックと機首は
// 偏流角のぶんずれるので、信頼できないヨーで回すと逆に誤解を招く。
// 信頼できないときは従来どおり対地進路（NORTHUP=ttrack、TRACKUP=画面上固定）。
static float plane_icon_screen_deg(int ttrack) {
  float y;
  if (!eskf_yaw_reliable() || !eskf_display_yaw(y))
    return is_trackupmode() ? 0.0f : (float)ttrack;
  return is_trackupmode() ? (y - (float)ttrack) : y;
}

// ヘッダー右の大きい枠が平均ピッチを出しているか（定義は draw_header の直前）。
static bool header_shows_pitch();

// TRACKUP 専用の半径縮小量 [px]。画面中央上部に "TT xxx" を出すようになり、
// 従来の半径（針の長さ nlen = 180）だと三角形の頂点が文字に届いてしまうため。
// STEER 側も一緒に縮めないと、内側へ寄った 30 度幅の三角形と誘導矢印が重なる。
#define TRACKUP_TONE_SHRINK   26
#define TRACKUP_STEER_SHRINK  24

void draw_triangle(int ttrack,float steer_angle) {
  // Core0 スタック残量を計測。
  // draw_triangle() は drawWideLine を最も多く呼ぶ関数であり、
  // TFT_eSPI の drawWideLine が大量のスタックを消費するため、
  // その直前がスタック消費のピーク（5 秒に 1 回出力）。
  DEBUG_STACK_C0("draw_triangle");
  float tt_radians = deg2rad(ttrack);
  const int nlen = get_needle_len();  // NORTHUP=120, TRACKUP=180
  if (upward_mode == MODE_NORTHUP) {
    // 最後のtrack音声が流れた時の、true track　方向を基準に、15度左・右・中央の3点を計算して三角形を描画する。
    // あくまでtrue trackの変化に気づくための表示であって、目標方位ではない。
    float tone_left = deg2rad(last_tone_tt-15);
    float tone_right = deg2rad(last_tone_tt+15);
    float tone_center = deg2rad(last_tone_tt);
    float x1 = (nlen-6) * sin(tone_left) + BACKSCREEN_SIZE/2;
    float y1 = (nlen-6) * -cos(tone_left) + BACKSCREEN_SIZE/2;
    float x2 = (nlen-6) * sin(tone_right) + BACKSCREEN_SIZE/2;
    float y2 = (nlen-6) * -cos(tone_right) + BACKSCREEN_SIZE/2;
    float x3 = (nlen) * sin(tone_center) + BACKSCREEN_SIZE/2;
    float y3 = (nlen) * -cos(tone_center) + BACKSCREEN_SIZE/2;
    if(trackwarning_until < millis()){
      backscreen.drawTriangle(x1,y1,x2,y2,x3,y3, COLOR_BLACK);
    }else{
      backscreen.fillTriangle(x1,y1,x2,y2,x3,y3, (millis()/1000)%2==0?COLOR_RED:COLOR_BLACK);
    }
    
    // 機体アイコン。NORTHUP は画面上＝北なので、そのまま方位を渡す。
    // ヨーが信頼できるときは機首方位、できないときは従来どおり ttrack で描かれる。
    draw_plane_icon(BACKSCREEN_SIZE / 2, BACKSCREEN_SIZE / 2,
                    plane_icon_screen_deg(ttrack), plane_icon_color());


    if((millis()/1000)%3 != 0){
      float arc_factor = course_warning_index/900.0;
      if(steer_angle > 0)
        backscreen.drawArc(240/2, 240/2, (nlen-21), (nlen-23), (ttrack+180)%360, (ttrack+180+(int)(arc_factor*steer_angle))%360, COLOR_RED, COLOR_WHITE);
      else
        backscreen.drawArc(240/2, 240/2, (nlen-21), (nlen-23), (ttrack+180+(int)(arc_factor*steer_angle))%360,(ttrack+180)%360, COLOR_RED, COLOR_WHITE);

      //約15度以上の方位違いがある場合に、指示三角形を描画する。
      if(abs(steer_angle) > 15){
        double steer_triangle_start_rad = tt_radians + (steer_angle<0?-0.1:0.1);
        double steer_triangle_end_rad = tt_radians + (steer_angle<0?-0.35:0.35);
        float x1 = (nlen-12) * sin(steer_triangle_start_rad) + 240/2;
        float y1 = (nlen-12) * -cos(steer_triangle_start_rad) + 240/2;
        float x2 = (nlen-32) * sin(steer_triangle_start_rad) + 240/2;
        float y2 = (nlen-32) * -cos(steer_triangle_start_rad) + 240/2;
        float x3 = (nlen-22) * sin(steer_triangle_end_rad) + 240/2;
        float y3 = (nlen-22) * -cos(steer_triangle_end_rad) + 240/2;
        backscreen.fillTriangle(x1,y1,x2,y2,x3,y3,COLOR_RED);
      }
      if(abs(steer_angle) > 55){
        double steer_triangle_start_rad = tt_radians + (steer_angle<0?-0.7:0.7);
        double steer_triangle_end_rad = tt_radians + (steer_angle<0?-0.95:0.95);
        float x1 = (nlen-12) * sin(steer_triangle_start_rad) + 240/2;
        float y1 = (nlen-12) * -cos(steer_triangle_start_rad) + 240/2;
        float x2 = (nlen-32) * sin(steer_triangle_start_rad) + 240/2;
        float y2 = (nlen-32) * -cos(steer_triangle_start_rad) + 240/2;
        float x3 = (nlen-22) * sin(steer_triangle_end_rad) + 240/2;
        float y3 = (nlen-22) * -cos(steer_triangle_end_rad) + 240/2;
        backscreen.fillTriangle(x1,y1,x2,y2,x3,y3,COLOR_RED);
      }
      if(abs(steer_angle) > 100){
        double steer_triangle_start_rad = tt_radians + (steer_angle<0?-1.3:1.3);
        double steer_triangle_end_rad = tt_radians + (steer_angle<0?-1.55:1.55);
        float x1 = (nlen-12) * sin(steer_triangle_start_rad) + 240/2;
        float y1 = (nlen-12) * -cos(steer_triangle_start_rad) + 240/2;
        float x2 = (nlen-32) * sin(steer_triangle_start_rad) + 240/2;
        float y2 = (nlen-32) * -cos(steer_triangle_start_rad) + 240/2;
        float x3 = (nlen-22) * sin(steer_triangle_end_rad) + 240/2;
        float y3 = (nlen-22) * -cos(steer_triangle_end_rad) + 240/2;
        backscreen.fillTriangle(x1,y1,x2,y2,x3,y3,COLOR_RED);
      }
    }
    
    // Needle (True Track)
    backscreen.drawWideLine(240/2+sin(tt_radians)*9, 240/2-cos(tt_radians)*9, 120+sin(tt_radians)*nlen, 120-cos(tt_radians)*nlen, 5,COLOR_BLACK);
    
  }
  if (upward_mode == MODE_TRACKUP) {
    // TRACKUP モードでは自機Y位置を画面下寄り（3/4）に表示する
    const int cy = BACKSCREEN_SIZE * 3 / 4;  // = 180（X は常に BACKSCREEN_SIZE/2 = 120）

    // ── 進行方向の縦線（常に画面上＝対地進路）──
    // TRACKUP では地図が回転して対地進路が常に画面上を向く。この線は進路そのものなので
    // 機首が振れても回さない（機首とのズレ＝偏流角がアイコンとの角度差で見える）。
    // 画面中央上部の "TT xxx"（NM_FONT_MEDIUM、高さ約24px）の下から始める。
    // ヘッダーがトラックを出しているときは中央の TT が無いので、その分だけ上へ伸ばせる。
    int shortening = header_shows_pitch() ? 28 : 16;
    backscreen.drawFastVLine(240 / 2,     shortening, cy - shortening - 5, COLOR_BLACK);
    backscreen.drawFastVLine(240 / 2 + 1, shortening, cy - shortening - 5, COLOR_BLACK);

    // ── 機体アイコン ──
    // ヨーが信頼できるときは (機首方位 - トラック) だけ傾けて実際の機首方向に合わせる。
    // 信頼できないときは 0（画面上向き）になり、従来の固定表示と同じになる。
    draw_plane_icon(BACKSCREEN_SIZE / 2, cy, plane_icon_screen_deg(ttrack), plane_icon_color());

    // ── True Track 維持針（last_tone_tt: 最後にトーンが鳴った時点のTT方向）──
    // TRACKUPでは機首=画面上=0°なので、last_tone_tt の画面上の角度は (last_tone_tt - ttrack)
    // 画面中央上部の "TT xxx" と重ならないよう、TRACKUP では半径を縮める
    const int tlen = nlen - TRACKUP_TONE_SHRINK;
    float screen_tone = last_tone_tt - ttrack;
    float tone_left   = deg2rad(screen_tone - 15);
    float tone_right  = deg2rad(screen_tone + 15);
    float tone_center = deg2rad(screen_tone);
    float tx1 = (tlen-6) * sin(tone_left)   + BACKSCREEN_SIZE/2;
    float ty1 = (tlen-6) * -cos(tone_left)  + cy;
    float tx2 = (tlen-6) * sin(tone_right)  + BACKSCREEN_SIZE/2;
    float ty2 = (tlen-6) * -cos(tone_right) + cy;
    float tx3 = tlen     * sin(tone_center) + BACKSCREEN_SIZE/2;
    float ty3 = tlen     * -cos(tone_center)+ cy;
    if (trackwarning_until < millis()) {
      backscreen.drawTriangle(tx1,ty1,tx2,ty2,tx3,ty3, COLOR_BLACK);
    } else {
      backscreen.fillTriangle(tx1,ty1,tx2,ty2,tx3,ty3, (millis()/1000)%2==0?COLOR_RED:COLOR_BLACK);
    }

    // ── コース逸脱アーク + 誘導三角形 ──
    // drawArcの座標系: 0°=6時方向（画面下）、時計回り。機首方向（画面上）= drawArc 180°
    // NORTHUPの (ttrack+180)%360 は方位角→drawArc角への変換。TRACKUPは機首固定なので 180 を使う。
    if ((millis()/1000)%3 != 0) {
      // 上で縮めた 30 度幅の三角形と重ならないよう、こちらも内側へ寄せる
      const int slen = nlen - TRACKUP_STEER_SHRINK;
      float arc_factor = course_warning_index / 900.0;
      if (steer_angle > 0)
        backscreen.drawArc(240/2, cy, (slen-21), (slen-23), 180, (180 + (int)(arc_factor*steer_angle)) % 360, COLOR_RED, COLOR_WHITE);
      else
        backscreen.drawArc(240/2, cy, (slen-21), (slen-23), (360 + 180 + (int)(arc_factor*steer_angle)) % 360, 180, COLOR_RED, COLOR_WHITE);

      // 誘導三角形: 機首=0ラジアン（画面上）を基準に offset。NORTHUPの tt_radians に相当
      if (abs(steer_angle) > 15) {
        double steer_triangle_start_rad = (steer_angle<0?-0.1:0.1);
        double steer_triangle_end_rad   = (steer_angle<0?-0.35:0.35);
        float x1 = (slen-12) * sin(steer_triangle_start_rad) + 240/2;
        float y1 = (slen-12) * -cos(steer_triangle_start_rad) + cy;
        float x2 = (slen-32) * sin(steer_triangle_start_rad) + 240/2;
        float y2 = (slen-32) * -cos(steer_triangle_start_rad) + cy;
        float x3 = (slen-22) * sin(steer_triangle_end_rad) + 240/2;
        float y3 = (slen-22) * -cos(steer_triangle_end_rad) + cy;
        backscreen.fillTriangle(x1,y1,x2,y2,x3,y3,COLOR_RED);
      }
      if (abs(steer_angle) > 55) {
        double steer_triangle_start_rad = (steer_angle<0?-0.7:0.7);
        double steer_triangle_end_rad   = (steer_angle<0?-0.95:0.95);
        float x1 = (slen-12) * sin(steer_triangle_start_rad) + 240/2;
        float y1 = (slen-12) * -cos(steer_triangle_start_rad) + cy;
        float x2 = (slen-32) * sin(steer_triangle_start_rad) + 240/2;
        float y2 = (slen-32) * -cos(steer_triangle_start_rad) + cy;
        float x3 = (slen-22) * sin(steer_triangle_end_rad) + 240/2;
        float y3 = (slen-22) * -cos(steer_triangle_end_rad) + cy;
        backscreen.fillTriangle(x1,y1,x2,y2,x3,y3,COLOR_RED);
      }
      if (abs(steer_angle) > 100) {
        double steer_triangle_start_rad = (steer_angle<0?-1.3:1.3);
        double steer_triangle_end_rad   = (steer_angle<0?-1.55:1.55);
        float x1 = (slen-12) * sin(steer_triangle_start_rad) + 240/2;
        float y1 = (slen-12) * -cos(steer_triangle_start_rad) + cy;
        float x2 = (slen-32) * sin(steer_triangle_start_rad) + 240/2;
        float y2 = (slen-32) * -cos(steer_triangle_start_rad) + cy;
        float x3 = (slen-22) * sin(steer_triangle_end_rad) + 240/2;
        float y3 = (slen-22) * -cos(steer_triangle_end_rad) + cy;
        backscreen.fillTriangle(x1,y1,x2,y2,x3,y3,COLOR_RED);
      }
    }
  }
}



// A→B 方向の B 側を distance km 延長した点 C を計算する（球面上の Vincenty 近似）。
// B で見た A→B の方位を反転させて（+PI）B 基準の正確な方向を求める。
// 目的地の「手前」や「飛び越した先」の座標計算に使用する。
void calculatePointC(double lat1, double lon1, double lat2, double lon2, double distance, double& lat3, double& lon3) {
  const double R = 6371.0;  // Radius of the Earth in kilometers
  lat1 = deg2rad(lat1);
  lon1 = deg2rad(lon1);
  lat2 = deg2rad(lat2);
  lon2 = deg2rad(lon2);

  double d = distance / R;  // Distance in radians
  //Note  PointA and PointB should be reversed and PI be added in order to accurately calculate angle at pointB since bearing is not the same at pointA and pointB if they are far apart.
  //And we want the bearing at pointB.
  double bearing = calculateTrueCourseRad(lat2, lon2,lat1, lon1)+PI;
  lat3 = asin(sin(lat2) * cos(d) + cos(lat2) * sin(d) * cos(bearing));
  lon3 = lon2 + atan2(sin(bearing) * sin(d) * cos(lat2), cos(d) - sin(lat2) * sin(lat3));

  lat3 = rad2deg(lat3);
  lon3 = rad2deg(lon3);

}


// A から A→B 方向へ distance km 進んだ点 D を計算する（calculatePointC とは始点が異なる）。
// A と B が同一点の場合は方位が未定義のためスキップする。
// 目的地が画面外にある場合に画面端付近の仮想点を計算し、矢印を描画するために使う。
void calculatePointD(double lat1, double lon1, double lat2, double lon2, double distance, double& lat3, double& lon3) {
  const double R = 6371.0;  // Radius of the Earth in kilometers
  lat1 = deg2rad(lat1);
  lon1 = deg2rad(lon1);
  lat2 = deg2rad(lat2);
  lon2 = deg2rad(lon2);

  double d = distance / R;  // Distance in radians

  if (lat1 == lat2 && lon1 == lon2) {
    // 方位が定義できない。**出力を必ず埋めてから返すこと。**
    // 以前は書かずに return していたので、呼び出し側が渡している未初期化の
    // ローカル変数がそのまま画面座標に化けた（現状この経路には入らないが、
    // 入った瞬間に誘導線が明後日へ飛ぶ形だった）。始点をそのまま返す。
    DEBUG_PLN(20250424,"Error: Points A and B are the same. Bearing is undefined.");
    lat3 = rad2deg(lat1);
    lon3 = rad2deg(lon1);
    return;
  }
  double bearing = calculateTrueCourseRad(lat1, lon1, lat2, lon2);

  lat3 = asin(sin(lat1) * cos(d) + cos(lat1) * sin(d) * cos(bearing));
  lon3 = lon1 + atan2(sin(bearing) * sin(d) * cos(lat1), cos(d) - sin(lat1) * sin(lat3));


  lat3 = rad2deg(lat3);
  lon3 = rad2deg(lon3);

}

// 始点 (lat1,lon1) から方位 bearing_rad（北基準・時計回り・ラジアン）へ
// distance km 進んだ点を計算する。calculatePointD の「方位を外から与える版」。
// 2 点から方位を求めるのではなく方位そのものを指定したい場合（センターライン等）に使う。
void calculatePointFromBearing(double lat1, double lon1, double bearing_rad, double distance, double& lat2, double& lon2) {
  const double R = 6371.0;  // Radius of the Earth in kilometers
  lat1 = deg2rad(lat1);
  lon1 = deg2rad(lon1);

  double d = distance / R;  // Distance in radians

  lat2 = asin(sin(lat1) * cos(d) + cos(lat1) * sin(d) * cos(bearing_rad));
  lon2 = lon1 + atan2(sin(bearing_rad) * sin(d) * cos(lat1), cos(d) - sin(lat1) * sin(lat2));

  lat2 = rad2deg(lat2);
  lon2 = rad2deg(lon2);
}

// FLYAWAY モード用の描画。目的地から「離れていく」方向への矢印を描く。
// 1. draw_flyinto() で目的地への基本矢印を描画する。
// 2. 目的地から「自機方向→その先」へのマゼンタ線を追加し、「飛び越した先」を示す。
void draw_flyawayfrom(double dest_lat,double dest_lon, double center_lat, double center_lon, float scale, float up) {
  draw_flyinto(dest_lat,dest_lon,center_lat,center_lon,scale,up,1);

  double lat3, lon3;
  double distance = 200 / scale;  //画面外に出ればよいので適当な距離を設定。
  calculatePointC(dest_lat, dest_lon, center_lat, center_lon, distance, lat3, lon3);
  cord_tft targetpoint = latLonToXY(lat3, lon3, center_lat, center_lon, scale, up);
  // 自機位置からtargetpoint（目的地と逆方向・画面外）へ太線を引く。
  // 細線は draw_flyinto() が目的地→自機間を描画済み。
  draw_clipped_wideline(BACKSCREEN_SIZE/2, get_self_cy(), targetpoint.x, targetpoint.y, 5, COLOR_MAGENTA);
}

// FLYINTO 拡張版。目的地が画面外の場合は仮想点を計算して矢印の終点に使う。
// 目的地が画面内の場合は目的地の「先」まで線を延長して通過線も描画する（draw_flyinto と異なる点）。
// 画面外オーバーフロー対策: goal の座標が int 範囲を超えると処理が重くなるため、
//   distance = 200/scale px 相当の仮想点を calculatePointD で求めて代替する。
void draw_flyinto2(double dest_lat, double dest_lon, double center_lat, double center_lon, float scale, float up,int thickness) {
  cord_tft goal = latLonToXY(dest_lat, dest_lon, center_lat, center_lon, scale, up);
  if (goal.isOutsideTft()) {
    //scaleがとても大きい場合、goal.x,goal.yがオーバーフローする。
    //そのまま描画すると処理落ちするので、適度な座標を計算し直す必要がある。
    double distance = 200 / scale;  //画面外に出ればよいので適当な距離を設定。
    double newlat, newlon;
    calculatePointD(center_lat, center_lon, dest_lat, dest_lon, distance, newlat, newlon);
    goal = latLonToXY(newlat, newlon, center_lat, center_lon, scale, up);
    draw_clipped_wideline(240 / 2, get_self_cy(), goal.x, goal.y, thickness, COLOR_MAGENTA);
  }else{
    draw_clipped_wideline(240 / 2, get_self_cy(), goal.x, goal.y, thickness, COLOR_MAGENTA);
    double distance = 200 / scale;  //画面外に出ればよいので適当な距離を設定。
    double newlat, newlon;
    //
    calculatePointC(dest_lat, dest_lon, center_lat, center_lon, -distance, newlat, newlon);
    cord_tft outside_tft = latLonToXY(newlat, newlon, center_lat, center_lon, scale, up);
    draw_clipped_wideline(goal.x, goal.y, outside_tft.x, outside_tft.y, 2, COLOR_MAGENTA);
  }
}

// 自機位置（画面中央）から目的地への誘導線（マゼンタの太線）を描画する。
// 目的地が画面外の場合: calculatePointD で画面端付近の仮想点を求めて矢印の向きを示す。
// thickness パラメータで線の太さを調整できる（通常 = 1、強調時 = 5）。
void draw_flyinto(double dest_lat, double dest_lon, double center_lat, double center_lon, float scale, float up,int thickness) {
  cord_tft goal = latLonToXY(dest_lat, dest_lon, center_lat, center_lon, scale, up);
  if (goal.isOutsideTft()) {
    //scaleがとても大きい場合、goal.x,goal.yがオーバーフローする。
    //そのまま描画すると処理落ちするので、適度な座標を計算し直す必要がある。
    double distance = 200 / scale;  //画面外に出ればよいので適当な距離を設定。
    double newlat, newlon;
    calculatePointD(center_lat, center_lon, dest_lat, dest_lon, distance, newlat, newlon);
    goal = latLonToXY(newlat, newlon, center_lat, center_lon, scale, up);
  }
  draw_clipped_wideline(240 / 2, get_self_cy(), goal.x, goal.y, thickness, COLOR_MAGENTA);
}


// LatLonManager（latlon_manager）に蓄積されたフライトトラックを backscreen に描画する。
// 最新座標（getData(0)）から自機位置（画面中央）への緑線を引き、
// その後 getData(i) → getData(i+1) を順に繋いでトラック履歴を表示する。
void draw_track(double center_lat, double center_lon, float scale, float up) {
  int sizetrack = latlon_manager.getCount();
  if(sizetrack <= 0){
    return;
  }
  //latest
  Coordinate c0 = latlon_manager.getData(0);
  cord_tft p0 = latLonToXY(c0.latitude, c0.longitude, center_lat, center_lon, scale, up);
  

  if(p0.x != BACKSCREEN_SIZE/2 || p0.y != get_self_cy()){
    draw_map_line(p0.x,p0.y,BACKSCREEN_SIZE/2,get_self_cy(),2,COLOR_GREEN);
  }

  // ★ 1 点につき 1 回だけ座標変換する。以前は getData(i) と getData(i+1) を
  //   毎回それぞれ変換していたので、各点が 2 回ずつ変換されていた。
  //   前回の変換結果を持ち回れば半分で済む。
  if(c0.latitude == 0 && c0.longitude == 0){
    DEBUGW_PLN(20250510,"ERR lat lon 0");
    return;
  }
  cord_tft prev = p0;
  for (int i = 0; i < sizetrack-1; i++) {
    Coordinate c1 = latlon_manager.getData(i+1);
    if(c1.latitude == 0 && c1.longitude == 0){
      DEBUGW_PLN(20250510,"ERR lat lon 0");
      break;
    }

    cord_tft cur = latLonToXY(c1.latitude, c1.longitude, center_lat, center_lon, scale, up);
    //Only if cordinates are different.
    if (prev.x != cur.x || prev.y != cur.y) {
      draw_map_line(prev.x,prev.y,cur.x,cur.y,2,COLOR_GREEN);
    }
    prev = cur;
  }
}


// ============================================================
//  受信モード：ボート自身の位置
// ============================================================
// ミラー中の地図は**機体**を中心に描くので、ボート自身は地図上に存在しない。
// 追走ボートにとっては「機体と自分がどれだけ離れているか」が一番知りたい情報なので、
// 自分の位置だけを小さな点として重ねる（docs/pons_link.md §5）。
//
//   ・3px の点。機体マーカーより明らかに小さくして、主役を取らないようにする
//   ・2m/s 以上で進んでいるときだけ進行方向へ短い線を伸ばす。
//     停船中の GNSS トラックは方位がでたらめなので、出すとかえって誤解を招く
//   ・色は明るい緑。飛行軌跡（濃い緑）と重なっても見分けられるようにする
void draw_own_position_marker(double center_lat, double center_lon, float scale, float up) {
  if (!link_mirror_active()) return;      // ミラーしていないなら自機＝画面中央なので不要

  double lat, lon, gs, track;
  if (!gnss_get_own_fix(lat, lon, gs, track)) return;

  cord_tft p = latLonToXY(lat, lon, center_lat, center_lon, scale, up);
  if (p.isOutsideTft()) return;           // 画面外。端に寄せて描くと位置を誤読させる

  if (gs >= OWNPOS_TRACK_MIN_MPS) {
    // 画面の上方向は up[deg]。地図と同じ回転をかける。
    const float rad = radians(track - up);
    const int ex = p.x + (int)lround(sinf(rad) * OWNPOS_TRACK_LEN_PX);
    const int ey = p.y - (int)lround(cosf(rad) * OWNPOS_TRACK_LEN_PX);
    backscreen.drawLine(p.x, p.y, ex, ey, COLOR_OWNPOS);
  }
  backscreen.fillCircle(p.x, p.y, OWNPOS_DOT_R, COLOR_OWNPOS);
}

// SD カードの mapdata.csv から読み込んだ追加ポリゴン（extramaps[]）を描画する。
// ポリゴンの最初の座標点が現在位置から 1°×1° 以内にある場合のみ描画する（遠方の不要描画を省略）。
// ポリゴンの描画色はマップ名の先頭文字で決まる:
//   r=赤, o=オレンジ, g=明るいグレー, m=マゼンタ, c=シアン, b=青, その他=緑
// 地図名の先頭 1 文字で描画色を決める。SD の mapdata.csv と内蔵ポリゴンで
// 同じ規則を使うため、ここに集約してある。
//   r=赤 / o=オレンジ / g=グレー / m=マゼンタ / c=シアン / b=青 / それ以外=緑
uint16_t mapdata_color(const char* name) {
  switch (name[0]) {
    case 'r': return COLOR_RED;
    case 'o': return COLOR_ORANGE;
    case 'g': return COLOR_BRIGHTGRAY;
    case 'm': return COLOR_MAGENTA;
    case 'c': return COLOR_CYAN;
    case 'b': return COLOR_BLUE;
    default:  return COLOR_GREEN;
  }
}

// フラッシュ内蔵のポリゴン地図（mapdatas[]）を描画する。
// SD の mapdata.csv 由来（draw_ExtraMaps）と同じ規則で描くが、
// こちらは SD が無くても・抜けても必ず表示される点が違う。
// 飛行に必須の注記はこちらに置くこと。
void draw_FlashMaps(double center_lat, double center_lon, float scale, float up) {
  for (int i = 0; i < flashmap_count; i++) {
    const mapdata* mp = flashmaps[i];
    if (mp->size <= 1) continue;
    // 現在地から離れた地図は描かない（extramaps と同じ 1 度四方の判定）
    if (!check_within_latlon(1, 1, mp->cords[0][1], get_gnss_lat(),
                             mp->cords[0][0], get_gnss_lon())) continue;
    draw_map(up, center_lat, center_lon, scale, mp, mapdata_color(mp->name));
  }
}

void draw_ExtraMaps(double center_lat, double center_lon, float scale, float up) {
  for (int i = 0; i < mapdata_count; i++) {
    if (extramaps[i].size <= 1) {
      continue;
    }
    double lon1 = extramaps[i].cords[0][0];
    double lat1 = extramaps[i].cords[0][1];
    if (check_within_latlon(1, 1, lat1, get_gnss_lat(), lon1, get_gnss_lon())) {
      int col = mapdata_color(extramaps[i].name);
      draw_map(up, center_lat, center_lon, scale, &extramaps[i], col);
        }
  }
}




// 起動アニメーションの地図背景。実際の地図と同じ描画関数を使う。
static void draw_startup_map(double lat, double lon, float scale) {
  draw_vectormap(lat, lon, scale, 0);
}

// backscreen の左下にソフトウェアバージョン文字列を、右上にバージョンテキストを描画する。
// 主に startup_demo_tft() のデモ画面で使用する。
void draw_version_backscreen(){
  // OpenStreetMap の帰属表示。ODbL 4.3 と OSMF Attribution Guidelines により、
  // 組み込みデバイスでも画面上への表示が必要（スプラッシュ画面での表示が認められている）。
  // 起動アニメーションの間ずっと表示されるので、この位置で要件を満たす。
  backscreen.unloadFont();
  backscreen.setTextColor(COLOR_GRAY);
  backscreen.setCursor(10, 240-34);
  backscreen.print("Map data (c) OpenStreetMap");
  backscreen.setCursor(10, 240-24);
  backscreen.print("contributors - ODbL 1.0");
  backscreen.setCursor(10, 240-12);
  backscreen.unloadFont();
  backscreen.setTextColor(COLOR_BLACK);
  backscreen.print("SOFTWARE:");
  backscreen.print(BUILDVERSION);
  backscreen.print("(Build ");
  backscreen.print(BUILDDATE);
  backscreen.print(")");

  backscreen.setCursor(160,0);
  backscreen.loadFont(AA_FONT_SMALL);
  backscreen.println(VERSION_TEXT);
}

// Arduino の map() 関数の float 版。x を [in_min, in_max] から [out_min, out_max] に線形変換する。
// startup_demo_tft() のアニメーション（スケール・座標の補間）に使用する。
float mapf(float x, float in_min, float in_max, float out_min, float out_max){
  return (x - in_min) * (out_max - out_min) / (in_max - in_min) + out_min;
}

// 起動時のスプラッシュアニメーションを表示する。
// 1. ロゴ BMP を SD から読み込んで表示。SD 状態を画面下部に表示。
// 2. 琵琶湖マップをズームイン（遠→近）しながら PLA 位置に移動するアニメーション（約 40 フレーム）。
// 3. 続いてズームアウト（近→遠）しながら日本地図へ引くアニメーション。
// mapf() で中心座標とスケールを線形補間してスムーズなアニメーションを実現している。
// 起動直後のタイトル。**setup_tft() の直後と startup_demo_tft() の頭の両方から呼ぶ。**
// ★ ここを setup() の早い段階で出さないと、起動画面が始まるまで**画面が真っ白**になる。
//   その間に何をしているかというと imu_setup()（BNO085 のリセット〜ブートで約 0.4 秒）と
//   gnss_setup() で、後者が支配的。GNSS が繋がっていないと CFG の ACK 待ちが
//   5 コマンドぶん空振りして **約 3.7 秒**かかる（log.txt の "GNSS CFG NO ACK"）。
//   GNSS が繋がっていれば ACK が即返るので、ここは 1 秒以下に縮む。
void draw_boot_title() {
  tft.fillScreen(COLOR_WHITE);
  tft.setTextColor(COLOR_RED, COLOR_WHITE);
  tft.setCursor(1, 0);
  tft.println(" Pilot Oriented");
  tft.setCursor(5, 14);
  tft.println("   Navigation System  for HPA");
  // 下段は draw_boot_diag() が上書きする。それまでの間の「生きている」表示。
  tft.setTextColor(COLOR_GRAY, COLOR_WHITE);
  tft.setCursor(10, SCREEN_HEIGHT - 28);
  tft.print("INITIALIZING SENSORS ...");   // 画面幅に収まる長さで
  tft.setTextColor(COLOR_BLACK, COLOR_WHITE);
}

// draw_boot_progress() の1項目分を描く。PENDING はグレーで "..." のまま。
static void print_boot_check(const char* label, BootCheckState st) {
  tft.setTextColor(st == BOOT_CHECK_PENDING ? COLOR_GRAY :
                    (st == BOOT_CHECK_OK ? COLOR_GREEN : COLOR_RED), COLOR_WHITE);
  tft.print(label);
  tft.print(st == BOOT_CHECK_PENDING ? "..." : (st == BOOT_CHECK_OK ? "OK" : "NG"));
}

// setup() の間、センサーの初期化が終わった順に呼ぶ（draw_boot_title() の下段を上書きする）。
// ★ GNSS の行は draw_boot_diag(0) が SD の情報で上書きするので、ここだけの一時的な表示でよい。
//   MS5611/BNO085 の行は draw_boot_diag(0) と同じ文言・同じ位置にしてあるので、
//   最終表示に切り替わっても見た目が変わらない（チラつきが無い）。
void draw_boot_progress(BootCheckState imu, BootCheckState airdata, BootCheckState gnss) {
  const int16_t y1 = SCREEN_HEIGHT - 28;   // 292
  const int16_t y2 = SCREEN_HEIGHT - 16;   // 304
  tft.fillRect(0, y1, SCREEN_WIDTH, 28, COLOR_WHITE);

  tft.setCursor(20, y1);
  print_boot_check("GNSS:", gnss);

  tft.setCursor(10, y2);
  print_boot_check("MS5611:", airdata);
  tft.setTextColor(COLOR_BLACK, COLOR_WHITE);
  tft.print("  ");
  print_boot_check("BNO085:", imu);
  tft.setTextColor(COLOR_BLACK, COLOR_WHITE);
}

// 起動画面フッターの自己診断表示。**画面下端 28px（y=292〜319）だけが使える。**
// この少し下で backscreen(240x240) を y=52 に push するので、それより上へ書いても
// 毎フレーム塗り潰される。
// ★ AA フォント(NotoSansBold15)は 1 行 15px なので、この帯には **2 行しか入らない**。
//   4 項目を 1 画面に詰めるには内蔵フォント(6x8)へ落とすしかないが、実機で
//   小さすぎて読めなかった。**アニメーションが長い（約 8 秒）ことを利用して
//   前半・後半の 2 ページに分ける。**
//   phase 0 = ストレージとセンサー / phase 1 = 無線。
static void draw_boot_diag(uint8_t phase) {
  const int16_t y1 = SCREEN_HEIGHT - 28;   // 292
  const int16_t y2 = SCREEN_HEIGHT - 16;   // 304
  tft.fillRect(0, y1, SCREEN_WIDTH, 28, COLOR_WHITE);   // 前のページを消す

  if (phase == 0) {
    tft.setCursor(20, y1);
    if (good_sd()) {
      tft.setTextColor(COLOR_GREEN, COLOR_WHITE);
      tft.print("SD OK! MAP COUNT: ");
      tft.print(mapdata_count);
    } else {
      tft.setTextColor(COLOR_RED, COLOR_WHITE);
      tft.print("[ERROR: CHECK SD CARD !]");
    }
    tft.setCursor(10, y2);
    tft.setTextColor(get_airdata_ok() ? COLOR_GREEN : COLOR_RED, COLOR_WHITE);
    tft.print(get_airdata_ok() ? "MS5611:OK" : "MS5611:NG");
    tft.setTextColor(COLOR_BLACK, COLOR_WHITE);
    tft.print("  ");
    tft.setTextColor(get_imu_ok() ? COLOR_GREEN : COLOR_RED, COLOR_WHITE);
    tft.print(get_imu_ok() ? "BNO085:OK" : "BNO085:NG");
    return;
  }

  // ---- 無線（E220）----
  // ★ **「設定で OFF」と「応答しない」を色で区別する。** OFF は故障ではないので
  //   赤にしない。一緒にすると「無線を切ったまま飛ぶ」のと「無線が壊れている」が
  //   見分けられなくなる。
  // ★ CH / SF / GROUP も出す。設定を間違えて別チャンネル・別グループに送っていても
  //   飛行中の画面には何も出ないので、**飛ぶ前に目で確かめられる場所がここしかない**
  //   （docs/pons_link.md §1）。
  const uint8_t m = link_get_mode();
  tft.setCursor(10, y1);
  if (m == LINK_MODE_OFF) {
    tft.setTextColor(COLOR_GRAY, COLOR_WHITE);
    tft.print("E220:--  LINK OFF");
  } else if (link_module_alive()) {
    tft.setTextColor(COLOR_GREEN, COLOR_WHITE);
    tft.printf("E220:OK  %s CH%u SF%u",
               (m == LINK_MODE_TX) ? "TX" : "RX",
               link_get_radio_ch(), e220_profile_to_sf(link_get_radio_profile()));
    tft.setTextColor(COLOR_BLACK, COLOR_WHITE);
    tft.setCursor(10, y2);
    tft.printf("LINK GROUP: %u", link_get_group());
  } else {
    tft.setTextColor(COLOR_RED, COLOR_WHITE);
    tft.print("E220:NG  NO RESPONSE");
    tft.setCursor(10, y2);
    tft.print("[CHECK RADIO MODULE !]");
  }
  tft.setTextColor(COLOR_BLACK, COLOR_WHITE);
}

void startup_demo_tft() {
  draw_boot_title();

  
  // Core1 の setup_sd() が完了するまで待機（最大5秒）。
  // Core1 が SD を初期化中に Core0 が SD にアクセスすると SDIO バス競合でフリーズする。
  {
    unsigned long t = millis();
    while (!sd_setup_complete && millis() - t < 5000) {
      gnss_loop(7);       // 待機中も GNSS FIFO を読み捨てて overflow 防止
      imu_service_if_due();  // ★ BNO085 も引き取る。**これが無いと起動直後に殺す**
                             //   （imu_update() の途絶判定は 1 秒。CLAUDE.md 参照）
      delay(10);
    }
  }


  // 起動音。ロゴも音声も FLASH に持っているので、SD からの読み込み依頼は不要。
  enqueueTask(createPlayWavTask("wav/opening.wav"));

  // ★ **SD 異常の警告ビープは起動音とは別に鳴らす。消さないこと。**
  //   0.982 まではこれが「SD が無いときの起動音の代替」だったので、
  //   音声を FLASH へ移したときに if の else ごと消すと **SD の故障に音で
  //   気づく手段が 1 つも無くなる**（画面の赤字だけになり、起動画面を
  //   見ていなければ気づけない。飛行ログが 1 本も残らないまま飛ぶことになる）。
  //   通常トーン（solo_play=false）なので起動音の**あとではなく重なって**鳴る。
  //   それでよい。500Hz の連続ビープはオープニングの音色と紛れないし、
  //   solo_play にすると起動音そのものを潰してしまう。
  if (!good_sd()) {
    enqueueTask(createPlayMultiToneTask(500, 150, 10));    // SD エラー: 警告ビープ（500Hz を 10 回）
  }

  draw_boot_diag(0);      // 前半ページ: SD / MS5611 / BNO085
  float center_lat = 35.2334225841915;
  float center_lon = 136.091056306493;

  // 起動アニメーションは自機表示なし。TRACKUP 時の get_self_cy()=180 が適用されると
  // 地図が 60px 下にずれるため、アニメーション全体を強制的に NORTHUP 基準で描画する。
  // ※ここより前で sd_setup_complete 待ちが完了しているため upward_mode は SD 読み込み済みの値。
  int saved_upward_mode = upward_mode;
  upward_mode = MODE_NORTHUP;

  backscreen.fillScreen(COLOR_WHITE);
  draw_startup_map(center_lat, center_lon, 2.5);
  draw_pilon_takeshima_line(center_lat, center_lon, 2.5, 0);
  draw_pilon_takeshima_marks(center_lat, center_lon, 2.5, 0);
  draw_version_backscreen();
  backscreen.pushSprite(0,52);


  // ★ ロゴは FLASH に持つようになった（logo_data.h）。
  //   以前は Core1 が SD の logo.bmp を読み終えるのを最大 1.9 秒待っていたが、
  //   もう待つ必要が無い。SD が読めない機体でもロゴが出るし、
  //   logo_sprite（240x52 = 24KB の RAM）も要らなくなった。
  //   起動演出の尺は保ちたいので、待ち時間はそのまま消費する。
  {
    // pushImage()（pushPixels 経由）は既定で色バイトを入れ替えて送る。
    // LOGO_DATA は素の RGB565 値（旧 SD 版の drawPixel と同じ並び）なので、
    // 既定のままだと二重に入れ替わってカラフルなモザイクになる。ここだけ true にして戻す。
    tft.setSwapBytes(true);
    tft.pushImage(0, 0, LOGO_W, LOGO_H, LOGO_DATA);
    tft.setSwapBytes(false);
    backscreen.pushSprite(0, 52);  // ロゴ下の琵琶湖地図を復元
    const int wait_timeout_ms = 1900;
    unsigned long wait_start = millis();
    while (millis() - wait_start < wait_timeout_ms) {
      gnss_loop(7);       // 待機中も GNSS FIFO を読み捨てて overflow 防止
      imu_service_if_due();  // ★ BNO085 も引き取る。**これが無いと起動直後に殺す**
                             //   （imu_update() の途絶判定は 1 秒。CLAUDE.md 参照）
      delay(10);
    }
  }

  float zoomin_speedfactor = 1.0f;
  int countermax = 40/zoomin_speedfactor;
  float scalenow = 0;
  for (int i = 0; i <= countermax; i++) {
    backscreen.fillScreen(COLOR_WHITE);
    scalenow = 2.5 + i * 0.25*zoomin_speedfactor;
    draw_startup_map(mapf(i,0,countermax,center_lat,pla_lat), mapf(i,0,countermax,center_lon,pla_lon), scalenow);
    draw_pilon_takeshima_line(mapf(i,0,countermax,center_lat,pla_lat), mapf(i,0,countermax,center_lon,pla_lon), scalenow, 0);
    draw_pilon_takeshima_marks(mapf(i,0,countermax,center_lat,pla_lat), mapf(i,0,countermax,center_lon,pla_lon), scalenow, 0);
    draw_version_backscreen();
    backscreen.pushSprite(0,52);
  }
  delay(10);

  // ★ ここでフッターを後半ページへ切り替える。アニメーションの折り返し地点なので、
  //   前半（ロゴ 1.9 秒 + ズームイン）と後半（ズームアウト + 帰属表示 3.5 秒）が
  //   だいたい同じ長さになり、どちらも読む時間がある。
  draw_boot_diag(1);      // 後半ページ: E220（無線）

  float zoomout_speedfactor = 1.0f;
  countermax = 40/zoomout_speedfactor;

  for (int i = 0; i < countermax; i++) {
    //scalenow *= 0.78;//for zoomout_speedfactor=2. 
    scalenow *= 0.89;// for zoomout_speedfactor=1
    if(scalenow < 0.08)
      scalenow = 0.08;
    else{
      center_lat += 0.005*i;// for zoomout_speedfactor=1
      //center_lat += 0.01*i;// for zoomout_speedfactor=2
    }

    backscreen.fillScreen(COLOR_WHITE);
    {
      draw_startup_map(mapf(i,0,countermax,pla_lat,center_lat), mapf(i,0,countermax,pla_lon,center_lon), scalenow);
      draw_pilon_takeshima_line(mapf(i,0,countermax,pla_lat,center_lat), mapf(i,0,countermax,pla_lon,center_lon), scalenow, 0);
      draw_pilon_takeshima_marks(mapf(i,0,countermax,pla_lat,center_lat), mapf(i,0,countermax,pla_lon,center_lon), scalenow, 0);
    }
    draw_version_backscreen();
    backscreen.pushSprite(0,52);
  }

  // OpenStreetMap の帰属表示（draw_version_backscreen が描いている）を
  // 読める時間だけ残す。OSMF の Attribution Guidelines はスプラッシュ画面での
  // 表示を認めているが、一瞬で消えると「easily readable」の要件を満たさない。
  // 最終フレームは既に表示済みなので、そのまま 2 秒保持する。
  {
    const unsigned long hold_ms = 3500;
    unsigned long t0 = millis();
    while (millis() - t0 < hold_ms) {
      gnss_loop(7);       // 待機中も GNSS FIFO を読み捨てて overflow 防止
      imu_service_if_due();  // ★ BNO085 も引き取る。**これが無いと起動直後に殺す**
                             //   （imu_update() の途絶判定は 1 秒。CLAUDE.md 参照）
      delay(10);
    }
  }

  upward_mode = saved_upward_mode;  // TRACKUP/NORTHUP 設定を復元
}
// デモ飛行中の通知ボックスを backscreen に描画する。
// 選択中の地点名を出すので、どの地点を表示しているか画面で分かる。
void draw_demo_biwako(){
  if((millis()/3000)%2 == 0){  // 6秒周期（3秒点灯・3秒消灯）で点滅
    backscreen.fillRect(5, 195, SCREEN_WIDTH-5*2, 15+5*2, COLOR_WHITE);
    backscreen.drawRect(5, 195, SCREEN_WIDTH-5*2, 15+5*2, COLOR_ORANGE);
    backscreen.setCursor(25,200);
    backscreen.setTextColor(COLOR_ORANGE);
    backscreen.print("DEMO: ");
    backscreen.print(get_demo_site_name(get_demo_site()));
  }
}


// リプレイモード中であることを backscreen に赤枠付きで通知する。
// draw_demo_biwako と同スタイル。画面上部に配置して常に視認できるようにする。
void draw_replay_indicator(){
  if((millis()/1000)%2 == 0){
    backscreen.fillRect(5, 195, SCREEN_WIDTH-5*2, 20, COLOR_WHITE);
    backscreen.drawRect(5, 195, SCREEN_WIDTH-5*2, 20, COLOR_RED);
    backscreen.drawRect(6, 196, SCREEN_WIDTH-5*2-2, 18, COLOR_RED);
    backscreen.setTextColor(COLOR_RED);
    backscreen.loadFont(AA_FONT_SMALL);
    // ★ 受信ログ（received/）の再生は **自機ではなく機体の飛行**なので区別する。
    //   ファイル名の頭を見るだけで判定できるので、状態変数を増やさない。
    static const char kRxPrefix[] = REPLAY_RECEIVED_DIR "/";
    const char* fn = get_replay_filename();
    const bool rx = (strncmp(fn, kRxPrefix, sizeof(kRxPrefix) - 1) == 0);
    backscreen.setCursor(rx ? 84 : 95, 199);
    backscreen.print(rx ? "REPLAY RX" : "REPLAY");
  }
}

// backscreen スプライトを白でクリアする（毎フレームの描画前に呼ぶ）。
// VSIスプライト（5×240px）を鉛直速度に応じて描画する。
// 中心 Y=120 が 0 m/s の基準線（白）。上昇=緑バー、下降=シアンバー。
// 不感域なし。最大バー長 120px（±1.5 m/s で振り切り）。
// バーの上にグレー線（バリオ閾値 KF:±0.3 / MS5611単独:±0.6 m/s）と白線（±0.5 m/s, ±1.0 m/s）を重ねて描画。
void draw_vsi() {
    // ★ 供給元の判断は imu.cpp の vario_* に集約してある（音と同じものを見る）。
    //   ここに `get_imu_ok()` / `get_airdata_ok()` を書き戻さないこと。
    //   ミラー中は送信機の V/S をそのまま出す（自機のセンサーの有無は無関係）。
    float vspeed = vario_vspeed_mps();
    vsi_sprite.fillScreen(TFT_BLACK);
    vsi_sprite.drawFastHLine(0, 120, VSI_W, TFT_WHITE);  // 0 m/s 基準線
    if (!vario_source_ok()) return;
    const float MAX_VSPEED = 1.5f;
    const int   BAR_MAX_PX = 120;
    if (vspeed > 0) {
        // 上昇: 中心から上方向に緑バー（1.5 m/s で振り切り）
        int bar = (int)(min(vspeed, MAX_VSPEED) / MAX_VSPEED * BAR_MAX_PX);
        vsi_sprite.fillRect(0, 120 - bar, VSI_W, bar, TFT_GREEN);
    } else if (vspeed < 0) {
        // 下降: 中心から下方向にシアンバー（1.5 m/s で振り切り）
        int bar = (int)(min(-vspeed, MAX_VSPEED) / MAX_VSPEED * BAR_MAX_PX);
        vsi_sprite.fillRect(0, 121, VSI_W, bar, TFT_CYAN);
    }
    // 閾値ラインをバーの上に重ねて描画（バーがなくても常に表示）
    // グレー線: バリオ音デッドバンド閾値。**選び方ごと** vario_deadband_mps() に
    // 預けてあるので、音（sound.cpp）と線が構造的にずれない
    // （0.983 まで定数は共有していたが「どちらを選ぶか」の判定式が別々だった）。
    //   KF融合中(BNO085+MS5611): ±0.25 m/s = ±20px / MS5611単独: ±0.60 m/s = ±48px
    const float db_mps = vario_deadband_mps();
    const int db_px = (int)(db_mps / MAX_VSPEED * BAR_MAX_PX + 0.5f);
    vsi_sprite.drawFastHLine(0, 120 - db_px, VSI_W, TFT_DARKGREY);
    vsi_sprite.drawFastHLine(0, 120 + db_px, VSI_W, TFT_DARKGREY);
    // 白線: ±0.5 m/s = ±40px, ±1.0 m/s = ±80px  (v/1.5*120)
    vsi_sprite.drawFastHLine(0, 120 - 40, VSI_W, TFT_WHITE);     // +0.5 m/s
    vsi_sprite.drawFastHLine(0, 120 + 40, VSI_W, TFT_WHITE);     // -0.5 m/s
    vsi_sprite.drawFastHLine(0, 120 - 80, VSI_W, TFT_WHITE);     // +1.0 m/s
    vsi_sprite.drawFastHLine(0, 120 + 80, VSI_W, TFT_WHITE);     // -1.0 m/s
}

// backscreen スプライトを TFT の (0, 50) に転送する（ヘッダー 50px の下から表示）。
// 転送前に VSI を backscreen の右端 X=VSI_X に合成する。
// ============================================================
// draw_eskf_attitude(): 地図上に姿勢を 3 行で重ねる
// ============================================================
// 背景は敷かず地図へ直接上書きする。リプレイ中は姿勢ログがある日のみ。
// 位置は左下。最下行(JST 時刻)のすぐ上を最下段とし、下から上へ
// Rtrim → R → P → 風/Y95 と積む。
// 平均ピッチはヘッダー右の大きい枠へ移した（同じ情報を 2 か所に出さない）。
// DEBUG_ESKF の有無でこの位置と大きさを変えないこと。
//
//   Avg**s P : 平均ピッチ。大きい字（NM_FONT_MEDIUM）＝一番見るべき値。
//   P / R    : 瞬時値。参考なので小さい字（AA_FONT_SMALL）。
//
// ロールは BANK_WARN_DEG を超えたら赤にする（バンク超過の気付き用）。
// 左端に寄せてあるのは、TRACKUP のとき自機アイコン（cy=180）の真下に
// draw_eskf_yaw() のヨー数値が入るため、中央付近を空けておく必要があるから。
// 自動ロールトリムの累積補正量の表示色。
// 正しく取り付いていれば実測上ほぼ 0 のままなので、大きな累積は
// 「取り付けか機体に異常があり、バンク警報の基準がずれている」ことを意味する。
// 表示は 8px と小さいが、色なら周辺視野でも気づける。
static uint16_t roll_trim_color(float trim) {
  const float a = fabsf(trim);
  if (a >= ROLL_TRIM_ALERT_DEG) return COLOR_RED;
  if (a >= ROLL_TRIM_WARN_DEG)  return COLOR_ORANGE;
  return COLOR_GRAY;
}

// 姿勢の値が「ありえない」範囲か（設置ミス・較正忘れの疑い）。
// true のとき数値を灰色にして、機体の姿勢としては信用できないことを示す。
static inline bool attitude_implausible(float deg) {
  return fabsf(deg) >= ATTITUDE_IMPLAUSIBLE_DEG;
}

// 風速に応じた矢印の色。しきい値は settings.h。
static uint16_t wind_arrow_color(float mps) {
  if (mps <= WIND_COL_LOW_MAX) return COLOR_GREEN;        // 濃い緑
  if (mps <= WIND_COL_MID_MAX) return COLOR_WIND_PURPLE;    // 青
  return COLOR_RED;                               // 紫
}


// 風ベクトルの矢印を (cx,cy) を中心に描き、その回転中心に風向を数字で重ねる。
// 長さは固定で、強さは色で表す。
// screen_deg: 画面の上を 0 とした時計回りの角度。前方は (+sin, -cos)。
// dir_to_deg: 風の真方位（attitude_get_wind() の「吹いていく向き」をそのまま渡す）。
// 矢印は「風が吹いていく向き」を指す。**中心の数字はその逆**で、気象通報と同じ
// 「吹いてくる向き」（南西の風なら 230）。矢印と数字が 180 度逆を向くのは意図通り。
static void draw_wind_arrow(int cx, int cy, float screen_deg, uint16_t col, float dir_to_deg) {
  const float a = deg2rad(screen_deg);
  const float ca = cosf(a), sa = sinf(a);
  const int h = WIND_ARROW_LEN_PX / 2;
  const int tipx  = cx + (int)lroundf(sa * h),  tipy  = cy - (int)lroundf(ca * h);
  const int tailx = cx - (int)lroundf(sa * h),  taily = cy + (int)lroundf(ca * h);

  // 中心に置く数字。フォントと色は draw_eskf_yaw() の機首方位に合わせる
  // （並べて読むものなので、大きさや色が違うと別の意味の値に見える）。
  char buf[8];
  snprintf(buf, sizeof(buf), "%03d", ((int)lroundf(dir_to_deg + 180.0f) % 360 + 360) % 360);
  backscreen.loadFont(AA_FONT_SMALL);
  const int tw = backscreen.textWidth(buf), th = backscreen.fontHeight();

  // 矢じりの底辺の中心。先端から WIND_ARROW_HEAD_PX 手前。
  const int hw = WIND_ARROW_HEAD_PX;
  const int bx = cx + (int)lroundf(sa * (h - hw)), by = cy - (int)lroundf(ca * (h - hw));

  // 軸は数字の手前で切る。切る長さは「幅 tw・高さ th の文字箱が矢印の向きへ
  // どれだけ張り出すか」= (tw/2)|sin| + (th/2)|cos|。こうしておくと横向きの
  // 矢印でも軸が数字を突き抜けない。
  const int gap = (int)lroundf(fabsf(sa) * tw * 0.5f + fabsf(ca) * th * 0.5f) + 2;
  const int gx = (int)lroundf(sa * gap), gy = (int)lroundf(ca * gap);
  if (gap < h)      backscreen.drawWideLine(tailx, taily, cx - gx, cy + gy, WIND_ARROW_WIDTH_PX, col);
  // ★ 先端側は tip ではなく**矢じりの底辺 (bx,by) まで**。
  //   drawWideLine は端が半径 WIND_ARROW_WIDTH_PX/2 の丸（TFT_eSPI.cpp: "rounded ends"）で、
  //   tip まで引くとその丸が頂点から 2px はみ出し、**先端が三角形でなく瘤になる**
  //   （矢じりを後から描いても、はみ出した分は三角形の外なので消えない）。
  //   数字が底辺より外まで来る角度（横向き）では、そもそも描く軸が無い。
  //   残りが軸の太さに満たないときも描かない。**丸い端だけが底辺の外へ出て、
  //   矢じりが欠けたように見える**（真下向きに近い角度で目立つ）。
  if (h - hw - gap >= WIND_ARROW_WIDTH_PX)
    backscreen.drawWideLine(cx + gx, cy - gy, bx, by, WIND_ARROW_WIDTH_PX, col);

  // 矢じり。底辺の半幅は矢じり長の 0.55 倍。
  const int px = (int)lroundf(ca * hw * 0.55f), py = (int)lroundf(sa * hw * 0.55f);
  backscreen.fillTriangle(tipx, tipy, bx + px, by + py, bx - px, by - py, col);

  // 数字は軸・矢じりより後に描く（万一重なっても数字が読める側に残す）。
  backscreen.setTextColor(COLOR_BLACK);
  backscreen.setCursor(cx - tw / 2, cy - th / 2);
  backscreen.print(buf);
}

#define ESKF_LABEL_X        2
#define ESKF_VALUE_RIGHT_X  50    // P / R の値の右端（ここへ右揃え。桁が揃う）
#define ESKF_ROW_GAP        1     // 各行の隙間 [px]
// 最下段(Rtrim, 内蔵フォント8px)の下端から最下行(JST 時刻)までの余白 [px]。
// sAcc と MaxGS を他所へ移して空いたので、ブロック全体を下へ寄せてある。
#define ESKF_BOTTOM_GAP     2
void draw_eskf_attitude() {
  // 機能そのものが OFF なら何も出さない（ESKF 導入前と同じ見た目に戻す）。
  if (!attitude_get_rpy_enabled()) return;

  // 機能は ON なのに姿勢が出せない状態。何も描かないと「表示が壊れた」のか
  // 「まだ準備中」なのか区別できないので、理由だけ 1 行出す。
  // 屋外で GNSS 速度が入れば 0.5 秒ほどで READY になるので、通常は一瞬しか見えない。
  // BNO085 非搭載機は姿勢機能自体が無いので対象外（出しっぱなしになってしまう）。
  // ★ **ミラー中は出さない。** ここで言う「準備中」は *この装置の ESKF* の話で、
  //   画面に出しているのは機体の姿勢なので関係が無い。しかも return しているため、
  //   **受信機自身の ESKF が READY になるまでミラーした姿勢ブロックが丸ごと
  //   出なくなる**（P / R / Y95 / 風 / Rtrim の全部）。
  if (!getReplayMode() && !link_mirror_active() && get_imu_ok() && !attitude_ready()) {
    backscreen.setTextWrap(false);
    backscreen.loadFont(AA_FONT_SMALL);
    const int fh = backscreen.fontHeight();
    backscreen.setTextColor(COLOR_ORANGE);
    backscreen.setCursor(ESKF_LABEL_X,
                         BACKSCREEN_SIZE - 9 - 8 - ESKF_BOTTOM_GAP - fh - ESKF_ROW_GAP);
    backscreen.print("ESKF Not ready");
    backscreen.setTextColor(COLOR_BLACK);
    return;
  }

  if (!eskf_display_enabled()) return;  // リプレイで姿勢ログが無い日

  float r, p, y = 0.0f;
  if (link_mirror_active()) {
    if (!link_get_attitude(r, p)) return;    // 受信データに姿勢が載っていない
  } else if (getReplayMode()) {
    if (!get_replay_attitude(r, p)) return;  // その日の姿勢ログが無い
  } else {
    attitude_get_euler(r, p, y);
  }

  char rbuf[8], pbuf[8];
  snprintf(rbuf, sizeof(rbuf), "%+5.1f", r);
  snprintf(pbuf, sizeof(pbuf), "%+5.1f", p);

  // 平均ピッチだけを NM_FONT_MEDIUM の大きい字にする。
  // 瞬時ピッチは周期 2〜6.7 秒の振動が主で std 1.23 度あり操縦の指標にならない。
  // 平均なら std 0.37 度まで落ちて 1 度の変化が有意に読める（窓長は PITCH_AVG_SEC）。
  // 瞬時の P / R は参考値なので AA_FONT_SMALL に落とす。
  // リプレイでは実機（机の上）の平均ではなく、記録された当時の値を出す。
  backscreen.setTextWrap(false);
  backscreen.loadFont(AA_FONT_SMALL);
  const int fh_s = backscreen.fontHeight();

  // 下から積む。最下段は Rtrim（内蔵フォント 8px）で、その下は JST 時刻の行。
  const int yrtrim = BACKSCREEN_SIZE - 9 - 8 - ESKF_BOTTOM_GAP;
  const int yroll  = yrtrim - fh_s - ESKF_ROW_GAP;                 // ロール
  const int ypit   = yroll  - fh_s - ESKF_ROW_GAP;                 // ピッチ

  // ---- P の上: ヨー精度（常時）と風ベクトル ----
  // 風は「対気速度の向き＝機首方位」を前提にするので、ヨーが著しく信頼できて、かつ
  // 直進が累計 WIND_LPF_SEC 秒たまるまで出ない。出ていない間も理由が分かるよう
  // ヨー精度の 95% 値は常に出す（風が出ているときも隠さない）。
  // リプレイでは記録された値をそのまま出す。
  {
    const int yacc95 = ypit - ESKF_ROW_GAP - fh_s;   // ヨー精度の行（P のすぐ上）

    float wspd = 0.0f, wdir = 0.0f;
    float acc95 = 0.0f;
    bool  has_wind, has_acc;
    has_acc = eskf_display_yaw_acc(acc95);
    // ★ **ヨー信頼性のゲートは 3 経路すべてに掛けること。**
    //   風は「対気速度の向き＝機首方位」を前提にしているので、ヨーが信用できない区間の
    //   値は原理的に当てにならない。以前はこのゲートが自機の経路にしか無く、
    //   **機体の画面が隠している風をボートの画面が出していた**（ミラー中）。
    //   リプレイも同じで、「その時に画面へ出ていた値を再現する」という
    //   imu_replaydata/ の建て付けと食い違っていた。
    //   判定に使う yaw_acc95 は SD ログにもダウンリンクにも入っているので
    //   （eskf_display_yaw_acc() が 3 系統とも面倒を見る）、どの経路でも
    //   **当時と同じ条件を復元できる**。記録・送信そのものは止めない（後から解析したいため）。
    if (is_demo_active()) {
      // デモは表示確認用。実機の推定条件（直進 10 秒など）を待たずに矢印を出す。
      has_wind = attitude_get_wind_enabled() && demo_wind(wspd, wdir);
    } else if (!eskf_yaw_high_confidence()) {
      has_wind = false;                        // ヨーが信用できない ＝ 風も信用できない
    } else if (link_mirror_active()) {
      has_wind = link_get_wind(wspd, wdir);
    } else if (getReplayMode()) {
      has_wind = get_replay_wind(wspd, wdir);
    } else {
      has_wind = attitude_get_wind_enabled() && attitude_get_wind(wspd, wdir);
    }

    // σ はフォント(NotoSansBold15)に無いので "Y95" と書く。意味は 95% 値（=2σ）。
    if (has_acc) {
      backscreen.setTextColor(COLOR_GRAY);
      backscreen.setCursor(ESKF_LABEL_X, yacc95);
      backscreen.printf("Y95%%%.0f\xC2\xB0", acc95);
    }

    int yblock_top = yacc95;
    if (has_wind) {
      // 数値だけ NM_FONT_MEDIUM。Arial_Black22 は数字と +-. しか持たないので、
      // "W" と "m/s" は AA_FONT_SMALL のまま描いて数字だけ大きくする。
      char nbuf[8];
      snprintf(nbuf, sizeof(nbuf), "%.1f", wspd);
      const int wlw = backscreen.textWidth("W");
      backscreen.loadFont(NM_FONT_MEDIUM);
      const int fh_m = backscreen.fontHeight();
      const int nw   = backscreen.textWidth(nbuf);
      const int ywtxt = yacc95 - ESKF_ROW_GAP - fh_m;
      const int ylbl  = ywtxt + (fh_m - fh_s) / 2;   // 小文字は数値の高さの中央へ
      backscreen.setTextColor(COLOR_BLACK);
      backscreen.setCursor(ESKF_LABEL_X + wlw + 3, ywtxt);
      backscreen.print(nbuf);
      backscreen.loadFont(AA_FONT_SMALL);
      backscreen.setCursor(ESKF_LABEL_X, ylbl);
      backscreen.print("W");
      backscreen.setCursor(ESKF_LABEL_X + wlw + 3 + nw + 2, ylbl);
      backscreen.print("m/s");

      // 矢印は地図と同じ向き合わせ（TRACKUP は画面上＝トラック、NORTHUP は北）
      const float wscreen = is_trackupmode()
                            ? (wdir - (float)get_gnss_truetrack()) : wdir;
      // 中心の数字は真方位なので、地図の向き（wscreen）とは別に wdir をそのまま渡す。
      draw_wind_arrow(ESKF_LABEL_X + WIND_ARROW_LEN_PX / 2 + 2,
                      ywtxt - ESKF_ROW_GAP - WIND_ARROW_LEN_PX / 2,
                      wscreen, wind_arrow_color(wspd), wdir);
      yblock_top = ywtxt - ESKF_ROW_GAP - WIND_ARROW_LEN_PX;
    }

    // ---- 較正のやり直しが必要（マウントから外された形跡がある）----
    // この状態では表示している姿勢そのものが信用できないので、設定画面まで
    // 行かないと分からないのでは遅い。地図上でも赤字で出す。
    // ★ 判定は eskf_display_needs_apply()（供給元 3 系統を見る）。リプレイ中は
    //   出さず、ミラー中は**送信機の**状態を出す。ここに attitude_needs_apply() を
    //   直接書かないこと。出している姿勢と警告の対象が食い違う。
    // ★ 点滅させる（3 秒のうち 1 秒だけ出す）。
    //   対処できるのは地上だけなので、音は地上でしか鳴らさない（.ino 参照）。
    //   そのぶん、万一この状態で飛んでしまったときに地図を隠し続けないよう、
    //   表示のほうは消えている時間を長めに取る。
    if (eskf_display_needs_apply() && (millis() / 1000) % 3 == 0) {
      backscreen.setTextColor(COLOR_RED);
      backscreen.setCursor(ESKF_LABEL_X, yblock_top - ESKF_ROW_GAP - fh_s);
      backscreen.print("ESKF CALIBRATION REQUIRED!");
      backscreen.setTextColor(COLOR_BLACK);
    }
  }

  // ---- 中段: P ----
  // ピッチは色を変えない。ピッチ単独では失速余裕を判定できないため
  // （本来は迎角が要る。実測でも 平均ピッチと対気速度の相関は -0.14 と弱く、
  //   迎角推定も対地経路角の 平均がほぼゼロで補正にならなかった）。
  backscreen.setTextColor(COLOR_GRAY);
  backscreen.setCursor(ESKF_LABEL_X, ypit);
  backscreen.print("P");
  backscreen.setTextColor(attitude_implausible(p) ? COLOR_GRAY : COLOR_BLACK);
  backscreen.setCursor(ESKF_VALUE_RIGHT_X - backscreen.textWidth(pbuf), ypit);
  backscreen.print(pbuf);

  // ---- 最下段: R ----
  backscreen.setTextColor(COLOR_GRAY);
  backscreen.setCursor(ESKF_LABEL_X, yroll);
  backscreen.print("R");
  // ありえない値なら灰色（設置ミスの疑い）。それ以外はバンク超過だけ赤。
  // 地図の上に直接描くので通常色は黒（フッターと同じ）。
  backscreen.setTextColor(attitude_implausible(r) ? COLOR_GRAY
                          : (fabsf(r) > BANK_WARN_DEG ? COLOR_RED : COLOR_BLACK));
  backscreen.setCursor(ESKF_VALUE_RIGHT_X - backscreen.textWidth(rbuf), yroll);
  backscreen.print(rbuf);
  backscreen.setTextColor(COLOR_BLACK);

  // ---- R の下: 自動ロールトリムの累積補正量（内蔵フォント 8px = 最小）----
  // どれだけ自動補正が入っているかを飛行中にも確認できるようにする。
  // リプレイでは記録された当時の値を出す（旧 euler 形式には無いので非表示）。
  float trim_val = 0.0f;
  bool  show_trim;
  if (link_mirror_active())    show_trim = link_get_roll_trim(trim_val);
  else if (getReplayMode())    show_trim = get_replay_roll_trim(trim_val);
  else { show_trim = true; trim_val = attitude_get_roll_trim_deg(); }
  if (show_trim) {
    backscreen.unloadFont();
    backscreen.setTextSize(1);
    backscreen.setTextColor(roll_trim_color(trim_val));
    backscreen.setCursor(ESKF_LABEL_X, yrtrim);
    backscreen.printf("Rtrim%+.2f", trim_val);
    backscreen.setTextColor(COLOR_BLACK);
  }

  // この後に描く コース警告 / [GS] [m/s] [MT] と同じフォントで抜けること。
  backscreen.loadFont(AA_FONT_SMALL);
}


// ============================================================
// draw_eskf_yaw(): 自機アイコンのすぐ下に ESKF のヨー角（真方位）を描く
// ============================================================
// フォントは [GS] [m/s] [MT] と同じ AA_FONT_SMALL。
// 色で信頼度を表す:
//   黒     = 信頼できる（95%値 < ESKF_YAW_TRUST_95_DEG）。このときアイコンも機首方向へ回る。
//   グレー = 信頼できない。アイコンは回らず対地進路（トラック）向きのまま。
// ロール・ピッチ行より後に呼ぶこと（TRACKUP では真下がその行に近いため）。
void draw_eskf_yaw() {
  if (!eskf_display_enabled()) return;

  // 旧 euler 形式のヨーは BNO085 由来で、実測で真方位から -30〜-65 度ずれていた。
  // 当時これを機首方位として表示していないので、リプレイでも再現しない
  // （eskf_display_yaw() が新形式のときだけ true を返す）。
  float y;
  if (!eskf_display_yaw(y)) return;

  char buf[8];
  snprintf(buf, sizeof(buf), "%03d", ((int)lroundf(y) % 360 + 360) % 360);

  backscreen.loadFont(AA_FONT_SMALL);
  backscreen.setTextWrap(false);
  backscreen.setTextColor(eskf_yaw_reliable() ? COLOR_BLACK : COLOR_GRAY);
  // アイコン（尾翼の下端は cy+TRIANGLE_SIZE/2）のすぐ下に中央揃えで置く
  backscreen.setCursor(BACKSCREEN_SIZE / 2 - backscreen.textWidth(buf) / 2,
                       get_self_cy() + TRIANGLE_SIZE / 2 + 3);
  backscreen.print(buf);
  backscreen.setTextColor(COLOR_BLACK);
}


#ifdef DEBUG_ESKF
// ============================================================
// draw_eskf_debug(): 比較用の詳細表示（DEBUG_ESKF 有効時のみ）
// ============================================================
// 姿勢推定の精度を実機で見比べるための評価用。地図上部に被せる。
// draw_eskf_attitude() が使う左下の領域には触れないこと。
//
// 見方: 旋回中・加減速中に ESKF と BNO085 が開いていれば、その差が BNO085 の誤差。
//   BNO085 は比力を鉛直とみなすため、定常旋回でロールを過小評価し、加減速でピッチがずれる。
// ヨーは σ（推定標準偏差）で信頼度を示す。水平加速度が無いと可観測にならず育つ。
void draw_eskf_debug() {
  const int x = 0, y = 2, w = 240, h = 46;

  backscreen.unloadFont();
  backscreen.fillRect(x, y, w, h, COLOR_BLACK);
  backscreen.drawRect(x, y, w, h, COLOR_GRAY);

  if (!attitude_ready()) {
    backscreen.setTextSize(2);
    backscreen.setTextColor(COLOR_YELLOW, COLOR_BLACK);
    backscreen.setCursor(x + 6, y + 6);
    backscreen.print("ESKF INIT...");
    backscreen.setTextSize(1);
    backscreen.setTextColor(COLOR_BRIGHTGRAY, COLOR_BLACK);
    backscreen.setCursor(x + 6, y + 28);
    backscreen.printf("static %.1fs / need %.1fs  %s",
                      attitude_get_static_secs(),
                      ESKF_STATIC_INIT_US / 1000000.0f,
                      attitude_is_static() ? "hold still" : "waiting");
    backscreen.loadFont(AA_FONT_SMALL);  // 内蔵フォントのまま抜けない
    return;
  }

  float er, ep, ey;  attitude_get_euler(er, ep, ey);
  float br, bp, by;  get_imu_euler(br, bp, by);
  float yacc = attitude_get_yaw_acc95_deg();   // 95%(2σ) 表記

  // 見出し
  backscreen.setTextSize(1);
  backscreen.setTextColor(COLOR_GRAY, COLOR_BLACK);
  backscreen.setCursor(x + 44,  y + 2); backscreen.print("ROLL");
  backscreen.setCursor(x + 110, y + 2); backscreen.print("PITCH");
  backscreen.setCursor(x + 182, y + 2); backscreen.print("YAW");

  // ESKF（ヨーだけ信頼度で色を変える。ロール・ピッチと同確度だと誤解させないため）
  backscreen.setTextColor(COLOR_CYAN, COLOR_BLACK);
  backscreen.setCursor(x + 2, y + 14); backscreen.print("ESKF");
  backscreen.setTextSize(2);
  backscreen.setTextColor(COLOR_WHITE, COLOR_BLACK);
  backscreen.setCursor(x + 36,  y + 12); backscreen.printf("%+5.1f", er);
  backscreen.setCursor(x + 108, y + 12); backscreen.printf("%+5.1f", ep);
  backscreen.setTextColor(yacc < 10.0f ? COLOR_WHITE
                        : yacc < 40.0f ? COLOR_YELLOW : COLOR_GRAY, COLOR_BLACK);
  backscreen.setCursor(x + 186, y + 12); backscreen.printf("%4.0f", ey);

  // チップ内融合（比較用）。★ **これが無いチップもある**（SCH16T）。
  //   無いときに 0 を並べると「水平で北向き」という本物らしい値になるので、
  //   行ごと "---" にする。ヨーの収束状態（右の G/数値）は ESKF の話なので常に出す。
  backscreen.setTextSize(1);
  backscreen.setTextColor(COLOR_ORANGE, COLOR_BLACK);
  backscreen.setCursor(x + 2, y + 32); backscreen.print(imu_sensor_name());
  backscreen.setTextColor(COLOR_BRIGHTGRAY, COLOR_BLACK);
  if (imu_caps() & IMU_CAP_QUAT) {
    backscreen.setCursor(x + 36,  y + 32); backscreen.printf("%+6.1f", br);
    backscreen.setCursor(x + 108, y + 32); backscreen.printf("%+6.1f", bp);
    backscreen.setCursor(x + 186, y + 32); backscreen.printf("%4.0f", by);
  } else {
    backscreen.setCursor(x + 36,  y + 32); backscreen.print("   ---");
    backscreen.setCursor(x + 108, y + 32); backscreen.print("   ---");
    backscreen.setCursor(x + 186, y + 32); backscreen.print(" ---");
  }

  // ヨーの収束状態: M=地磁気で初期化済み / -=収束待ち、数値は 95%(2σ) の精度 [度]
  backscreen.setTextColor(COLOR_GRAY, COLOR_BLACK);
  backscreen.setCursor(x + 142, y + 32);
  // ヨーの情報源。'G' = GNSS 航跡から入れた / '-' = まだ入っていない（絶対方位は無意味）
  backscreen.printf("%c%3.0f",
                    (attitude_get_yaw_source() == ATT_YAW_SRC_GNSS) ? 'G' : '-', yacc);

  backscreen.setTextSize(1);
  // 内蔵フォントのまま抜けると以降の描画が崩れるので必ず戻す（draw_eskf_attitude と同様）
  backscreen.loadFont(AA_FONT_SMALL);
}
#endif // DEBUG_ESKF


// ============================================================
// IMU / 姿勢 ESKF 画面（2 ページ構成）
// ============================================================
// ページ1: 姿勢の比較と、機体ゼロ点の較正操作
// ページ2: センサーの生値・ESKF の内部状態（診断用）
//
// 操作: 短押し = カーソル移動 / 長押し = 実行（Exit 項目で設定画面へ戻る）
// 他の設定画面と同じ操作系に揃えてある。
extern int imu_cursor;   // GPS_TFT_map.ino で定義。ページ1のカーソル位置


// タイトル右端の状態ドット。緑になる条件は次の 3 つを全て満たすとき。
//   ・バンク警告が ON
//   ・自動ロールトリムが ON
//   ・自動トリムの累積が小さい（ROLL_TRIM_WARN_DEG 未満）
// 3 つ目を入れているのは、累積が大きい＝取り付けがずれていて
// バンク警報の基準が信用できない状態だから。飛行前点検で気づけるようにする。
// 右上の状態ドットが緑になる条件を 1 か所にまとめる。
// 各メニュー行の丸もここを参照するので、条件と表示が食い違わない。
//   緑になるのは次の 3 つを全て満たすとき:
//     1. ESKF が収束している（READY）        … ページ1の ESKF 行 / ページ2の READY 行
//     2. Roll/Pitch/Yaw func が ON          … ページ1
//     3. Roll trim during flight が ON      … ページ2
//     4. 自動トリムの累積が ROLL_TRIM_WARN_DEG 未満  … ページ1の Rtrim 表示
// 1 は「まだ姿勢が出せていない」状態なので、これを緑にすると準備完了と誤解する。
static bool imu_ok_ready() { return attitude_ready(); }
static bool imu_ok_rpy()   { return attitude_get_rpy_enabled(); }
static bool imu_ok_trim()  { return attitude_get_roll_trim_enabled(); }
static bool imu_ok_rtrim() { return fabsf(attitude_get_roll_trim_deg()) < ROLL_TRIM_WARN_DEG; }

// メニュー行の右端に状態の丸を描く（行の縦中央）。x は全行で揃える。
static void draw_imu_row_dot(int y, uint16_t col) {
  backscreen.fillCircle(232, y + 7, 4, col);
}
static uint16_t imu_row_col(bool ok) { return ok ? COLOR_GREEN : COLOR_ORANGE; }

static void draw_imu_status_dot() {
  // BNO085 非搭載機。姿勢機能そのものが無いので緑（＝準備OK）にはしない。
  if (!get_imu_ok()) { header_footer.fillCircle(228, 18, 6, COLOR_GRAY); return; }
  // マウントから外されたあと APPLY していない＝較正が無効。これだけは赤にする。
  // 姿勢の基準そのものが失われている状態で、他の設定の良し悪しより深刻なため。
  if (attitude_needs_apply() && attitude_get_rpy_enabled()) {
    header_footer.fillCircle(228, 18, 6, COLOR_RED);
    return;
  }
  const bool ok = imu_ok_ready() && imu_ok_rpy() && imu_ok_trim() && imu_ok_rtrim();
  header_footer.fillCircle(228, 18, 6, ok ? COLOR_GREEN : COLOR_ORANGE);
}

static void draw_imu_page1() {
  header_footer.fillScreen(COLOR_WHITE);
  header_footer.setTextColor(COLOR_BLACK, COLOR_WHITE);
  header_footer.setTextSize(2);
  header_footer.setCursor(1, 11);
  header_footer.print("IMU / ESKF  1/3");
  draw_imu_status_dot();
  header_footer.pushSprite(0, -10);

  backscreen.fillScreen(COLOR_WHITE);
  backscreen.loadFont(AA_FONT_SMALL);
  backscreen.setTextWrap(false);   // 長い項目名が 2 行に折り返さないように

  int y = 2;
  const int lh = 12;
  bool ready = attitude_ready();

  // ---- 姿勢の比較 ----
  // ★ **列は固定 x から描く。** AA_FONT_SMALL はプロポーショナルなので、
  //   空白で詰めても桁は揃わない（"ESKF" と "BNO085" で幅が違う）。
  //   チップ名が可変長になった 0.984 で、空白詰めでは成立しなくなった。
  const int cx_r = 56, cx_p = 112, cx_y = 168;   // ロール / ピッチ / ヨーの左端
  backscreen.setTextColor(COLOR_GRAY, COLOR_WHITE);
  backscreen.setCursor(cx_r, y);  backscreen.print("ROLL");
  backscreen.setCursor(cx_p, y);  backscreen.print("PITCH");
  backscreen.setCursor(cx_y, y);  backscreen.print("YAW");
  y += lh;
  float er, ep, ey, br, bp, by;
  attitude_get_euler(er, ep, ey);
  get_imu_euler(br, bp, by);
  backscreen.setTextColor(COLOR_BLUE, COLOR_WHITE);
  backscreen.setCursor(2, y); backscreen.print("ESKF");
  // 未初期化・IMU 途絶時は数値を出さない（単位クォータニオンのままだと
  // pitch=-90 というもっともらしい値が出て有効値と誤読される）
  if (ready) {
    backscreen.setCursor(cx_r, y); backscreen.printf("%+6.1f", er);
    backscreen.setCursor(cx_p, y); backscreen.printf("%+6.1f", ep);
    backscreen.setCursor(cx_y, y); backscreen.printf("%6.1f", ey);
  } else {
    backscreen.setCursor(cx_r, y); backscreen.print("  ---");
    backscreen.setCursor(cx_p, y); backscreen.print("  ---");
    backscreen.setCursor(cx_y, y); backscreen.print("  ---");
  }
  draw_imu_row_dot(y - 2, imu_row_col(imu_ok_ready()));
  y += lh;
  backscreen.setTextColor(COLOR_ORANGE, COLOR_WHITE);
  backscreen.setCursor(2, y); backscreen.print(imu_sensor_name());
  if (imu_caps() & IMU_CAP_QUAT) {
    backscreen.setCursor(cx_r, y); backscreen.printf("%+6.1f", br);
    backscreen.setCursor(cx_p, y); backscreen.printf("%+6.1f", bp);
    backscreen.setCursor(cx_y, y); backscreen.printf("%6.1f", by);
  } else {
    // 融合出力を持たないチップ（SCH16T）。0 を出すと「水平で北向き」に見える。
    backscreen.setCursor(cx_r, y); backscreen.print("  ---");
    backscreen.setCursor(cx_p, y); backscreen.print("  ---");
    backscreen.setCursor(cx_y, y); backscreen.print("  ---");
  }
  y += lh;
  // 巡航のトリム状態は瞬時ピッチではなく 平均で見る（瞬時値は std 1.23 度の振動があるため）。
  // 直進中のロール自動トリムの累積量も併記して、どれだけ補正が入ったか分かるようにする。
  backscreen.setTextColor(COLOR_GRAY, COLOR_WHITE);
  backscreen.setCursor(2, y);
  if (attitude_pitch_avg_valid())
    backscreen.printf("P avg%.0fs %+5.1f  ", PITCH_AVG_SEC, attitude_get_pitch_avg_deg());
  else
    backscreen.printf("P avg%.0fs   --    ", PITCH_AVG_SEC);
  // Rtrim は緑条件の 3 つ目。しきい値を超えていることが分かるよう色を変える。
  backscreen.setTextColor(imu_ok_rtrim() ? COLOR_GRAY : COLOR_ORANGE, COLOR_WHITE);
  backscreen.printf("Rtrim %+.2f", attitude_get_roll_trim_deg());
  draw_imu_row_dot(y - 2, imu_row_col(imu_ok_rtrim()));
  y += lh + 6;

  // ---- 注意書き ----
  // 色で意味を分ける。赤は「異常＝対処が要る」、青は「操作前に確認すること」。
  // Note: 〜 を赤にしていたが、エラーが起きているように見えるので青にした。
  backscreen.setCursor(2, y);
  if (attitude_needs_apply() && attitude_get_rpy_enabled()) {
    backscreen.setTextColor(COLOR_RED, COLOR_WHITE);
    // マウントから外された形跡がある。較正をやり直すまで姿勢は信用できない。
    backscreen.print("!! REMOVED FROM MOUNT"); y += lh;
    backscreen.setCursor(2, y);
    backscreen.print("   APPLY required"); y += lh + 6;
  } else if (attitude_get_rpy_enabled() && !getReplayMode() &&
             attitude_calib_date_stale(get_gnss_jst_yyyymmdd())) {
    // 較正した日と今日（JST）が違う。電源が切れている間に外して付け直していても
    // OFF MOUNT 判定は働かないので、日付だけを手がかりに注意を促す。
    // ★ 赤にしない。付けっぱなしで日をまたいだだけのことも十分あり、
    //   その場合は較正は正しい。断定しない色（オレンジ）で出す。
    //   発報（音）は .ino 側で地上のとき一度だけ。ここは表示のみ。
    // ★ リプレイ中は出さない。リプレイ中の ubx_* は再生している CSV の日付に
    //   なるので、そのまま比べると必ず「日付が違う」になってしまう
    //   （音のほうは、外側の地上判定に !getReplayMode() が入っているので届かない）。
    const uint32_t cd = attitude_get_calib_date();
    backscreen.setTextColor(COLOR_ORANGE, COLOR_WHITE);
    backscreen.printf("! CALIB IS FROM %02u/%02u",
                      (unsigned)(cd / 100 % 100), (unsigned)(cd % 100)); y += lh;
    backscreen.setCursor(2, y);
    backscreen.print("  APPLY again if remounted"); y += lh + 6;
  } else {
    backscreen.setTextColor(COLOR_BLUE, COLOR_WHITE);
    backscreen.print("Note: Make sure actual aircraft"); y += lh;
    backscreen.setCursor(2, y);
    backscreen.print("  attitude matches SET attitude"); y += lh + 6;
  }

  // ---- 操作メニュー ----
  // 項目数 6。8 項目のときは 15 まで詰めていたが、2 ページ目へ移して余裕ができた。
  const int mh = 17;
  bool on_ground = eskf_calib_allowed();
  for (int i = 0; i < IMU_MENU_COUNT; i++) {
    bool sel = (imu_cursor == i);
    backscreen.setCursor(2, y);
    backscreen.setTextColor(sel ? COLOR_MAGENTA : COLOR_BLACK, COLOR_WHITE);
    backscreen.print(sel ? ">" : " ");
    backscreen.setCursor(14, y);
    switch (i) {
      case IMU_MENU_SETPITCH:
        backscreen.printf("SET PITCH = %+.1f deg", attitude_get_pitch_target());
        break;
      case IMU_MENU_SETROLL:
        // 通常は 0。0 以外は「傾けたまま較正する」宣言なので目立たせる。
        // 0 以外は「傾けたまま較正する」宣言なので、カーソル位置でなくても目立たせる
        if (!sel && attitude_get_roll_target() != 0.0f)
          backscreen.setTextColor(COLOR_ORANGE, COLOR_WHITE);
        backscreen.printf("SET ROLL  = %+.1f deg", attitude_get_roll_target());
        break;
      case IMU_MENU_APPLY:
        // 実行可否をそのまま出す。飛行中は通さない。
        if (attitude_calib_pending())
                             backscreen.print("APPLY  ... hold still");
        else if (!ready)     backscreen.print("APPLY  (ESKF not ready)");
        else if (!on_ground) backscreen.print((getReplayMode() || is_demo_active())
                                              ? "APPLY  (hold still)" : "APPLY  (moving)");
        else                 backscreen.print("APPLY above=calibrate now");
        // 較正が必要なときは赤丸。画面右上の赤丸だけでは「何をすれば消えるのか」が
        // 分からないので、対処すべき項目に同じ色の印を並べて対応付ける。
        if (attitude_needs_apply() && attitude_get_rpy_enabled())
          draw_imu_row_dot(y, COLOR_RED);
        break;
      case IMU_MENU_RPYFUNC:
        // 姿勢表示・各種警報・自動トリム・風推定・姿勢ログを一括で ON/OFF する
        backscreen.printf("Roll/Pitch/Yaw func: %s",
                          attitude_get_rpy_enabled() ? "ON " : "OFF");
        draw_imu_row_dot(y, imu_row_col(imu_ok_rpy()));
        break;
      case IMU_MENU_NEXTPAGE:
        backscreen.print("Next page (BNO085) >");
        // 2/3・3/3 で見る項目の状態をここに集約して見せる。
        // 緑にならない原因が先のページにあるとき、1/3 だけ見ても分かるようにする。
        draw_imu_row_dot(y, imu_row_col(imu_ok_trim() && imu_ok_ready()));
        break;
      case IMU_MENU_EXIT:     backscreen.print("Exit >>");              break;
    }
    y += mh;
  }

  // ---- 現在保存されているオフセット ----
  y += 4;
  float lr, lp;
  attitude_get_level_offset(lr, lp);
  backscreen.setTextColor(COLOR_GRAY, COLOR_WHITE);
  backscreen.setCursor(2, y);
  backscreen.printf("stored offset  R%+.1f  P%+.1f", lr, lp);

  backscreen.unloadFont();
  backscreen.pushSprite(0, 40);
}


// ページ2: センサー生値と ESKF 内部状態（診断用）
// 校正の申告精度（0-3）の色。3=収束 / 2=まだ / それ以下は当てにならない。
static uint16_t cal_acc_col(uint8_t v) {
  return (v >= 3) ? COLOR_GREEN : (v == 2) ? COLOR_ORANGE : COLOR_RED;
}

// ============================================================
//  IMU / ESKF 2/3 — BNO085 の生値と校正だけ
// ============================================================
// ★ ここに ESKF の項目を戻さないこと。校正作業をしながら見る画面なので、
//   「BNO085 が今どう見えているか」だけに絞ってある（ESKF は 3/3）。
static void draw_imu_page2() {
  header_footer.fillScreen(COLOR_WHITE);
  header_footer.setTextColor(COLOR_BLACK, COLOR_WHITE);
  header_footer.setTextSize(2);
  header_footer.setCursor(1, 11);
  header_footer.print("IMU / ESKF  2/3");
  draw_imu_status_dot();
  header_footer.pushSprite(0, -10);

  backscreen.fillScreen(COLOR_WHITE);
  backscreen.loadFont(AA_FONT_SMALL);
  backscreen.setTextColor(COLOR_BLACK, COLOR_WHITE);

  int y = 2;
  const int lh = 12;
  const float R2D = 180.0f / (float)M_PI;
  float g[3], a[3];
  get_imu_raw_gyro(g);
  get_imu_raw_accel(a);
  const float gn = sqrtf(g[0]*g[0]+g[1]*g[1]+g[2]*g[2]) * R2D;
  const float an = sqrtf(a[0]*a[0]+a[1]*a[1]+a[2]*a[2]);

  backscreen.setTextColor(COLOR_GRAY, COLOR_WHITE);
  backscreen.setCursor(2, y); backscreen.print("-- Gyro raw [deg/s] --"); y += lh;
  backscreen.setTextColor(COLOR_BLACK, COLOR_WHITE);
  backscreen.setCursor(2, y);
  backscreen.printf("X%+7.3f Y%+7.3f Z%+7.3f", g[0]*R2D, g[1]*R2D, g[2]*R2D); y += lh;
  backscreen.setCursor(2, y);
  // 静止中ならこの大きさが残留バイアス＋ノイズ。BNO085 は校正済みなので本来小さい。
  backscreen.setTextColor(gn < 0.5f ? COLOR_GREEN : COLOR_ORANGE, COLOR_WHITE);
  backscreen.printf("|w| %.3f deg/s", gn); y += lh;

  backscreen.setTextColor(COLOR_GRAY, COLOR_WHITE);
  backscreen.setCursor(2, y); backscreen.print("-- Accel raw [m/s2] --"); y += lh;
  backscreen.setTextColor(COLOR_BLACK, COLOR_WHITE);
  backscreen.setCursor(2, y);
  backscreen.printf("X%+7.3f Y%+7.3f Z%+7.3f", a[0], a[1], a[2]); y += lh;
  // ★★ **|a| が校正の合否そのもの。** 静止していれば姿勢に関係なく必ず 9.807。
  //   申告精度(acc)が 3 でもここがずれていることがあるので、**数字を信じるのはこちら**。
  //   2026-09-27 に実機で |a|=8.22（X 軸に +1.31 m/s^2 のバイアス）を踏んだ。
  //   姿勢を変えながらこの値が動かないことを確かめるのが確実な判定。
  const float aerr = an - 9.80665f;
  backscreen.setCursor(2, y);
  backscreen.setTextColor(fabsf(aerr) < 0.10f ? COLOR_GREEN
                        : fabsf(aerr) < 0.30f ? COLOR_ORANGE : COLOR_RED, COLOR_WHITE);
  backscreen.printf("|a| %.3f  err%+.2f  (g=9.807)", an, aerr); y += lh + 2;

  const bool st = attitude_is_static();
  backscreen.setTextColor(st ? COLOR_GREEN : COLOR_GRAY, COLOR_WHITE);
  backscreen.setCursor(2, y);
  backscreen.printf("STATIC: %s  %.1fs", st ? "YES" : "no ", attitude_get_static_secs());
  y += lh + 2;

  // ---- 校正（DCD）----
  backscreen.setTextColor(COLOR_GRAY, COLOR_WHITE);
  // ★ 動的校正（DCD）と申告精度は BNO085 固有。SCH16T は工場校正で、
  //   実行中に精度を申告する仕組みが無い。**節だけ差し替えて、下のメニューと
  //   pushSprite には必ず到達すること**（early return にするとページが真っ白になり、
  //   Next page / Back も押せなくなる）。
  const bool has_cal = (imu_caps() & IMU_CAP_CAL) != 0;
  backscreen.setCursor(2, y);
  backscreen.print(has_cal ? "-- Calibration --" : "-- Calibration (n/a) --");
  y += lh;
  if (has_cal) {
    // BNO085 の申告精度。**加速度は 6 姿勢（各軸の上下）で静止させると上がる。**
    //   くるくる回すのは地磁気向けだが、**M: は 0.984 で消した**（地磁気レポートの
    //   購読をやめたので更新されない。真方位しか使わないので購読そのものが不要）。
    const uint8_t ca = get_imu_acc_accuracy(), cg = get_imu_gyr_accuracy();
    backscreen.setCursor(2, y);
    backscreen.setTextColor(COLOR_BLACK, COLOR_WHITE);  backscreen.print("Cal ");
    backscreen.setTextColor(cal_acc_col(ca), COLOR_WHITE); backscreen.printf("A:%u ", ca);
    backscreen.setTextColor(cal_acc_col(cg), COLOR_WHITE); backscreen.printf("G:%u", cg);
    backscreen.setTextColor(COLOR_GRAY, COLOR_WHITE);
    backscreen.printf("  cfg:%02X", get_imu_cal_cfg());
    y += lh;

    // ★★ **「一度も保存していない」を赤で明示する。** この画面を作った目的そのもの。
    //   記録は本体フラッシュ（EEPROM 領域）にあり、SD を入れ替えても嘘にならない。
    //   日付が --/-- なのは GNSS 時刻が無い場所（屋内）で保存したとき。RTC は無い。
    const uint32_t sd_ = imu_cal_saved_date();
    backscreen.setCursor(2, y);
    if (!imu_cal_saved_ever()) {
      backscreen.setTextColor(COLOR_RED, COLOR_WHITE);
      backscreen.print("DCD: NEVER SAVED");
    } else if (sd_) {
      backscreen.setTextColor(COLOR_GREEN, COLOR_WHITE);
      backscreen.printf("DCD: SAVED %04u/%02u/%02u", (unsigned)(sd_ / 10000),
                        (unsigned)(sd_ / 100 % 100), (unsigned)(sd_ % 100));
    } else {
      backscreen.setTextColor(COLOR_GREEN, COLOR_WHITE);
      backscreen.print("DCD: SAVED (date unknown)");
    }
    y += lh;
    backscreen.setTextColor(COLOR_GRAY, COLOR_WHITE);
    backscreen.setCursor(2, y);
    // autosave は「まだ手動保存していない機体だけ ON」。保険なので ON が初期状態。
    backscreen.printf("autosave:%s  saves:%u",
                      imu_cal_autosave_on() ? "ON " : "OFF", imu_cal_save_count());
    y += lh + 4;
  } else {
    // 工場校正のチップ（SCH16T）。保存するものが無いことを 1 行で言う。
    backscreen.setTextColor(COLOR_GRAY, COLOR_WHITE);
    backscreen.setCursor(2, y);
    backscreen.printf("%s: factory cal, nothing to save", imu_sensor_name());
    y += lh + 4;
  }

  // ---- メニュー ----
  const int mh2 = 15;
  for (int i = 0; i < IMU2_MENU_COUNT; i++) {
    const bool sel = (imu2_cursor == i);
    backscreen.setCursor(2, y);
    backscreen.setTextColor(sel ? COLOR_MAGENTA : COLOR_BLACK, COLOR_WHITE);
    backscreen.print(sel ? ">" : " ");
    backscreen.setCursor(14, y);
    switch (i) {
      case IMU2_MENU_SAVECAL: {
        // ★ 条件は acc==3 かつ gyr==3（地磁気は入れない。屋内では 3 に届かない）。
        // ★ 保存するものが無いチップ（SCH16T）でも**行は消さない。**
        //   消すと IMU2_MENU_* の添字とカーソル位置がずれる。灰色で無効を示す。
        const bool rdy = has_cal && imu_cal_ready();
        if (!sel) backscreen.setTextColor(rdy ? COLOR_GREEN : COLOR_GRAY, COLOR_WHITE);
        if (!has_cal) backscreen.print("SAVE CAL  (n/a)");
        else if (rdy) backscreen.print("SAVE CAL  [READY]");
        else          backscreen.print("SAVE CAL  (need A=3 G=3)");
        break;
      }
      case IMU2_MENU_NEXTPAGE:
        backscreen.print("Next page (ESKF) >");
        break;
      case IMU2_MENU_BACK:
        backscreen.print("< Back to page 1");
        break;
    }
    y += mh2;
  }

  backscreen.unloadFont();
  backscreen.pushSprite(0, 40);
}


// ============================================================
//  IMU / ESKF 3/3 — ESKF の状態と調整
// ============================================================
static void draw_imu_page3() {
  header_footer.fillScreen(COLOR_WHITE);
  header_footer.setTextColor(COLOR_BLACK, COLOR_WHITE);
  header_footer.setTextSize(2);
  header_footer.setCursor(1, 11);
  header_footer.print("IMU / ESKF  3/3");
  draw_imu_status_dot();
  header_footer.pushSprite(0, -10);

  backscreen.fillScreen(COLOR_WHITE);
  backscreen.loadFont(AA_FONT_SMALL);
  backscreen.setTextColor(COLOR_BLACK, COLOR_WHITE);

  int y = 2;
  const int lh = 12;
  const float R2D = 180.0f / (float)M_PI;

  backscreen.setTextColor(COLOR_GRAY, COLOR_WHITE);
  backscreen.setCursor(2, y); backscreen.print("-- ESKF --"); y += lh;
  const bool ready = attitude_ready();
  backscreen.setTextColor(ready ? COLOR_GREEN : COLOR_ORANGE, COLOR_WHITE);
  backscreen.setCursor(2, y);
  backscreen.printf("%s   GNSS upd:%lu", ready ? "READY" : "INIT...",
                    (unsigned long)attitude_get_gnss_updates());
  backscreen.fillCircle(232, y + 6, 4, imu_row_col(imu_ok_ready()));
  y += lh;

  float bg[3], ba[3];
  attitude_get_gyro_bias(bg);
  attitude_get_accel_bias(ba);
  backscreen.setTextColor(COLOR_BLACK, COLOR_WHITE);
  backscreen.setCursor(2, y);
  // 上限（1.0deg/s）に張り付いていたら初期姿勢誤差を吸っている疑い
  backscreen.printf("bg %+5.2f %+5.2f %+5.2f d/s", bg[0]*R2D, bg[1]*R2D, bg[2]*R2D); y += lh;
  backscreen.setCursor(2, y);
  backscreen.printf("ba %+5.2f %+5.2f %+5.2f m/s2", ba[0], ba[1], ba[2]); y += lh + 2;

  // ヨーの信頼度。水平加速度がある間しか可観測にならず、等速直進では育つ。
  // 95%(2σ) で表記する。1σ のままだと「これ以下なら安心」と誤読されやすい。
  const float yacc = attitude_get_yaw_acc95_deg();
  backscreen.setTextColor(yacc < 10.0f ? COLOR_GREEN
                        : yacc < 40.0f ? COLOR_ORANGE : COLOR_RED, COLOR_WHITE);
  backscreen.setCursor(2, y);
  backscreen.printf("yaw acc +-%.0f deg(95%%) src:%s",
                    yacc, (attitude_get_yaw_source() == ATT_YAW_SRC_GNSS) ? "GNSS" : "none");
  y += lh + 2;

  float lr, lp;
  attitude_get_level_offset(lr, lp);
  backscreen.setTextColor(COLOR_BLACK, COLOR_WHITE);
  backscreen.setCursor(2, y);
  // 較正した日（JST の MM/DD）も併記する。警告が出ていないときでも
  // 「いつ APPLY したのか」を人が確認できるようにしておく。--/-- は不明
  // （測位していない場所で APPLY した、または一度も APPLY していない）。
  // ★ これは SD の設定に入っている値で、上のページの DCD とは別物。
  const uint32_t cd = attitude_get_calib_date();
  if (cd) backscreen.printf("level offset R%+.1f P%+.1f %02u/%02u", lr, lp,
                            (unsigned)(cd / 100 % 100), (unsigned)(cd % 100));
  else    backscreen.printf("level offset R%+.1f P%+.1f --/--", lr, lp);
  y += lh + 4;

  // ---- 調整メニュー ----
  // 日常の運用では触らない項目。実飛行での検証がまだなので、片方だけ切って
  // 切り分けられるよう残してある（ページ1のマスタースイッチとは別物）。
  const int mh2 = 15;
  for (int i = 0; i < IMU3_MENU_COUNT; i++) {
    const bool sel = (imu3_cursor == i);
    backscreen.setCursor(2, y);
    backscreen.setTextColor(sel ? COLOR_MAGENTA : COLOR_BLACK, COLOR_WHITE);
    backscreen.print(sel ? ">" : " ");
    backscreen.setCursor(14, y);
    switch (i) {
      case IMU3_MENU_AUTOROLL:
        backscreen.printf("Roll trim during flight: %s",
                          attitude_get_roll_trim_enabled() ? "ON " : "OFF");
        backscreen.fillCircle(232, y + 6, 4, imu_row_col(imu_ok_trim()));
        break;
      case IMU3_MENU_WIND:
        backscreen.printf("Wind estimate: %s",
                          attitude_get_wind_enabled() ? "ON " : "OFF");
        break;
      case IMU3_MENU_BACK:
        backscreen.print("< Back to page 1");
        break;
    }
    y += mh2;
  }

  backscreen.unloadFont();
  backscreen.pushSprite(0, 40);
}


// ============================================================
//  PONS Link（機体⇄ボート無線）の設定画面
//    ★ 無線方式に依存しない表示にしてある。CH と PROFILE は「数値」として
//      出すだけで、意味は無線層が決める。そのため「SF8」のような
//      方式固有の言い方はしていない。
// ============================================================
int wireless_cursor = 0;

void draw_wireless(int cursor) {
  header_footer.fillScreen(COLOR_WHITE);
  header_footer.setTextColor(COLOR_BLACK, COLOR_WHITE);
  header_footer.setTextSize(2);
  header_footer.setCursor(1, 11);
  header_footer.print("WIRELESS LINK");
  // 大会の推奨設定＝パイロット機が送信モード。右上の丸で一目で分かるようにする。
  header_footer.fillCircle(SCREEN_WIDTH - 7, 9, 5,
      (link_get_mode() == LINK_MODE_TX) ? COLOR_GREEN : COLOR_ORANGE);
  header_footer.pushSprite(0, -10);

  backscreen.fillScreen(COLOR_WHITE);
  backscreen.loadFont(AA_FONT_SMALL);
  backscreen.setTextWrap(false);

  int y = 4;
  const int lh = 14;

  // ---- [0] モード ----
  const uint8_t mode = link_get_mode();
  const char* modestr = (mode == LINK_MODE_TX) ? "SENDER (aircraft)"
                      : (mode == LINK_MODE_RX) ? "RECEIVER (boat)"
                                               : "OFF";
  backscreen.setTextColor(cursor == 0 ? COLOR_BLUE : COLOR_BLACK, COLOR_WHITE);
  backscreen.setCursor(2, y);
  backscreen.printf("%sMode    : %s", cursor == 0 ? ">" : " ", modestr);
  y += lh;

  // ---- [1] チャネル / [2] 拡散率 ----
  // 番号だけだと現地で何を選んでいるのか分からないので、実際の周波数と SF を出す。
  // CH0 = 920.8MHz、0.2MHz 刻み（CH12 = 923.2MHz。ここまでが休止 50ms 固定の帯域）。
  const uint8_t ch = link_get_radio_ch();
  backscreen.setTextColor(cursor == 1 ? COLOR_BLUE : COLOR_BLACK, COLOR_WHITE);
  backscreen.setCursor(2, y);
  backscreen.printf("%sCh      : %u  (%.1f MHz)", cursor == 1 ? ">" : " ",
                    ch, 920.8f + 0.2f * ch);
  y += lh;
  // ★ 帯域幅（500kHz 固定）ではなく **送信時間と電波占有率** を出す。
  //   BW は変えられないので毎回出しても情報にならない。一方 SF は現地で
  //   「届かないから上げよう」と回す項目で、1 段上げると感度が 2.5dB 上がる代わりに
  //   **送信時間＝送信電流が約 1.8 倍**になる（SF8 98ms/9.8% → SF10 340ms/34%）。
  //   その代償を**回すその場で**見せる。すぐ下の Group 行の注意書きと同じ考え方で、
  //   「変更してから警告するより、変更する前に見えているほうが効く」。
  //   1Hz 運用なので占有率 [%] は送信時間 [ms] / 10 で出せる（docs/pons_link.md §3）。
  //   ※ 文字数は従来の "(BW 500kHz)" と同じ 26 文字に収まる（最長 SF11）。
  {
    const uint8_t  prof = link_get_radio_profile();
    const uint16_t at   = e220_airtime_ms(prof);
    backscreen.setTextColor(cursor == 2 ? COLOR_BLUE : COLOR_BLACK, COLOR_WHITE);
    backscreen.setCursor(2, y);
    backscreen.printf("%sSF      : %u  (%ums %u%%)", cursor == 2 ? ">" : " ",
                      e220_profile_to_sf(prof), at, (unsigned)(at / 10));
  }
  y += lh;
  // ★ グループ ID。**3 台とも同じ値**にすること。既定 0。
  //   同じ会場に別チームの PONS がいても取り違えないための識別子で、
  //   電波の設定ではなくペイロードの中身。モジュールへの書き込みは要らない。
  backscreen.setTextColor(cursor == 3 ? COLOR_BLUE : COLOR_BLACK, COLOR_WHITE);
  backscreen.setCursor(2, y);
  backscreen.printf("%sGroup   : %u", cursor == 3 ? ">" : " ", link_get_group());
  y += lh;
  // ★ 常設の注意書き。変更してから警告するより、変更する前に見えているほうが効く。
  //   この 3 つが 1 台でもずれると症状は「無信号」で、現場では距離や故障と区別が付かない。
  backscreen.setTextColor(COLOR_ORANGE, COLOR_WHITE);
  backscreen.setCursor(2, y);
  backscreen.print(" ^ 3 units must match");
  y += lh;

  // ---- [4] 送信前チェックの手動再実行 ----
  // ★ 送信モードのときだけ意味がある。RX / OFF ではグレーにして、
  //   選んでも鳴らして断る（GPS_TFT_map.ino の case 4）。
  //   アンテナの向きや置き場所を変えながら雑音と他機を測り直すための入口。
  {
    const bool can_pf = (mode == LINK_MODE_TX);
    backscreen.setTextColor(cursor == 4 ? COLOR_BLUE
                                        : (can_pf ? COLOR_BLACK : COLOR_GRAY), COLOR_WHITE);
    backscreen.setCursor(2, y);
    backscreen.printf("%sPreflight: %s", cursor == 4 ? ">" : " ",
                      can_pf ? "re-run" : "(TX only)");
  }
  y += lh + 4;

  // ---- 状態 ----
  backscreen.setTextColor(COLOR_GRAY, COLOR_WHITE);
  backscreen.setCursor(2, y);
  backscreen.print("---- status ----");
  y += lh;

  // 無線モジュールが応答しているか。ここが NG なら以下の数値は意味を持たない。
  backscreen.setTextColor(link_module_alive() ? COLOR_GREEN : COLOR_RED, COLOR_WHITE);
  backscreen.setCursor(2, y);
  backscreen.printf(" Module  : %s", link_module_alive() ? "OK" : "NO RESPONSE");
  y += lh;

  // ★★ リプレイ中・デモ中は無線を「OFF 扱い」にしている（link.h）。
  //   **設定値は書き換えていない**ので、ここに理由を出さないと
  //   「RECEIVER のままなのに何も映らない」「Sent が増えない」の原因に辿り着けない。
  //   ここは**無線そのもののページ**なので、地図側と違って隠さず出すのが正しい。
  if (mode != LINK_MODE_OFF && link_rf_suppressed()) {
    backscreen.setTextColor(COLOR_ORANGE, COLOR_WHITE);
    backscreen.setCursor(2, y);
    backscreen.printf(" Hold    : %s (%s)", getReplayMode() ? "replay" : "demo",
                      (mode == LINK_MODE_TX) ? "no TX" : "no mirror");
    backscreen.setTextColor(COLOR_BLACK, COLOR_WHITE);
    y += lh;
  }

  if (mode == LINK_MODE_RX) {
    backscreen.setTextColor(COLOR_BLACK, COLOR_WHITE);
    backscreen.setCursor(2, y);
    // ★ ここは **直近 10 秒の平均** を主役にする。1 発ぶんの RSSI は数 dB
    //   ふらつくので、アンテナの向きや置き場所を現地で比べる用途には使えない。
    //   地図に出るアンテナ本数もこの値から決めている（link_rssi_bars）。
    if (link_is_receiving()) {
      const uint8_t bars = link_rssi_bars();
      backscreen.setTextColor(bars >= 2 ? COLOR_GREEN : COLOR_ORANGE, COLOR_WHITE);
      backscreen.printf(" Signal  : %d dBm (10s)  %u/3", link_rssi_avg10(), bars);
      backscreen.setTextColor(COLOR_BLACK, COLOR_WHITE);
    } else if (link_other_group_seen()) {
      // ★ 電波は届いていて、グループ ID だけが食い違っている。
      //   これを「無信号」と同じ表示にしてはいけない。原因に辿り着けなくなる。
      //   （SD が飛んで group が 0 に戻ったときに、まさにこれが出る）
      backscreen.setTextColor(COLOR_ORANGE, COLOR_WHITE);
      backscreen.printf(" Signal  : GROUP %u FOUND", link_other_group_id());
      backscreen.setTextColor(COLOR_BLACK, COLOR_WHITE);
    } else {
      backscreen.print(" Signal  : searching...");
    }
    y += lh;
    backscreen.setCursor(2, y);
    // ★ bad = magic は合ったのに検証に落ちた数＝**届いたが化けた**フレーム。
    //   Miss（seq の欠番）は「化けた」と「来なかった」を合算した数なので、
    //   この 2 つを並べて初めて原因が切り分けられる。
    //   bad が増える → 信号は届いている。アンテナの向き・位置・SF を見直す
    //   bad が増えず Miss だけ増える → 圏外・CH 違い・送信機が送っていない
    //   ログ（60 秒ごと）より速いので、アンテナを動かしながら見るのはこちら。
    //   ★ bad は uint32 なので素で出すと最大 10 桁になり、この行だけ
    //     40 文字まで伸びて右端が切れる。診断用の目安なので 4 桁で打ち止めにする。
    {
      const uint32_t bad = e220_bad_frames();
      if (bad <= 9999) backscreen.printf(" Rx/Miss : %u / %u  bad %lu",
                                         link_rx_count(), link_miss_count(),
                                         (unsigned long)bad);
      else             backscreen.printf(" Rx/Miss : %u / %u  bad 9999+",
                                         link_rx_count(), link_miss_count());
    }
    y += lh;
    backscreen.setCursor(2, y);
    // 直近 1 発の生の値。上の 10 秒平均との差が、ばらつきの大きさになる。
    backscreen.printf(" Last    : %d dBm", link_rssi());
    y += lh;
    backscreen.setCursor(2, y);
    // 環境雑音。限界 RSSI ≒ 雑音 + SF の SNR 閾値 なので、
    // これと上の RSSI の差が「あとどれだけ余裕があるか」になる。
    // 熱雑音は BW500kHz で約 -111dBm。-104dBm 程度なら静かな部類。
    // ★ 余裕（margin）をここに併記する。この行のコメントが言っている
    //   「これと上の RSSI の差が、あとどれだけ余裕があるか」を、
    //   引き算せずに読めるようにするため。
    //   本数（0〜3）は 3 段階しかないので、アンテナを少し動かしたときの
    //   変化が読めない。置き場所を A/B で比べるには dB の数字が要る。
    //   根拠は本数とまったく同じ（link_rssi_margin_db）。食い違わせない。
    {
      const int16_t nz = link_noise_dbm();
      // ★ 「受信中か」で分けること。margin != 0 で分けてはいけない。
      //   ちょうど限界ぴったり（0dB）も起こり得る値で、そのとき
      //   「受信していない」と同じ表示になってしまう。
      const bool    has_mg = link_is_receiving();
      const int8_t  mg = link_rssi_margin_db();
      if (nz && has_mg)     backscreen.printf(" Noise   : %d dBm  mgn %+ddB", nz, mg);
      else if (nz)          backscreen.printf(" Noise   : %d dBm", nz);
      else if (has_mg)      backscreen.printf(" Noise   : ---  mgn %+ddB", mg);
      else                  backscreen.print(" Noise   : ---");
    }
    y += lh;

    // 送信機の健康状態。受信側からは知りようがないので電波で運んでいる。
    // 飛ぶ前に気づきたい項目だけを載せてある（link_proto.h の status 設計）。
    const uint16_t st = link_sender_status();
    if (link_is_receiving()) {
      backscreen.setTextColor(st ? COLOR_RED : COLOR_GREEN, COLOR_WHITE);
      backscreen.setCursor(2, y);
      if (!st) backscreen.print(" Sender  : OK");
      else {
        backscreen.print(" Sender  :");
        if (st & LINK_ST_SD_ERROR)    backscreen.print(" SD");
        if (st & LINK_ST_IMU_ERROR)   backscreen.print(" IMU");
        if (st & LINK_ST_NEEDS_APPLY) backscreen.print(" CAL");
        if (st & LINK_ST_BAT_LOW)     backscreen.print(" BAT");
      }
      y += lh;
      if (link_dest_mismatch()) {
        backscreen.setTextColor(COLOR_ORANGE, COLOR_WHITE);
        backscreen.setCursor(2, y);
        backscreen.print(" Dest    : DIFFERS from sender");
        y += lh;
      }
    }
  } else if (mode == LINK_MODE_TX) {
    // 送信機側で唯一確かめられる**実際に送出できた回数**。
    // モジュールがビジーでスロットを捨てると、ここが経過秒数より少なくなる。
    backscreen.setTextColor(COLOR_BLACK, COLOR_WHITE);
    backscreen.setCursor(2, y);
    // ★ 抑止中に「Sending 1Hz」と書くと嘘になる。上の Hold 行と二重になるが、
    //   **断言している文のほうを直す**（Hold を見落としても誤解しない）。
    backscreen.print(link_rf_suppressed() ? " Sending : held (not on air)"
                                          : " Sending 1Hz (no uplink)");
    y += lh;
    backscreen.setCursor(2, y);
    backscreen.printf(" Sent    : %u", link_tx_count());
    y += lh;

    // ---- 送信前チェックの結果 ----
    // ★ 「送信機が 2 台いる」を送信機側で出せるのはここだけ。
    //   通常運転では送信の合間 mode 3 で寝ていて聴けないので、検出は受信機の
    //   seq 逆行に頼るしかなかった（link.h）。TX に入った直後の数秒だけ
    //   mode 0 で聴くことで、飛ぶ前に自分で確かめられるようにしてある。
    const LinkPreflightState pst = link_preflight_state();
    const uint8_t pf = link_preflight_flags();
    backscreen.setCursor(2, y);
    if (pst == LINK_PF_RUNNING) {
      backscreen.setTextColor(COLOR_ORANGE, COLOR_WHITE);
      backscreen.printf(" Preflt  : checking... %lus",
                        (unsigned long)((link_preflight_remain_ms() + 999) / 1000));
    } else if (pst != LINK_PF_DONE) {
      backscreen.setTextColor(COLOR_GRAY, COLOR_WHITE);
      backscreen.print(" Preflt  : not run");
    } else if (pf & LINK_PFF_PONS_SAME) {
      // 同じ CH/SF/Group に送信機が 2 台。受信側の表示（DUP_SENDER）と用語を揃える。
      // RSSI を添えるのは、隣で出ているのか遠くなのかで対処が変わるため。
      backscreen.setTextColor(COLOR_RED, COLOR_WHITE);
      backscreen.printf(" Preflt  : DUP SENDER %ddBm", link_preflight_pons_rssi());
    } else if (pf & LINK_PFF_PONS_OTHER) {
      backscreen.setTextColor(COLOR_RED, COLOR_WHITE);
      backscreen.printf(" Preflt  : PONS grp%u %ddBm",
                        link_preflight_other_group(), link_preflight_pons_rssi());
    } else if (pf & LINK_PFF_BURST) {
      backscreen.setTextColor(COLOR_ORANGE, COLOR_WHITE);
      backscreen.print(" Preflt  : BUSY (bursts)");
    } else if (pf & LINK_PFF_NOISY) {
      backscreen.setTextColor(COLOR_ORANGE, COLOR_WHITE);
      backscreen.printf(" Preflt  : NOISY %d dBm", link_preflight_noise_med());
    } else if (pf & LINK_PFF_SKIPPED) {
      // モジュール無応答か、雑音を 1 つも取れなかった（RSSI バイト無効の疑い）。
      // どちらも「静かだった」ではないので、緑にしてはいけない。
      backscreen.setTextColor(COLOR_ORANGE, COLOR_WHITE);
      backscreen.print(" Preflt  : NOT MEASURED");
    } else {
      backscreen.setTextColor(COLOR_GREEN, COLOR_WHITE);
      backscreen.printf(" Preflt  : OK (%d dBm)", link_preflight_noise_med());
    }
    backscreen.setTextColor(COLOR_BLACK, COLOR_WHITE);
    y += lh;
  }
  y += 4;

  // ---- [5] 戻る ----
  // ★ 項目を足したら**ここの番号も直すこと。**WIRELESS_MENU_COUNT・
  //   longPressCallback の case・この描画の 3 つが揃っていないと、
  //   カーソルが 2 箇所で反転したり、選べない項目ができたりする。
  backscreen.setTextColor(cursor == 5 ? COLOR_BLUE : COLOR_BLACK, COLOR_WHITE);
  backscreen.setCursor(2, y);
  backscreen.printf("%sReturn", cursor == 5 ? ">" : " ");

  backscreen.unloadFont();
  // ★ **push_backscreen() を呼んではいけない。**あれは地図画面専用で、
  //   (1) y=50 に置く（詳細画面は y=40）ので上に 10px の隙間が残り、
  //       前の画面の切れ端がそこに居座る
  //   (2) VSI バーと draw_link_overlay() を重ねる。受信モードでは
  //       設定の上に受信枠の矩形まで描かれる
  //   詳細画面は自前で置く。フッタは誰も上書きしないので、ここで消す。
  backscreen.pushSprite(0, 40);
  tft.fillRect(0, SCREEN_HEIGHT - 40, SCREEN_WIDTH, 40, COLOR_WHITE);
}

void draw_imudetail(int page) {
  switch (page % 3) {
    case 0:  draw_imu_page1(); break;   // 較正（SETPITCH/APPLY）とマスタースイッチ
    case 1:  draw_imu_page2(); break;   // BNO085 の生値と校正(DCD)
    default: draw_imu_page3(); break;   // ESKF の状態と調整
  }
}




// ============================================================
//  PONS Link の受信モード表示
// ============================================================

// 1bit マスクを指定色で描く。0 のビットは透明（背景をそのまま残す）。
// 色を後から与えられるのがマスクを使う理由そのもの（link_icons.h 参照）。
static void draw_mask(TFT_eSprite &spr, int x, int y, int w, int h,
                      const uint8_t* data, uint16_t color) {
  const int rowbytes = (w + 7) / 8;
  for (int j = 0; j < h; j++) {
    for (int i = 0; i < w; i++) {
      uint8_t b = pgm_read_byte(&data[j * rowbytes + (i >> 3)]);
      if (b & (0x80 >> (i & 7))) spr.drawPixel(x + i, y + j, color);
    }
  }
}

// 受信モードの色。MIRROR = ティール、NO SIGNAL = 赤。
static uint16_t link_frame_color() {
  return (link_display_state() == LINK_DISP_MIRROR) ? COLOR_CYAN : COLOR_RED;
}

// 地図の左上に [無線アイコン][役割アイコン] を置く。
// 受信モードでは役割アイコンを 1Hz で点滅させる（draw_replay_indicator と同じ流儀）。
//
// ★ **リプレイ中・デモ中はここへ来ない**（draw_link_overlay が先に return する）。
//   0.978〜0.984 の「リプレイ中は灰色の弧 1 本」は畳んだ —
//   **役割アイコンが出ること自体が「そのとき送信機だった」に見える**。
//   戻すなら、再生中の画面に無線の役割を描いてよいのかから考え直すこと。
static void draw_link_icons() {
  const uint8_t mode = link_get_mode();
  if (mode == LINK_MODE_OFF) return;    // アイコンが無いこと自体が「無線オフ」の表示

  const bool rx = (mode == LINK_MODE_RX);
  const uint16_t col = rx ? COLOR_CYAN : COLOR_ORANGE;

  // ★ 地図左上は draw_gs_track() が使っている。GS の数値は NM_FONT_MEDIUM で
  //   y=1..32 あたりまで占めるので、その下に逃がす（重ねると数値が読めなくなる）。
  const int x = 3, y = 40;

  // 無線アイコン。**受信と送信で絵そのものを変える**（docs/pons_link.md §5）。
  //   受信 … アンテナ 0〜3 本。本数と色の両方で強度を示す。
  //   送信 … 飛行機から出ていく電波の弧。
  //     ★ ここにアンテナ本数を出してはいけない。送信側には受信の手段が無く、
  //       強度を測っていないのに測ったように見せることになる。
  //       弧は「今送れた」ことだけを示し、送出のたびに 1 回膨らむ。
  //   どちらも、切れているときは 0 の絵の上に赤い×を重ねる。
  //   「弱い」と「切れている」を色だけで区別させないため。
  uint8_t  level = 0;                      // 受信=本数 / 送信=弧の数
  uint16_t rcol  = COLOR_GRAY;
  bool     lost  = true;
  const uint8_t* const* icons = rx ? ICON_RSSI_BARS : ICON_TX_WAVES;

  if (!link_module_alive()) {
    // モジュール自体が応答していない。強度も送出も語れない。
  } else if (!rx && link_preflight_state() == LINK_PF_RUNNING) {
    // ★ 送信前チェックの最中。まだ 1 回も送っていないので、下の分岐に落とすと
    //   「弧 0 本＋赤い×」＝送れていない、に見えてしまう。故障と区別できないので
    //   専用の見た目にする。橙の弧 1 本＝「今は聴いている」。
    level = 1;
    rcol  = COLOR_ORANGE;
    lost  = false;
  } else if (!rx) {
    // 送出の直後だけ弧を伸ばす。脈動が止まる＝送れていない、が一目で分かる。
    const uint32_t since = link_since_tx_ms();
    level = (since == 0xFFFFFFFFu) ? 0 : (since < LINK_TX_PULSE_MS ? 3 : 1);
    rcol  = COLOR_GREEN;
    lost  = (level == 0);                  // 一度も送れていないなら×を出す
  } else if (link_is_receiving()) {
    level = link_rssi_bars();
    rcol  = (level >= 2) ? COLOR_GREEN : COLOR_ORANGE;
    lost  = false;
  }
  // 役割アイコン(32px)の縦中央に合わせる。
  const int ry = y + (ICON_PLANE_H - ICON_RSSI_H) / 2;
  draw_mask(backscreen, x, ry, ICON_RSSI_W, ICON_RSSI_H, icons[level], rcol);
  if (lost) draw_mask(backscreen, x, ry, ICON_RSSI_W, ICON_RSSI_H, ICON_RSSI_X, COLOR_RED);

  // 役割アイコン。受信モードだけ点滅させて目を引く（docs/pons_link.md §5）。
  const bool blink_on = !rx || ((millis() / 500) % 2 == 0);
  if (blink_on) {
    const int ix = x + ICON_RSSI_W + 3;
    if (rx) draw_mask(backscreen, ix, y, ICON_BOAT_W,  ICON_BOAT_H,  ICON_BOAT,  col);
    else    draw_mask(backscreen, ix, y, ICON_PLANE_W, ICON_PLANE_H, ICON_PLANE, col);
  }
}

// 電波が途切れている間、消せないポップアップを出し続ける（docs/pons_link.md §5）。
// ボタンでも消せないのは、消したまま忘れる事故を防ぐため。
// 地図が読める程度の高さに留め、画面を覆い切らない。
static void draw_link_nosignal_box() {
  const int bx = 10, by = 96, bw = SCREEN_WIDTH - 20, bh = 44;
  backscreen.fillRect(bx, by, bw, bh, COLOR_WHITE);
  backscreen.drawRect(bx,     by,     bw,     bh,     COLOR_RED);
  backscreen.drawRect(bx + 1, by + 1, bw - 2, bh - 2, COLOR_RED);
  backscreen.setTextColor(COLOR_RED, COLOR_WHITE);
  backscreen.setTextSize(1);
  backscreen.loadFont(AA_FONT_SMALL);
  backscreen.setCursor(bx + 10, by + 8);
  backscreen.print("RECEIVER MODE.");
  backscreen.setCursor(bx + 10, by + 24);
  backscreen.print("NO SIGNAL.");
  backscreen.unloadFont();
}

// 送信機が 2 台いるときのポップアップ（受信モードのみ・地図画面のみ）。
//
// ★ **これが無いと、飛行中に検出できる唯一の場所に表示が無い状態だった。**
//   送信機は送信の合間 mode 3 で寝ていて受信できないので、「同じ CH/SF/Group に
//   TX が 2 台いる」を飛行中に検出できるのは受信機だけ。にもかかわらず
//   link_dup_sender() はどこからも呼ばれておらず、音が 1 回鳴るのと
//   60 秒ログに残るだけだった（TX 側のプリフライトには表示があるのに、
//   飛行中に効く RX 側に無い、という逆転が起きていた）。
//
// この状態ではミラー表示が 2 機ぶんのテレメトリを交互に映すので、
// **画面の値そのものが信用できない**。地図を覆ってでも知らせる価値がある。
// 出しっぱなしにはならない。link_dup_sender() は最後の検出から
// LINK_DUPSENDER_HOLD_MS で false に戻るので、2 台目を止めれば自然に消える。
static void draw_link_dupsender_box() {
  const int bx = 10, by = 96, bw = SCREEN_WIDTH - 20, bh = 44;
  backscreen.fillRect(bx, by, bw, bh, COLOR_WHITE);
  backscreen.drawRect(bx,     by,     bw,     bh,     COLOR_RED);
  backscreen.drawRect(bx + 1, by + 1, bw - 2, bh - 2, COLOR_RED);
  backscreen.setTextColor(COLOR_RED, COLOR_WHITE);
  backscreen.setTextSize(1);
  backscreen.loadFont(AA_FONT_SMALL);
  backscreen.setCursor(bx + 10, by + 8);
  backscreen.print("DUP SENDER !!");
  backscreen.setCursor(bx + 10, by + 24);
  backscreen.print("2 TX ON SAME CH/GROUP");
  backscreen.unloadFont();
}

// 送信前チェックのポップアップ（送信モードのみ・地図画面のみ）。
//   点検中 : 橙枠。「今は聴いている」＝送信していないことを明示する
//   警告   : 赤枠。判定が出てから LINK_PF_WARN_SHOW_MS の間だけ出す
// ★ 出しっぱなしにはしない。送信は続いているので、地図を覆い続ける理由が無い。
//   見逃しても WIRELESS 画面と log.txt に残る。
static void draw_link_preflight_box() {
  const LinkPreflightState st = link_preflight_state();
  const uint8_t f = link_preflight_flags();
  const bool running = (st == LINK_PF_RUNNING);
  if (!running) {
    if (st != LINK_PF_DONE || f == LINK_PFF_OK) return;
    if (link_preflight_since_done_ms() > LINK_PF_WARN_SHOW_MS) return;
  }

  const uint16_t col = running ? COLOR_ORANGE : COLOR_RED;
  const int bx = 10, by = 96, bw = SCREEN_WIDTH - 20, bh = 44;
  backscreen.fillRect(bx, by, bw, bh, COLOR_WHITE);
  backscreen.drawRect(bx,     by,     bw,     bh,     col);
  backscreen.drawRect(bx + 1, by + 1, bw - 2, bh - 2, col);
  backscreen.setTextColor(col, COLOR_WHITE);
  backscreen.setTextSize(1);
  backscreen.loadFont(AA_FONT_SMALL);
  backscreen.setCursor(bx + 10, by + 8);

  if (running) {
    backscreen.print("CHECKING CHANNEL...");
    backscreen.setCursor(bx + 10, by + 24);
    backscreen.printf("%lus  (not sending yet)",
                      (unsigned long)((link_preflight_remain_ms() + 999) / 1000));
  } else if (f & LINK_PFF_PONS_SAME) {
    // 一番まずい状態。同じ CH/SF/Group にもう 1 台 TX がいる＝送信機が 2 台。
    backscreen.print("ANOTHER SENDER");
    backscreen.setCursor(bx + 10, by + 24);
    backscreen.print("ON THIS CHANNEL !!");
  } else if (f & LINK_PFF_PONS_OTHER) {
    backscreen.print("OTHER PONS FOUND");
    backscreen.setCursor(bx + 10, by + 24);
    backscreen.printf("group %u  - change CH", link_preflight_other_group());
  } else if (f & LINK_PFF_BURST) {
    backscreen.print("CHANNEL BUSY.");
    backscreen.setCursor(bx + 10, by + 24);
    backscreen.print("SOMETHING IS SENDING.");
  } else if (f & LINK_PFF_NOISY) {
    backscreen.print("CHANNEL NOISY.");
    backscreen.setCursor(bx + 10, by + 24);
    backscreen.printf("%d dBm  - change CH", link_preflight_noise_med());
  } else {                                   // LINK_PFF_SKIPPED
    // 「静かだった」ではなく「測れなかった」。合格と混同させない。
    backscreen.print("CH CHECK FAILED.");
    backscreen.setCursor(bx + 10, by + 24);
    backscreen.print("COULD NOT MEASURE.");
  }
  backscreen.unloadFont();
}

// 無線のオーバーレイ。push_backscreen() から必ず通る。
//   ・枠とポップアップは**受信モードだけ**。表示の意味が入れ替わるのは受信側なので。
//   ・アイコンは**送信モードでも出す**（地図画面のみ）。
//     ★ 機体側にこそ「今ちゃんと出ているか」を示すものが要る。
//       上りが無い以上、送信機は届いたかどうかを知りようがないので、
//       せめて「モジュールが生きていて送出できている」ことは見せる。
//       ここを受信モード限定にしていると ICON_PLANE が一度も描かれない。
static void draw_link_overlay() {
  // ★★ **リプレイ中・デモ中は無線の表示を一切出さない**（link.h / docs §5）。
  //   枠・アイコン・ポップアップはどれも「いま電波が出ているか／届いているか」で、
  //   再生中の画面の数字とは無関係。出どころは `REPLAY` / `REPLAY RX` バッジが担う。
  if (!link_live_ui_ok()) return;
  const uint8_t mode = link_get_mode();
  if (mode == LINK_MODE_OFF) return;

  if (mode == LINK_MODE_TX) {
    if (screen_mode == MODE_MAP) {
      draw_link_icons();
      // ★ 送信モードでもポップアップを出す唯一の場面。
      //   枠（常設）とは別物で、こちらは飛ぶ前の数秒だけ。
      draw_link_preflight_box();
    }
    return;
  }

  const uint16_t col = link_frame_color();

  // 3〜10 秒の間は点滅させて「切れかけ」を示す（docs/pons_link.md §5 の鮮度表）。
  bool show = true;
  const uint32_t age = link_age_ms();
  if (link_is_receiving() && age > 3000) show = ((millis() / 400) % 2 == 0);

  if (show) {
    // ★★ **右辺は描かない。** x = VSI_X 以降は VSI が占める領域で、VSI は
    //   backscreen の push より**後**に TFT へ直接 push される
    //   （GPS_TFT_map.ino。airdata 更新ごと ≒ 40Hz）。そのため右辺だけが
    //   「出てすぐ消える」点滅になっていた（実機 2026-09-27）。
    //   上辺・下辺も VSI_X で止める（VSI は全高を占めるため）。
    backscreen.fillRect(0, 0,                    VSI_X, 2, col);              // 上辺
    backscreen.fillRect(0, BACKSCREEN_SIZE - 2,  VSI_X, 2, col);              // 下辺
    backscreen.fillRect(0, 0,                    2, BACKSCREEN_SIZE, col);    // 左辺
  }
  if (screen_mode == MODE_MAP) {
    draw_link_icons();
    if (link_display_state() == LINK_DISP_NOSIGNAL) draw_link_nosignal_box();
    // ★ 送信機が 2 台。ミラーの値そのものが信用できないので、
    //   目的地の不一致より先に出す（同じ場所を使うため排他）。
    else if (link_dup_sender()) draw_link_dupsender_box();
    // ★ 目的地／ナビモードが送信側と違う。
    //   受信側の警告は自分で再計算する方式なので、目的地が違うと
    //   **コース警告だけが静かにずれる**（計算は正しいのに結果が違う）。
    //   一番たちの悪い壊れ方なので、地図上に出して気づけるようにする。
    else if (link_dest_mismatch()) {
      const int bx = 10, by = 200, bw = SCREEN_WIDTH - 20, bh = 22;
      backscreen.fillRect(bx, by, bw, bh, COLOR_WHITE);
      backscreen.drawRect(bx, by, bw, bh, COLOR_ORANGE);
      backscreen.setTextColor(COLOR_ORANGE, COLOR_WHITE);
      backscreen.setTextSize(1);
      backscreen.setCursor(bx + 6, by + 7);
      backscreen.print("DEST DIFFERS FROM SENDER");
    }
  }
}

// GNSS モジュール自体の接続断（要再起動）を知らせる警告。
// push_backscreen() の最後、draw_link_overlay() より後に呼ぶことで必ず最上位レイヤーにする。
// 以前は draw_nomapdata() の中でこれより先に描いており、LINK アイコンやコンパスの
// N/E/S/W など後から重なる要素に隠れていた。不透明の背景を敷いて完全に上書きする。
static void draw_gnss_disconnect_warning() {
  if (get_gnss_connection() || getReplayMode() || is_demo_active()) return;
  const int bx = 5, by = 44, bw = SCREEN_WIDTH - 10, bh = 56;
  backscreen.fillRect(bx, by, bw, bh, COLOR_WHITE);
  backscreen.drawRect(bx,     by,     bw,     bh,     COLOR_MAGENTA);
  backscreen.drawRect(bx + 1, by + 1, bw - 2, bh - 2, COLOR_MAGENTA);
  backscreen.setTextColor(COLOR_MAGENTA, COLOR_WHITE);
  backscreen.setTextSize(1);
  // フォントを明示的に指定する。指定しないと直前の描画が unloadFont() 済みの
  // デフォルトフォントを引き継ぎ、一瞬だけ小さいフォントで描かれることがある。
  backscreen.loadFont(AA_FONT_SMALL);
  // println の改行はカーソル x を 0 に戻してしまうため、各行で setCursor し直して
  // 枠の左辺（x=5,6 の 2px 分）と重ならないよう左マージンを揺れさせない。
  backscreen.setCursor(12, 50);
  backscreen.print("NO GNSS connection !!");
  backscreen.setCursor(12, 66);
  backscreen.print("Try power off then on.");
  backscreen.setCursor(12, 82);
  backscreen.print("Please contact developer.");
  backscreen.unloadFont();
  // ★ **地図用フォントに戻して抜ける。** ここはフレームの最後（push_backscreen）で
  //   走るので、戻さないと**次のフレームの draw_gs_track() が内蔵フォントのまま**
  //   "GS" や "Pavg" を描き始める（小さい字になる）。
  //   このファイルの約束（display_tft.cpp の「呼び出し側は地図用フォントを
  //   期待している」）に合わせる。
  backscreen.loadFont(AA_FONT_SMALL);
  backscreen.setTextColor(COLOR_BLACK, COLOR_WHITE);
}

// 警告音を抑制していることを地図に出す。
// ★ **「なぜ静かなのか」を画面で示すためのもの。** 抑制は「充電中 かつ マウント外れ」
//   のときだけで（GPS_TFT_map.ino の warn_muted_off_mount）、機体に載せて水平に
//   戻せば自動で解除される。解除操作を覚えておく必要は無い。
// ★ GNSS 断線の警告（y=44..99）と縦に並べる。両方出ても重ならない位置にしてある。
// ★ 点滅させる（3 秒のうち 2 秒だけ出す）。情報表示なので地図を隠し続けない。
static void draw_warn_mute_banner() {
  if (!warn_muted_off_mount()) return;
  if ((millis() / 1000) % 3 == 2) return;
  const int bx = 5, by = 104, bw = SCREEN_WIDTH - 10, bh = 40;
  backscreen.fillRect(bx, by, bw, bh, COLOR_WHITE);
  backscreen.drawRect(bx,     by,     bw,     bh,     COLOR_RED);
  backscreen.drawRect(bx + 1, by + 1, bw - 2, bh - 2, COLOR_RED);
  backscreen.setTextColor(COLOR_RED, COLOR_WHITE);
  // フォントを明示する。ここはフレームの最後（push_backscreen）で走るので、
  // 直前の描画が unloadFont() 済みだと内蔵フォントで描かれてしまう。
  backscreen.loadFont(AA_FONT_SMALL);
  backscreen.setCursor(12, by + 5);
  backscreen.print("IN MUTE DUE TO");
  backscreen.setCursor(12, by + 21);
  backscreen.print("CHARGING + OFF MOUNT");
  // ★ 地図用フォントと色に戻して抜ける（このファイルの約束）。
  backscreen.setTextColor(COLOR_BLACK, COLOR_WHITE);
}

void push_backscreen(){
  TIMING_START(push_bs);
  if (vario_volume > 0 && !vario_inhibit) {
    draw_vsi();
    vsi_sprite.pushToSprite(&backscreen, VSI_X, 0);  // Sprite→Sprite 合成
  }
  draw_link_overlay();
  draw_gnss_disconnect_warning();  // 最上位レイヤー。上の draw_link_overlay() より後に描く
  draw_warn_mute_banner();         // 同じく最上位。GNSS 警告の下に並ぶ
  backscreen.pushSprite(0, 50);
  TIMING_END(ts_push_backscreen, push_bs);
}

// backscreen の最上部に小さなテキスト（GS・m/s・TT ラベル）を描画する。
// trackwarning_until が有効な間は「TT」ラベルを赤/黒で点滅させてコース警告を示す。
// TT = True Track。機体に磁気コンパスを載せない方針になったので、表示は全て真方位。
// 画面に出す真方位の 3 桁表示値。ヘッダーと地図内で必ず同じ値になるよう
// 1 か所に集約する（以前ヘッダーは切り捨て、地図内は四捨五入で 1 度ずれていた）。
// 四捨五入した上で 0〜359 に丸め込む（359.7 度 → 360 ではなく 000）。
static int truetrack_display_deg() {
  return ((int)lroundf(get_gnss_truetrack()) % 360 + 360) % 360;
}
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
