MasaoC/GPS-TFT-Map_PONS/gnss.cpp

// ============================================================
// File    : gnss.cpp
// Project : PONS v7 (Pilot Oriented Navigation System for HPA)
// Role    : GNSS受信・解析の実装（u-blox UBX バイナリ受信）。
//           UBX NAV-PVT/NAV-SAT の解析、衛星情報収集、
//           位置・速度・時刻の取得、リプレイ管理、
//           地点選択式のデモ飛行（琵琶湖/白浜/笠岡/富士川/東京湾）、
//           フライトログCSVへの定期保存トリガー。
// Author  : MasaoC (@masao_mobile)
// Updated : 2026/10/08
// ============================================================
// 対象は u-blox SAM-M10Q 固定。Quectel LC86G 対応は v0.947 で削除済み（settings.h 参照）。
#include <Arduino.h>

#include "gnss.h"
#include "link.h"   // ミラー表示（受信モード）
#include "mysd.h"
#include "navdata.h"
#include "settings.h"
#include "display_tft.h"
#include "airdata.h"
#include "imu.h"
#include "src/imulog.h"   // 姿勢 ESKF のオフライン開発用 生データロガー
#include "attitude.h" // 姿勢 ESKF（機上リアルタイム版）

// GPS_TFT_map.ino で定義されている USERLED 永続点灯フラグ（致命エラー時に true にする）
extern volatile bool userled_forced_on;

// GNSS時刻を最後に受信したときのmillis()（Euler角ログの時刻推定用）
static uint32_t gnss_fix_millis = 0;
uint32_t get_gnss_fix_millis() { return gnss_fix_millis; }

// v6 は u-blox SAM-M10Q 専用。Mediatek(PMTK) / Quectel(PAIR) 用のコマンド定義は
// v5 以前のモジュール向けだったため削除した（必要になったら git 履歴から戻す）。


// --- u-blox UBX バイナリ NAV メッセージ設定 ---
// チェックサムは Fletcher-8（class〜payloadの全バイトに対して計算）
//
// UBX-CFG-PRT: UART1 を 38400bps・UBX プロトコルのみ（NMEA 無効）に設定
//   inProtoMask=0x0001(UBX only), outProtoMask=0x0001(UBX only)
#define UBLOX_CFG_PRT_38400_UBXONLY {0xB5,0x62,0x06,0x00,0x14,0x00,0x01,0x00,0x00,0x00,0xC0,0x08,0x00,0x00,0x00,0x96,0x00,0x00,0x01,0x00,0x01,0x00,0x00,0x00,0x00,0x00,0x7B,0x54}
// UBX-CFG-MSG: NAV-PVT(01 07) rate=1（毎測位で送信 → 2Hz）
#define UBLOX_ENABLE_NAVPVT  {0xB5,0x62,0x06,0x01,0x03,0x00,0x01,0x07,0x01,0x13,0x51}
// UBX-CFG-MSG: NAV-SAT(01 35) rate=2(1Hz) / rate=20(0.1Hz=10秒に1回)
#define UBLOX_NAVSAT_RATE_2  {0xB5,0x62,0x06,0x01,0x03,0x00,0x01,0x35,0x02,0x42,0xAE}
#define UBLOX_NAVSAT_RATE_20 {0xB5,0x62,0x06,0x01,0x03,0x00,0x01,0x35,0x14,0x54,0xC0}
// UBX-CFG-MSG: NAV-DOP(01 04) rate=2（1Hz）
#define UBLOX_ENABLE_NAVDOP  {0xB5,0x62,0x06,0x01,0x03,0x00,0x01,0x04,0x02,0x11,0x4C}
// UBX-CFG-NAV5: ダイナミックモデルを Airborne <1g（dynModel=6）に設定
//   mask=0x0001（dynModel のみ変更）、payload 36 bytes
#define UBLOX_CFG_NAV5_AIRBORNE1G \
  {0xB5,0x62,0x06,0x24,0x24,0x00, \
   0x01,0x00,0x06,0x00, \
   0x00,0x00,0x00,0x00,0x00,0x00,0x00,0x00, \
   0x00,0x00,0x00,0x00,0x00,0x00,0x00,0x00, \
   0x00,0x00,0x00,0x00,0x00,0x00,0x00,0x00, \
   0x00,0x00,0x00,0x00,0x00,0x00,0x00,0x00, \
   0x55,0xB4}

// --- GNSS 最新値の保持変数 ---
// UBX NAV-PVT（リプレイ中は CSV）から取り出した値をここに保存し、getter 経由で公開する。
double stored_longitude, stored_latitude, stored_truetrack, stored_gnss_altitude, stored_fixtype, stored_gs;
int stored_numsats;

// --- 最大 G/S 保持変数 ---
// maxgs        : 起動後の全時間最大 G/S [m/s]
// maxgs_5min   : 直近 5 分間の最大 G/S [m/s]（5分間更新がなければ現在値にリセット）
// *_hour / *_min : 最大値を記録した時刻（JST 時・分）
static float  maxgs            = 0.0f;
static int    maxgs_hour       = 0;
static int    maxgs_min        = 0;
static float  maxgs_5min       = 0.0f;
static int    maxgs_5min_hour  = 0;
static int    maxgs_5min_min   = 0;
static unsigned long maxgs_5min_last_update = 0;  // 5分保持の最終更新時刻 [ms]
bool gnss_connection = false;  // GNSS モジュールから1文字でも受信したことがあるか
// ★ 最後にバイトが届いた時刻。**飛行中の断線を検出するために要る。**
//   gnss_connection だけだと一度 true になったら戻らないので、コネクタが抜けても
//   画面は正常なまま航法を続けてしまっていた（get_gnss_connection 参照）。
static uint32_t gnss_last_byte_ms = 0;
// gnss_setup() 初回呼び出しでの UBX 設定コマンドが全部 ACK されたか（起動画面の進捗表示用）。
// リトライ呼び出し(setupcounter!=1)は設定を送り直さないので、初回の結果のまま変わらない。
static bool gnss_cfg_ok = false;
// デモ飛行の現在地点（DEMO_OFF でデモ停止）。GNSS を使わず仮想位置を生成する。
demo_site_t demo_site = DEMO_OFF;
double demo_lat = PLA_LAT;        // 仮想機体の現在位置
double demo_lon = PLA_LON;
double demo_mps = 0;              // 仮想対地速度 [m/s]
double demo_truetrack = 280;      // 仮想真方位 [deg]

// --- 衛星情報・受信フレームログ ---
SatelliteData satellites[MAX_SATELLITES];  // 最大 MAX_SATELLITES 衛星分のデータを保持（PRN 0 = 空き）
char last_nmea[MAX_LAST_NMEA][NMEA_MAX_CHAR];   // 直近の受信フレーム概要のリングバッファ（GNSS詳細画面用）
unsigned long last_nmea_time[MAX_LAST_NMEA];     // 各フレームの受信時刻（受信途絶の監視にも使う）
unsigned long last_gnss_setup_time = 0;   // 最後に gnss_setup() を呼んだ時刻（再接続ガード用）
int stored_nmea_index = 0;               // リングバッファの書き込み位置
bool new_location_arrived = false;       // 新しい位置情報が届いたことを Core0 に知らせるフラグ
bool newcourse_arrived = false;          // 新しいコース情報が届いたフラグ（毎秒更新）

// --- 測位品質（DOP・フィックスタイプ・使用衛星 PRN） ---
// UBX NAV-PVT / NAV-DOP / NAV-SAT の受信時に更新する。
#define GSA_MAX_PRN 12
static int    gsa_fixtype = 1;                // 1=No Fix, 2=2D, 3=3D
static float  gsa_pdop    = 0.0f;             // Position DOP
static float  gsa_hdop    = 0.0f;             // Horizontal DOP
static float  gsa_vdop    = 0.0f;             // Vertical DOP
static int    gsa_prns[GSA_MAX_PRN] = {};     // 測位に使用中の衛星 PRN（0=未使用）
static int    gsa_numsat  = 0;                // 測位使用衛星数

// UBX ハンドラーから参照するため前方宣言
void removeStaleSatellites();

// ============================================================
// UBX バイナリ受信パーサー（実 GNSS 受信用）
// リプレイモードはこの経路を通らず、SD の飛行 CSV から直接値を設定する。
// ============================================================
#define UBX_PAYLOAD_BUF_SIZE 768  // NAV-SAT 最大ペイロード (55 SVs×12+8=668) を余裕で収容

// UBX パーサー ステートマシン状態
enum UbxParseState {
  UBX_SYNC1=0, UBX_SYNC2, UBX_CLASS_ST, UBX_ID_ST,
  UBX_LEN1_ST, UBX_LEN2_ST, UBX_PAYLOAD_ST, UBX_CKA_ST, UBX_CKB_ST
};
static UbxParseState ubx_state   = UBX_SYNC1;
static uint8_t  ubx_cls          = 0;   // 受信中フレームのクラス
static uint8_t  ubx_msgid        = 0;   // 受信中フレームの ID
static uint16_t ubx_paylen       = 0;   // ペイロード長（バイト）
static uint16_t ubx_payidx       = 0;   // ペイロード書き込み位置
static uint8_t  ubx_cka_acc      = 0;   // チェックサム計算用 CK_A 累積
static uint8_t  ubx_ckb_acc      = 0;   // チェックサム計算用 CK_B 累積
static uint8_t  ubx_rx_cka       = 0;   // 受信 CK_A 一時保存
static uint8_t  ubx_buf[UBX_PAYLOAD_BUF_SIZE];  // ペイロード受信バッファ

// UBX NAV-PVT から得た GNSS データ（get_gnss_date/get_gnss_time・ログ保存などで参照）
static bool     ubx_time_valid   = false;  // UTC 時刻フィールドが有効か
static bool     ubx_date_valid   = false;  // UTC 日付フィールドが有効か
static uint16_t ubx_year         = 0;
static uint8_t  ubx_month        = 0;
static uint8_t  ubx_day          = 0;
static uint8_t  ubx_hour         = 0;
static uint8_t  ubx_min          = 0;
static uint8_t  ubx_sec          = 0;
static uint8_t  ubx_cs           = 0;    // センチ秒（nano フィールドから変換）
static bool     ubx_pos_valid    = false; // 有効な 2D/3D フィックスがあるか
static bool     ubx_pvt_valid    = false; // NAV-PVT を1回以上受信したか
static bool     ubx_pvt_updated  = false; // 新しい NAV-PVT が届いたことを gnss_loop() に通知
static bool     ubx_sat_updated  = false; // 新しい NAV-SAT が届いた
static uint32_t ubx_hacc_mm      = 0;     // 水平精度推定値（NAV-PVT bytes 40-43、mm 単位）
static uint32_t ubx_vacc_mm      = 0;     // 垂直精度推定値（NAV-PVT bytes 44-47、mm 単位）
static uint32_t ubx_sacc_mmps    = 0;     // 速度精度推定値（NAV-PVT bytes 68-71、mm/s 単位）
static float    ubx_veld_mps     = 0.0f;  // 垂直速度（NAV-PVT velD bytes 56-59、上昇正、m/s）
// NED 水平速度。姿勢 ESKF の速度観測に使う（旋回中の遠心加速度を分離して真の重力方向を得るため）。
// 符号は UBX の定義どおり N/E 正のまま保持する（velD だけは従来仕様に合わせて上昇正へ反転済み）。
static float    ubx_veln_mps     = 0.0f;  // 北向き速度（NAV-PVT velN bytes 48-51、m/s）
static float    ubx_vele_mps     = 0.0f;  // 東向き速度（NAV-PVT velE bytes 52-55、m/s）
static uint32_t ubx_itow_ms      = 0;     // GPS 週内時刻（NAV-PVT iTOW bytes 0-3、ms）
static bool     ubx_gnssFixOK    = false; // NAV-PVT flags bit0: gnssFixOK（GNSS フィックスが有効かつ品質 OK）

// UBX-NAV-PVT (class=0x01, id=0x07, payload=92 bytes) ハンドラー
// 位置・速度・時刻・衛星数・フィックスタイプをすべて解析して内部変数を更新する。
static void handle_navpvt(const uint8_t *p, uint16_t len) {
  if (len < 84) return;

  // UTC 日時フィールド（valid bits: bit0=validDate, bit1=validTime）
  uint8_t valid  = p[11];
  ubx_date_valid = (valid & 0x01) != 0;
  ubx_time_valid = (valid & 0x02) != 0;
  if (ubx_date_valid) {
    ubx_year  = (uint16_t)(p[4] | (p[5] << 8));
    ubx_month = p[6];
    ubx_day   = p[7];
    // u-blox は起動直後に validDate=1 でも year=2000/month=0/day=0 を返すことがある。
    // 2020 年以前・月日ゼロは未取得と同じく無効とみなす。
    // 月・日は上限も確認する。月は GPS_TFT_map.ino の days_in_month[] の添字に使われるため、
    // 13 以上が通ると配列外読み出しになる（utcToJst() は既に両側チェックしている）。
    if (ubx_year < 2020 || ubx_month == 0 || ubx_month > 12 || ubx_day == 0 || ubx_day > 31) {
      ubx_date_valid = false;
    }
  }
  if (ubx_time_valid) {
    ubx_hour  = p[8];
    ubx_min   = p[9];
    ubx_sec   = p[10];
  }
  // nano (int32, ナノ秒) → センチ秒に変換
  int32_t nano = (int32_t)(p[16] | (p[17]<<8) | (p[18]<<16) | (p[19]<<24));
  ubx_cs = (nano >= 0) ? (uint8_t)(nano / 10000000) : 0;
  // ubx_cs が確定した直後のファームウェア時刻を記録する。
  // ubx_pvt_updated ブロックで記録するより遅延が少なく、パケット間の揺れを抑えられる。
  gnss_fix_millis = millis();

  // フィックスタイプ・フラグ（u-blox fixType: 0=NoFix,1=DR,2=2D,3=3D,4=GNSS+DR）
  uint8_t fixType   = p[20];
  bool    gnssFixOK = (p[21] & 0x01) != 0;
  uint8_t numSV     = p[23];

  // 位置（1e-7 度単位の int32）
  int32_t lon  = (int32_t)(p[24]|(p[25]<<8)|(p[26]<<16)|(p[27]<<24));
  int32_t lat  = (int32_t)(p[28]|(p[29]<<8)|(p[30]<<16)|(p[31]<<24));
  int32_t hMSL = (int32_t)(p[36]|(p[37]<<8)|(p[38]<<16)|(p[39]<<24));  // mm above MSL

  // 水平・垂直精度推定値（bytes 40-43: hAcc mm、bytes 44-47: vAcc mm）
  ubx_hacc_mm   = (uint32_t)(p[40]|(p[41]<<8)|(p[42]<<16)|((uint32_t)p[43]<<24));
  ubx_vacc_mm   = (uint32_t)(p[44]|(p[45]<<8)|(p[46]<<16)|((uint32_t)p[47]<<24));
  ubx_gnssFixOK = gnssFixOK;

  // 速度（mm/s）・方向（1e-5 度）
  // velN (bytes 48-51) / velE (bytes 52-55): NED 水平速度。北・東が正。
  // velD (bytes 56-59): NED Down 方向（正=下降）→ 上昇正に反転して保存
  int32_t velN    = (int32_t)(p[48]|(p[49]<<8)|(p[50]<<16)|(p[51]<<24));
  int32_t velE    = (int32_t)(p[52]|(p[53]<<8)|(p[54]<<16)|(p[55]<<24));
  int32_t velD    = (int32_t)(p[56]|(p[57]<<8)|(p[58]<<16)|(p[59]<<24));
  int32_t gSpeed  = (int32_t)(p[60]|(p[61]<<8)|(p[62]<<16)|(p[63]<<24));
  int32_t headMot = (int32_t)(p[64]|(p[65]<<8)|(p[66]<<16)|(p[67]<<24));
  ubx_veln_mps  = velN * 1e-3f;   // mm/s → m/s（北正）
  ubx_vele_mps  = velE * 1e-3f;   // mm/s → m/s（東正）
  ubx_veld_mps  = -velD * 1e-3f;  // mm/s 下降正 → m/s 上昇正
  // 速度精度推定値（bytes 68-71: sAcc mm/s）
  ubx_sacc_mmps = (uint32_t)(p[68]|(p[69]<<8)|(p[70]<<16)|((uint32_t)p[71]<<24));
  // GPS 週内時刻（bytes 0-3: iTOW ms）。生 IMU ログとの時刻対応付けに使う。
  ubx_itow_ms   = (uint32_t)(p[0]|(p[1]<<8)|(p[2]<<16)|((uint32_t)p[3]<<24));

  // 姿勢 ESKF のオフライン開発用に、GNSS 速度を生 IMU ログへ同じ時間軸で記録する。
  // velD はここでは UBX 原義（下降正）に戻して記録し、PC 側で NED をそのまま扱えるようにする。
  imulog_push(IMULOG_ID_GNSSVEL, ubx_itow_ms, IMULOG_ACC_NONE,
              ubx_veln_mps, ubx_vele_mps, velD * 1e-3f, ubx_sacc_mmps * 1e-3f);

  // 姿勢 ESKF の速度観測。3D フィックス時のみ渡す（品質の最終判断は sAcc で ESKF 側が行う）。
  // リプレイ中は CSV 由来の値なので渡さない。
  if (gnssFixOK && fixType >= 3 && !getReplayMode()) {
    attitude_on_gnss_velocity(ubx_veln_mps, ubx_vele_mps, velD * 1e-3f,
                              ubx_sacc_mmps * 1e-3f);
  }

  // pDOP（0.01 スケール）
  uint16_t pDOP = (uint16_t)(p[76] | (p[77]<<8));
  gsa_pdop  = pDOP * 0.01f;

  // GSA 互換フィックスタイプ（1=NoFix, 2=2D, 3=3D）
  {
    static int prev_fixtype = 1;  // 前回のfixtype（遷移検出用）
    int new_fixtype;
    if      (fixType == 2)  new_fixtype = 2;
    else if (fixType >= 3)  new_fixtype = 3;
    else                    new_fixtype = 1;
    // no-fix → fix への遷移タイミングをSDに記録。
    // ★ 衛星数は stored_numsats ではなく **このパケットの numSV** を出すこと。
    //   stored_numsats への代入はこのブロックより後ろにあるので、ここで読むと
    //   **1 エポック前（= まだ no-fix だったとき）の値**が出る。fix 獲得の瞬間は
    //   ほぼ必ず 0 になり、ログが "fix=3 sats=0" という矛盾した見た目になっていた。
    if (prev_fixtype <= 1 && new_fixtype >= 2) {
      enqueueTask(createLogSdfTask("GNSS FIXED fix=%d sats=%d hAcc=%.1fm",
        new_fixtype, (int)numSV, ubx_hacc_mm / 1000.0f));
    }
    prev_fixtype  = new_fixtype;
    gsa_fixtype   = new_fixtype;
  }

  ubx_pos_valid = (fixType >= 2) && gnssFixOK;
  ubx_pvt_valid = true;

  if (ubx_pos_valid) {
    double new_lat = lat  * 1e-7;
    double new_lon = lon  * 1e-7;
    stored_latitude  = new_lat;
    stored_longitude = new_lon;
    stored_gnss_altitude  = hMSL * 1e-3;  // mm → m
  }

  stored_gs         = gSpeed * 1e-3f;  // mm/s → m/s
  double trk        = headMot * 1e-5;  // 1e-5 deg → deg
  if (trk <   0)  trk += 360.0;
  if (trk >= 360) trk -= 360.0;
  stored_truetrack  = trk;
  stored_numsats    = numSV;
  stored_fixtype    = ubx_pos_valid ? 2 : 0;
  gsa_numsat        = numSV;

  ubx_pvt_updated   = true;
}

// UBX-NAV-SAT (class=0x01, id=0x35) ハンドラー
// 各衛星の gnssId, svId, cno, elev, azim を satellites[] 配列に格納する。
// svUsed フラグが立っている衛星の PRN を gsa_prns[] に記録する。
static void handle_navsat(const uint8_t *p, uint16_t len) {
  if (len < 8) return;
  uint8_t numSvs = p[5];
  if ((uint16_t)(8 + numSvs * 12) > len) numSvs = (len - 8) / 12;

  // gsa_prns をリセットして使用中衛星 PRN を再構築
  int prn_idx = 0;
  for (int i = 0; i < GSA_MAX_PRN; i++) gsa_prns[i] = 0;

  for (int s = 0; s < numSvs; s++) {
    const uint8_t *sv = p + 8 + s * 12;
    uint8_t gnssId = sv[0];
    uint8_t svId   = sv[1];
    uint8_t cno    = sv[2];
    int8_t  elev   = (int8_t)sv[3];
    int16_t azim   = (int16_t)(sv[4] | (sv[5] << 8));
    uint32_t flags = (uint32_t)(sv[8]|(sv[9]<<8)|(sv[10]<<16)|(sv[11]<<24));
    bool svUsed    = (flags & 0x08) != 0;  // bit3=svUsed

    if (svId == 0) continue;

    // gnssId → satelliteType 変換
    int satType;
    switch (gnssId) {
      case 0: satType = SATELLITE_TYPE_GPS;     break;
      case 2: satType = SATELLITE_TYPE_GALILEO; break;
      case 3: satType = SATELLITE_TYPE_BEIDOU;  break;
      case 5: satType = SATELLITE_TYPE_QZSS;    break;
      case 6: satType = SATELLITE_TYPE_GLONASS; break;
      default: satType = SATELLITE_TYPE_UNKNOWN; break;
    }

    bool stored = false;
    for (int j = 0; j < MAX_SATELLITES; j++) {
      if ((satellites[j].PRN == svId && satellites[j].satelliteType == satType) || satellites[j].PRN == 0) {
        satellites[j].PRN          = svId;
        satellites[j].elevation    = (elev >= -90 && elev <= 90) ? elev : satellites[j].elevation;
        satellites[j].azimuth      = (azim >= 0 && azim < 360)   ? azim : satellites[j].azimuth;
        satellites[j].SNR          = (cno <= 99) ? cno : satellites[j].SNR;
        satellites[j].satelliteType = satType;
        satellites[j].lastReceived = millis();
        stored = true;
        break;
      }
    }
    if (!stored) {
      // 衛星ごとにログを積むと、1 メッセージで 20 スロットのタスクキューを溢れさせて
      // 他のタスクを落としてしまう（キュー満杯は USERLED 点灯として現れる）。10 秒に 1 回に制限する。
      static unsigned long last_satfull_log = 0;
      if (millis() - last_satfull_log > 10000) {
        last_satfull_log = millis();
        enqueueTask(createLogSdfTask("WARN:sat full svId=%d gnss=%d", svId, gnssId));
      }
    }
    // 使用中衛星を gsa_prns[] に記録（最大 GSA_MAX_PRN 個）
    if (svUsed && prn_idx < GSA_MAX_PRN) gsa_prns[prn_idx++] = svId;
  }
  ubx_sat_updated = true;
}

// UBX-NAV-DOP (class=0x01, id=0x04, payload=18 bytes) ハンドラー
// PDOP / HDOP / VDOP を更新し、10 秒に 1 回 SD ログに保存する。
static void handle_navdop(const uint8_t *p, uint16_t len) {
  if (len < 18) return;
  gsa_pdop = (uint16_t)(p[6]  | (p[7]  << 8)) * 0.01f;
  gsa_hdop = (uint16_t)(p[12] | (p[13] << 8)) * 0.01f;
  gsa_vdop = (uint16_t)(p[10] | (p[11] << 8)) * 0.01f;
  // 10 秒に 1 回 Acc 情報を SD ログに保存（衛星0件=明らかに屋内の場合はスキップ）
  static unsigned long last_dop_log = 0;
  if (millis() - last_dop_log >= 10000) {
    last_dop_log = millis();
    if (stored_numsats > 0) {
      enqueueTask(createLogSdfTask("ACC hAcc=%.1fm vAcc=%.1fm sAcc=%.2fm/s fix=%d sats=%d",
        ubx_hacc_mm / 1000.0f, ubx_vacc_mm / 1000.0f, ubx_sacc_mmps / 1000.0f,
        gsa_fixtype, stored_numsats));
    }
  }
}

// UBX バイナリフレームを 1 バイトずつ処理するステートマシン。
// B5 62 ヘッダーを検出し、クラス・ID・ペイロードを組み立ててチェックサムを確認する。
// チェックサム OK でハンドラーを呼び出し、last_nmea[] にラベルを記録する。
static void process_ubx(uint8_t b) {
  switch (ubx_state) {
    case UBX_SYNC1:
      if (b == 0xB5) ubx_state = UBX_SYNC2;
      break;
    case UBX_SYNC2:
      ubx_state = (b == 0x62) ? UBX_CLASS_ST : UBX_SYNC1;
      break;
    case UBX_CLASS_ST:
      ubx_cls = b;
      ubx_cka_acc = b; ubx_ckb_acc = b;  // Fletcher-8 初期化
      ubx_state = UBX_ID_ST;
      break;
    case UBX_ID_ST:
      ubx_msgid = b;
      ubx_cka_acc += b; ubx_ckb_acc += ubx_cka_acc;
      ubx_state = UBX_LEN1_ST;
      break;
    case UBX_LEN1_ST:
      ubx_paylen = b;
      ubx_cka_acc += b; ubx_ckb_acc += ubx_cka_acc;
      ubx_state = UBX_LEN2_ST;
      break;
    case UBX_LEN2_ST:
      ubx_paylen |= ((uint16_t)b << 8);
      ubx_cka_acc += b; ubx_ckb_acc += ubx_cka_acc;
      ubx_payidx = 0;
      ubx_state  = (ubx_paylen == 0) ? UBX_CKA_ST : UBX_PAYLOAD_ST;
      break;
    case UBX_PAYLOAD_ST:
      if (ubx_payidx < UBX_PAYLOAD_BUF_SIZE) ubx_buf[ubx_payidx] = b;
      ubx_payidx++;
      ubx_cka_acc += b; ubx_ckb_acc += ubx_cka_acc;
      if (ubx_payidx >= ubx_paylen) ubx_state = UBX_CKA_ST;
      break;
    case UBX_CKA_ST:
      ubx_rx_cka = b;  // 受信 CK_A を一時保存
      ubx_state  = UBX_CKB_ST;
      break;
    case UBX_CKB_ST: {
      ubx_state = UBX_SYNC1;
      if (ubx_rx_cka != ubx_cka_acc || b != ubx_ckb_acc) {
        #ifdef DEBUG_GBX_NMEA
        // チェックサム NG: クラス・ID と期待値を出力
        static unsigned long last_ckerr_log = 0;
        if (millis() - last_ckerr_log > 2000) {
          last_ckerr_log = millis();
          Serial.print("[UBX] CK NG cls="); Serial.print(ubx_cls, HEX);
          Serial.print(" id="); Serial.print(ubx_msgid, HEX);
          Serial.print(" len="); Serial.print(ubx_paylen);
          Serial.print(" exp="); Serial.print(ubx_cka_acc, HEX); Serial.print("/"); Serial.print(ubx_ckb_acc, HEX);
          Serial.print(" got="); Serial.print(ubx_rx_cka, HEX); Serial.print("/"); Serial.println(b, HEX);
        }
        #endif
        break;
      }
      // チェックサム OK: タイムスタンプ更新 + ハンドラー呼び出し
      gnss_connection = true;
      uint16_t used_len = (ubx_paylen < UBX_PAYLOAD_BUF_SIZE) ? ubx_paylen : UBX_PAYLOAD_BUF_SIZE;
      if (ubx_cls == 0x01) {
        if (ubx_msgid == 0x07) {
          // NAV-PVT: 位置・速度・時刻を解析
          handle_navpvt(ubx_buf, used_len);
          snprintf(last_nmea[stored_nmea_index], NMEA_MAX_CHAR,
            "UBX-NAV-PVT fix=%d sv=%d lat=%.5f", gsa_fixtype, stored_numsats, stored_latitude);
          #ifdef DEBUG_GBX_NMEA
          // デバッグ: 5秒に1回 NAV-PVT の主要値を出力
          {
            static unsigned long last_pvt_dbg = 0;
            if (millis() - last_pvt_dbg > 5000) {
              last_pvt_dbg = millis();
              Serial.print("[UBX] NAV-PVT fix="); Serial.print(gsa_fixtype);
              Serial.print(" sv="); Serial.print(stored_numsats);
              Serial.print(" lat="); Serial.print(stored_latitude, 6);
              Serial.print(" lon="); Serial.print(stored_longitude, 6);
              Serial.print(" alt="); Serial.print(stored_gnss_altitude, 1);
              Serial.print(" gs="); Serial.print(stored_gs, 2);
              Serial.print("m/s hdg="); Serial.print(stored_truetrack, 1);
              Serial.print(" time="); Serial.print(ubx_hour); Serial.print(":"); Serial.print(ubx_min); Serial.print(":"); Serial.print(ubx_sec);
              Serial.print(" valid="); Serial.print(ubx_date_valid?"D":"d"); Serial.println(ubx_time_valid?"T":"t");
              Serial.print(" hAcc="); Serial.print(ubx_hacc_mm); Serial.print("mm gnssOK="); Serial.println(ubx_gnssFixOK?"Y":"N");
            }
          }
          #endif
        } else if (ubx_msgid == 0x35) {
          // NAV-SAT: 衛星情報を解析
          removeStaleSatellites();
          handle_navsat(ubx_buf, used_len);
          #ifdef DEBUG_GBX_NMEA
          {
            static unsigned long last_sat_dbg = 0;
            if (millis() - last_sat_dbg > 10000) {
              last_sat_dbg = millis();
              Serial.print("[UBX] NAV-SAT numSvs="); Serial.println(ubx_buf[5]);
            }
          }
          #endif
          snprintf(last_nmea[stored_nmea_index], NMEA_MAX_CHAR, "UBX-NAV-SAT svs=%d", ubx_buf[5]);
        } else if (ubx_msgid == 0x04) {
          // NAV-DOP: 精度低下率を解析
          handle_navdop(ubx_buf, used_len);
          #ifdef DEBUG_GBX_NMEA
          {
            static unsigned long last_dop_dbg = 0;
            if (millis() - last_dop_dbg > 10000) {
              last_dop_dbg = millis();
              Serial.print("[UBX] NAV-DOP P="); Serial.print(gsa_pdop, 2);
              Serial.print(" H="); Serial.print(gsa_hdop, 2);
              Serial.print(" V="); Serial.println(gsa_vdop, 2);
            }
          }
          #endif
          snprintf(last_nmea[stored_nmea_index], NMEA_MAX_CHAR,
            "UBX-NAV-DOP P=%.1f H=%.1f V=%.1f", gsa_pdop, gsa_hdop, gsa_vdop);
        } else {
          #ifdef DEBUG_GBX_NMEA
          Serial.print("[UBX] unknown NAV cls=01 id="); Serial.print(ubx_msgid, HEX);
          Serial.print(" len="); Serial.println(ubx_paylen);
          #endif
          snprintf(last_nmea[stored_nmea_index], NMEA_MAX_CHAR,
            "UBX-%02X-%02X len=%d", ubx_cls, ubx_msgid, ubx_paylen);
        }
      } else if (ubx_cls == 0x05) {
        // ACK-ACK (01) / ACK-NAK (00)
        #ifdef DEBUG_GBX_NMEA
        Serial.print("[UBX] "); Serial.print((ubx_msgid==0x01)?"ACK-ACK":"ACK-NAK");
        Serial.print(" for cls="); Serial.print((used_len>=1?ubx_buf[0]:0), HEX);
        Serial.print(" id="); Serial.println((used_len>=2?ubx_buf[1]:0), HEX);
        #endif
        snprintf(last_nmea[stored_nmea_index], NMEA_MAX_CHAR,
          "%s %02X%02X", (ubx_msgid==0x01)?"UBX-ACK-ACK":"UBX-ACK-NAK",
          (used_len>=1?ubx_buf[0]:0), (used_len>=2?ubx_buf[1]:0));
      } else {
        #ifdef DEBUG_GBX_NMEA
        Serial.print("[UBX] frame cls="); Serial.print(ubx_cls, HEX);
        Serial.print(" id="); Serial.print(ubx_msgid, HEX);
        Serial.print(" len="); Serial.println(ubx_paylen);
        #endif
        snprintf(last_nmea[stored_nmea_index], NMEA_MAX_CHAR,
          "UBX-%02X-%02X len=%d", ubx_cls, ubx_msgid, ubx_paylen);
      }
      last_nmea_time[stored_nmea_index] = millis();
      stored_nmea_index = (stored_nmea_index + 1) % MAX_LAST_NMEA;
      break;
    }
    default:
      ubx_state = UBX_SYNC1;
      break;
  }
}

// --- リプレイモード ---
// replaymode_gnssoff = true の時、実 GNSS の代わりに SD の飛行 CSV を再生する。
bool replaymode_gnssoff = false;

// 最後に再生した CSV 行。imu.cpp / airdata.cpp のセンサ値オーバーライドから参照される。
static ReplayRow replay_last_row;
static bool replay_last_valid = false;

// --- 再生時計（Core0 専用）---
// 実時間ではなく「仮想の再生経過時間」を積算する方式にしている。
// 毎回の経過分に倍率を掛けて足すため、再生速度の変更も一時停止も、
// 時刻の飛びを起こさずに途中で行える。
static uint32_t replay_virtual_ms = 0;   // 再生開始からの仮想経過時間 [ms]
static uint32_t replay_last_tick  = 0;   // 前回積算したときの millis()
static uint32_t replay_seen_seq   = 0;   // 確認済みの replay_init_seq
static bool     replay_paused     = false;

// 再生の一時停止／再開。設定画面など地図以外を表示している間は停止させる。
// 一時停止中は仮想時刻を進めないだけなので、再開すると続きから再生される。
void replay_set_paused(bool paused) {
  replay_paused = paused;
}

// リプレイ中で、かつ CSV にその項目の列が存在する場合のみ true。
// （v5 のデータは高度・上昇率・気圧の列を持たないので false になり実センサ値へフォールバックする）
bool replay_has_value(uint16_t havebit) {
  return replaymode_gnssoff && replay_last_valid && (replay_last_row.have & havebit);
}
float replay_get_kf_altitude() { return replay_last_row.kf_altitude; }
// 一時停止中は上昇率 0 を返す。停止中は新しい行が適用されないため、
// そのままだと最後に読んだ行の上昇率が保持され続け、バリオが鳴りっぱなしになる
// （特に下降側は連続音のため止まらない）。位置・高度・気圧は停止位置のまま保持する。
float replay_get_kf_vspeed()   { return replay_paused ? 0.0f : replay_last_row.kf_vspeed; }
float replay_get_pressure()    { return replay_last_row.pressure; }
float replay_get_voltage()     { return replay_last_row.voltage; }


// GNSS の時刻は UTC（協定世界時）で送られてくる。
// この関数で日本標準時（JST = UTC+9）に変換する。
// 日付またぎ・月またぎ・うるう年も正しく処理する。
void utcToJst(int *year, int *month, int *day, int *hour) {
  if(*month <= 0 || *month > 12){
    DEBUGW_P(20250424,"month invalid:");
    DEBUGW_PLN(20250424,*month);
    enqueueTask(createLogSdfTask("month invalid:%d",*month));
    return;
  }
  // Add 9 hours to convert UTC to JST
  *hour += 9;
  // Handle overflow of hours (24-hour format)
  if (*hour >= 24) {
      *hour -= 24;
      (*day)++;
  }
  // Handle overflow of days in each month
  int daysInMonth[] = {31, 28, 31, 30, 31, 30, 31, 31, 30, 31, 30, 31};
  // Check for leap year
  bool isLeapYear = ((*year % 4 == 0 && *year % 100 != 0) || (*year % 400 == 0));
  if (isLeapYear) {
      daysInMonth[1] = 29;
  }
  if (*day > daysInMonth[*month - 1]) {
      *day = 1;
      (*month)++;
  }
  // Handle overflow of months
  if (*month > 12) {
      *month = 1;
      (*year)++;
  }
}

// utcToJst() の逆変換（JST = UTC+9 → UTC）。
// PONS の飛行 CSV は JST で記録されているため、リプレイ時に ubx_* へ入れる前に UTC へ戻す。
// 日付またぎ・月またぎ・うるう年も正しく処理する。
void jstToUtc(int *year, int *month, int *day, int *hour) {
  if(*month <= 0 || *month > 12){
    DEBUGW_P(20260731,"month invalid:");
    DEBUGW_PLN(20260731,*month);
    return;
  }
  // Subtract 9 hours to convert JST to UTC
  *hour -= 9;
  if (*hour < 0) {
      *hour += 24;
      (*day)--;
  }
  // Handle underflow of days
  if (*day < 1) {
      (*month)--;
      if (*month < 1) {
          *month = 12;
          (*year)--;
      }
      int daysInMonth[] = {31, 28, 31, 30, 31, 30, 31, 31, 30, 31, 30, 31};
      bool isLeapYear = ((*year % 4 == 0 && *year % 100 != 0) || (*year % 400 == 0));
      if (isLeapYear) {
          daysInMonth[1] = 29;
      }
      *day = daysInMonth[*month - 1];
  }
}

// i 番目に古い NMEA 文字列を返す（i=0 が最新）。
// last_nmea はリングバッファなので、stored_nmea_index を基準に逆算してインデックスを求める。
char* get_gnss_nmea(int i){
  int index = (stored_nmea_index-1-i)%MAX_LAST_NMEA;
  if(index < 0){
    index += MAX_LAST_NMEA;
  }
  return last_nmea[index];
}

// i 番目に古い NMEA の受信時刻を返す（i=0 が最新）。
unsigned long get_gnss_nmea_time(int i){
  int index = (stored_nmea_index-1-i)%MAX_LAST_NMEA;
  if(index < 0){
    index += MAX_LAST_NMEA;
  }
  return last_nmea_time[index];
}


// 30 秒以上 GSV を受信していない衛星を配列から削除する。
// 衛星が地平線以下に沈んだり、受信が途絶えた場合に古い情報が残らないようにするため。
void removeStaleSatellites() {
  unsigned long currentMillis = millis();
  for (int i = 0; i < MAX_SATELLITES; i++) {
    if (satellites[i].PRN != 0 && (currentMillis - satellites[i].lastReceived > 30000)) {
      satellites[i].PRN = 0;  // PRN を 0 にリセットして「空き」とみなす
    }
  }
}


// ゲッター
int      get_gnss_fixtype()    { return gsa_fixtype; }
float    get_gnss_pdop()       { return gsa_pdop; }
float    get_gnss_hdop()       { return gsa_hdop; }
float    get_gnss_vdop()       { return gsa_vdop; }
int      get_gsa_numsat()     { return gsa_numsat; }
int      get_gsa_prn(int i)   { return (i >= 0 && i < GSA_MAX_PRN) ? gsa_prns[i] : 0; }
uint32_t get_gnss_hacc_mm() {
  if (link_mirror_active()) return link_get_hacc_mm();
  return ubx_hacc_mm;                                      // hAcc（水平精度推定値, mm）
}
uint32_t get_gnss_vacc_mm()    { return ubx_vacc_mm; }    // vAcc（垂直精度推定値, mm）
uint32_t get_gnss_sacc_mmps()  { return ubx_sacc_mmps; }  // sAcc（速度精度推定値, mm/s）
float    get_gnss_veld_mps()   { return ubx_veld_mps; }  // GNSS 垂直速度（上昇正, m/s）
// 測位エポック（iTOW, ms）。ミラーは通さない — これは**自機の受信機**が
// いつ測位したかであり、同じ観測の二重利用を防ぐためだけに使う。
uint32_t get_gnss_itow_ms()    { return ubx_itow_ms; }   // NAV-PVT iTOW（GPS 週内時刻, ms）
bool get_gnss_fixok() {
  if (link_mirror_active()) return link_get_fix_ok();
  return ubx_gnssFixOK;                                    // gnssFixOK フラグ
}

// GSV（Satellites in View）NMEA 文を手動パースして satellites[] 配列に衛星情報を格納する。



// GNSS モジュールを「位置取得優先モード」に切り替える。
// GSV（衛星情報）出力を停止することで NMEA の量を減らし、位置・速度の更新レートを上げる。
// 設定画面の GNSS 詳細からメインマップへ戻る際に呼ばれる。
void gnss_getposition_mode() {
  // ナビ画面では NAV-SAT を 0.1Hz（10秒に1回）に落としてトラフィックを抑制
  { const unsigned char cmd[] = UBLOX_NAVSAT_RATE_20;
    for (unsigned i = 0; i < sizeof(cmd); i++) GNSS_SERIAL.write(cmd[i]); }
}

// GNSS モジュールを「星座表示モード」に切り替える。
// GSV を有効化して衛星の仰角・方位・SNR を表示できるようにする。
// GNSS 詳細画面に入る際に呼ばれる。
void gnss_constellation_mode() {
  // 星座画面では NAV-SAT を 1Hz に上げて衛星情報をリアルタイム更新
  { const unsigned char cmd[] = UBLOX_NAVSAT_RATE_2;
    for (unsigned i = 0; i < sizeof(cmd); i++) GNSS_SERIAL.write(cmd[i]); }
}

int setupcounter = 1;  // gnss_setup() の呼び出し回数（1=初回、2以降=リトライ）
uint32_t gnss_current_baudrate = 0;  // GNSS シリアルの現在ボーレート（gnss_setup() で更新）
uint32_t get_gnss_baudrate() { return gnss_current_baudrate; }
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
